dmolinagarcia/nova64/docs/tracks/hid.md

---
layout: track
track: hid
title: "Track · HID"
permalink: /tracks/hid/
redirect_from: /categories/hid
---
