dmolinagarcia/nova64/docs/tracks/memory.md

---
layout: track
track: memory
title: "Track · Memory"
permalink: /tracks/memory/
redirect_from: /categories/memory
---
