dmolinagarcia/nova64/docs/tracks/power.md

---
layout: track
track: power
title: "Track · Power"
permalink: /tracks/power/
redirect_from: /categories/power
---
