dmolinagarcia/nova64/docs/tracks/storage.md

---
layout: track
track: storage
title: "Track · Storage"
permalink: /tracks/storage/
redirect_from: /categories/storage
---
