dmolinagarcia/nova64/docs/tracks/system.md

---
layout: track
track: system
title: "Track · System"
permalink: /tracks/system/
redirect_from: /categories/system
---
