dmolinagarcia/nova64/docs/tracks/video.md

---
layout: track
track: video
title: "Track · Video"
permalink: /tracks/video/
redirect_from: /categories/video
---
