dmolinagarcia/nova64/docs/_drafts/0001-xx-xx-power-button.md

---
categories: power
---

## Power Button

Cmo encendemos apagamos? ATX?

Can I use the soft button from the IP????

It seems I can

>>> Pero.... quiero un boton que no dependa de ningun MCU

Circuito puramente analogico. Un boton enciende (activa el enable de los reguladores)
                              Boton largo apaga (desactiva el enable)

Ademas, el pulsado del botón, se envia como señal al nova, para que invoque un apagado
Y ademas, el nova tiene que tener un power off!

Metemos aqui todo el diseño del boton
