dmolinagarcia/nova64/docs/_drafts/0004-xx-xx-prototype_board.md

---
categories: cpu
---

que necesito para una prototipe?

2 fpga
cpu
2x2 qram
1 sram
all pins exposed

power?
