dmolinagarcia/nova64/docs/docsV3/content/sec_ai_q.md

# Decision log · open questions
> what was decided, why · what's left to close

The decisions shaping the current design, with their reasoning in one line — and the honest list of what's still open.

- D01 — ECP5 → **3× iCE40 TQ144** — BGA isn't hand-solderable; 0.5mm TQFP is. Accepted consequence: 128 Kbit EBR → HW walker + small TLB instead of on-chip tables.
- D02 — [[!superseded by D13/D15]] Main PSRAM **removed**; the 32 MB SDRAM is *the* memory — the QSPI gateware (the trickiest part) disappears, and a cache miss drops from ~µs to ~200–300 ns.
  NOTE: The removal stands and now covers the whole board, but its headline no longer holds: with the SRAM narrowed to 8 bits a fill is back in the µs range (D15). The decision survives on the gateware simplification alone.
- D03 — [[!superseded by D15]] External table SRAM **removed**; a single 2 MB SRAM (cache + tables + pinned) — ~35 pins that didn't fit in the TQ144.
- D04 — Amiga-style shared bus; out goes the dedicated FPGA-to-FPGA link and the eDP bridge — Neon taps the bus with the `$FE` window.
- D05 — Direct RGB-TTL 10.1” panel (ER-TFT101-1) — no bridge chip, no NDA (RTD2556 ruled out due to Realtek firmware). eDP/ANX6345 remains a future variant.
  NOTE: **This choice is size-bound, and that is the thing to know about it.** Parallel RGB-TTL exists only up to roughly 10 inches; from 14 inches upward every panel is a laptop panel speaking LVDS or eDP, and the direct path is simply gone (→ [Q23](sec_ai_q#q23)).
  NOTE: **Half of this decision is now withdrawn and the other half is in dispute.** [D70](sec_ai_q#d70) closes the eDP/ANX6345 variant outright — the bridge has no franchised distribution and no hand-solderable member exists — and replaces it with **LVDS**, which the note above did not consider because it assumed a bridge was the only way off parallel RGB. **What is left open is whether the 10.1-inch module survives as the prototype panel** while [sheet U1](sec_ai_u1) describes the production one, or whether it is superseded outright (→ [Q145](sec_ai_q#q145)).
- D06 — [[!superseded by D13/D35]] 512×300 → 1024×600 px-doubling — the framebuffer fits within the video PSRAM's budget and its QSPI bandwidth.
  NOTE: **Closed by [D35](sec_ai_q#d35).** Px-doubling is no longer a property of the machine: it is **Mode 2b**, one of three video modes, with 2×2 replication filling the panel exactly. The GUI gets native 1024×600 in Mode 1 and games get replication in Mode 2, instead of every subsystem paying for one compromise (→ [T1.33](sec_ai_t1#t133)).
- D07 — USB-only HID — out go PS/2 and keyboard matrix. Capacitive GT911 touch: the resistive option needed 4 ADCs the EC doesn't have free.
  NOTE: **The mechanism underneath it changed and the decision did not.** REV A put the host on the EC's PIO blocks because the RP2040 had no hardware host controller; the RP2354B has one, and the bit-banged stack leaves the critical path along with the pin-placement rule it imposed ([D1.8](sec_ai_d1#d18), [D1.9](sec_ai_d1#d19)).
- D08 — SD as the only boot path; dedicated BIOS flash **removed** — incompatible with the pin budget after adding the SDRAM. **Superseded by [D60](sec_ai_q#d60)**: the conclusion that no *dedicated* flash is affordable still holds, but the EC's in-package flash turned out to have room for the BIOS and all three bitstreams at zero BOM cost, so the SD is no longer any part of the boot path.
- D09 — Boosts (backlight, host VBUS) hanging off SYS, not VBAT — the machine runs on USB with the battery depleted. VPP 2.5V via BAT54: out goes the dedicated rail.
  NOTE: Both halves survive REV C, the second with its footing changed: the BAT54 now hangs off **3V3_MAIN**, which rises after the cores, so the iCE40's `VPP_2V5` ordering is satisfied by construction instead of being violated by it (→ [D20](sec_ai_q#d20)).
- D10 — Full 2 KB paging per process (out goes the "one bank per process" model) — a tractable 32 KB flat table, decoupled from the cache's 256 B fill granularity.
- D11 — Hardware walker instead of a software trap on TLB miss — with 10 ns SRAM it costs ≈100 ns and simplifies the kernel.
- D12 — 32-bit PTE with a 16-bit frame from day one — 128 MB ceiling with no format migrations. 16 rather than the 15 bits the pool needs is free: the flags occupy exactly 16 bits, so the other half-word was going unused, and the clean split lets the walker read 32 bits and take the low half as address and the high half as permissions with no shifting or masking (→ [sheet K](sec_ai_k)).
- D13 — PSRAM eliminated from the **entire board**, Neon's framebuffer included — every QSPI interface disappears with it. Neon gets its own 64 MB SDRAM instead: same part, same footprint, same controller as Helium's.
  NOTE: Streaming pixels across a link would need ~26 MB/s sustained with hard deadlines and would make Helium the bottleneck for the whole machine. A second SDRAM device costs the same pins as any smaller memory and buys double buffering at 16 bpp.
- D14 — SDRAM sized at **64 MB per device** (AS4C32M16SB-7TIN, 512 Mbit) — the ceiling of SDR silicon in volume; no 1 Gbit part exists. The 256 Mbit W9825G6KH stays as a drop-in fallback on the same footprint. **The second device is deliberately not populated**: at 8 MHz the 65816 sustains ~4 MB/s, so merely zeroing 64 MB takes ~16 s. A second /CS is routed to an empty footprint.
- D15 — SRAM narrowed to **1 MB ×8** with D0–D7 *and* A0–A10 shared with the CPU nets — 13 pins instead of 41, which is what makes the budget close at 90/107. Possible only because A0–A10 are the untranslated page offset (→ [F.2](sec_ai_f#f2)). Accepted costs: Helium can no longer reach the SRAM alone, walks cost four accesses instead of two, and the shared nets carry three loads.
- D16 — Cache misses handled by **stalling PHI2 low**, not by ABORT — the W65C816S core is fully static and the WDC datasheet sanctions holding the clock indefinitely. ABORTB is retained for genuine protection faults only, which removes the frequent case from the most delicate path on the chip.
  NOTE: Clock gating was also preferred over the RDY pin for a specific reason: RDY is reported to be ignored during write cycles on some revisions, a 6502 NMOS inheritance. Gating the clock sidesteps the question — with PHI2 stopped the CPU is not in any state at all, rather than in one whose rules depend on the cycle type.
- D17 — The SRAM is a **hardware cache with tags**, never a tier of allocatable frames — migrating a page would force hardware to rewrite PTEs, which `mshare` and TLB coherence make impossible (→ [L.3](sec_ai_l#l3)). 768 KB of 4-way cache in 2 KB lines with 256 B sub-blocks, plus 256 KB fixed and uncached.
- D18 — Debug access goes through a **debug agent inside Helium**, commanded by the RP2354B over a dedicated SPI chip select — the EC never masters the system bus. Pins (mastering needs ~32 lines the EC does not have), reuse (Helium already owns every memory controller) and coherence (an external master reads stale data past a dirty sub-block) all point the same way, and the agent's own registers stay **out of bank `$FF`** so the privileged path cannot be reached by the software it can bypass (→ [sheet R](sec_ai_r)).
  NOTE: Helium also drives `BE` as part of this: the bus handoff has to be a synchronous transition inside one clock domain, not a race across the SPI link. Closes [Q25](sec_ai_q#q25).
- D19 — **3V3 split into an always-on rail and a switched one** — the decision the rest of the power revision hangs from. A controller cannot switch the rail that powers it, so REV B's single 3V3 made EC power management impossible in principle rather than merely unimplemented. Accepted costs: one extra converter, and a domain boundary that has to be honoured net by net (→ [C.2](sec_ai_c#c2), [C.13](sec_ai_c#c13)).
- D20 — **1.2 V becomes a buck sourced from SYS**, not an LDO off 3V3. Two problems fall out together: the iCE40 wants VCC before VCCIO and an LDO off 3V3 guarantees the opposite, and dropping 3.3 → 1.2 V linearly at 250 mA burned ~0.5 W as heat in a SOT-23-5 on a battery machine. ~0.6 W recovered, and the ordering becomes structural rather than a firmware promise (→ [C.8](sec_ai_c#c8)).
  NOTE: The rejected mitigation is worth recording so it is not proposed again: **holding `CRESET_B` low does not make a rail-order violation safe.** It prevents configuration, not conduction through the I/O clamps into an unpowered core rail.
- D21 — **MCP73871 → BQ25896 + CH224K**, and the pack to 2× 5000 mAh in parallel. The pack grew to ~10 Ah and linear charging at that current is not viable; a switching charger at 90–92 % with a programmable SYS floor and an integrated ADC also hands the EC rail telemetry for free. The CH224K negotiates **9 V** — not 12 V, which leaves no headroom under the charger's 14 V input OVP.
  NOTE: The charger's **OTG boost cannot replace the TPS61023** for the host port, and an earlier proposal that it could was wrong twice over: the boost drives VBUS, the same physical node as the USB-C input, and it only enables while unplugged (→ [C.5](sec_ai_c#c5)).
- D22 — **Two level-held pins plus the existing SPI link** for the CPU↔EC power handshake: the pins carry attention, SPI carries the reason. A single wire encoding poweroff, reboot, ack and refusal by pulse width would be a bug source on a board where both endpoints are also under test. Costs 2 of Helium's spare I/O, onto a budget that does not close (→ [Q8](sec_ai_q#q8), [S.2](sec_ai_s#s2)).
  NOTE: `POWER_CTRL` is also the one register that departs from the "address as opcode" model of [M.2](sec_ai_m#m2) — a small closed enumeration with no arguments is cheaper to decode by value than to spread over eight addresses. The departure is deliberate and confined to this block.
- D23 — **No `sys_poweroff()`.** Power management adds nothing to the syscall table; it is `/dev/power` and an `ioctl`, and the privilege check comes free from the device node's permissions rather than from a bespoke gate. A single-purpose syscall in a table otherwise built from general primitives would have been the first crack in the rule (→ [S.11](sec_ai_s#s11), [J.4](sec_ai_j#j4)).
- D24 — **Battery telemetry as double-buffered registers inside Helium**, staging → live → shadow, each copy a single cycle. Two cheaper designs were rejected: a **seqlock**, which moves retry logic onto the constrained CPU with no hard bound; and letting the EC **write telemetry into SRAM** over the debug agent's bus path, which would make battery reporting depend on the cache controller and the arbiter — the one thing the power subsystem is specified not to do (→ [S.16](sec_ai_s#s16)).
- D25 — [[open]] **The power registers sit outside the `DEBUG_ENABLE` gate** — for as long as there is a gate ([Q125](sec_ai_q#q125)).  Shutdown and battery reporting are production functions; gating them behind the debug strap would break them on every board built with debug disabled. They are read-only from SPI and cannot initiate a bus cycle, so the exception grants nothing the strap exists to withhold (→ [R.18](sec_ai_r#r18)). **If [Q125](sec_ai_q#q125) removes the strap this entry has nothing left to except them from**, and the always-accessible region of [Q38](sec_ai_q#q38) becomes simply the register map.
- D26 — **Neon is specified in full** — three video modes, a blitter, a command processor executing display lists out of its own SDRAM, and a resource budget that closes at 77 % of the device ([sheet T1](sec_ai_t1)). It reconciles REV A against this board, which differs from what REV A assumed in four places: the reference clock, the SDRAM size, the existence of `NEON_BUS_BSY`, and where the interrupt goes.
- D27 — **Mode 0's text buffer and font live in Neon's block RAM, initialised from the bitstream** — not in video memory, and not loaded by anything. 8 KB plus 4 KB of the 16 KB available, which is expensive; it buys a machine that displays a correct screen the moment `CDONE` rises, with no SDRAM controller, no arbiter, no FIFO and no CPU in existence. **The console is therefore available as the debugging instrument for every subsystem built after it**, which is the whole argument (→ [T1.1](sec_ai_t1#t11), [T1.29](sec_ai_t1#t129)).
- D28 — **One clock domain inside Neon, at 103.125 MHz**, with the pixel stage on a clock enable every second cycle and `PCLK` out through a DDR register. No clock-domain crossing anywhere, so no synchroniser FIFO between scanout and memory and an entire class of intermittent failure removed. **The second PLL is freed** and has two claimants, audio and the VGA bring-up clock (→ [T1.8](sec_ai_t1#t18), [Q54](sec_ai_q#q54)).
  NOTE: REV A's 102.000 MHz is unreachable from this board's 25 MHz oscillator; 103.125 is the nearest legal PLL setting and the vertical total moves 635 → 640 to land back at ~60 Hz (→ [Q43](sec_ai_q#q43)).
- D29 — **No hardware tile engine and no sprite engine.** The blitter redraws a full 320×200 tilemap in ~1.3 ms, under 8 % of a frame, and blits 32 masked 16×16 sprites in ~0.12 ms; hardware sprites exist to avoid save/restore of background on machines that cannot afford to redraw, and with double buffering and 64 MB that problem does not arise. **Saving ~1,650 LUT, about 21 % of the device** — which is what takes Neon from 95 % occupancy, not routable once audio grows, to 77 %. **The hardware cursor is retained**, because a GUI pointer must track the mouse independently of the rendering loop (→ [T1.44](sec_ai_t1#t144)).
  NOTE: The trade is real and is recorded so it is not re-litigated. What is given up: sprites composited at scanout cost no framebuffer bandwidth and cannot be erased by drawing. What is gained: one rendering model instead of two incompatible paths, and the logic budget to fit the blitter, the command processor and audio on one device.
- D30 — **Blitter commands carry `(x, y)` coordinates, not 24-bit addresses.** Computing `base + y × stride + x` on the 65816 is a shift-and-add per object per frame on a CPU with no multiplier — precisely the work this architecture exists to remove. Neon does it instead, at one sequential multiply per command, ~16 clocks and ~80 LUT. The consequence is larger than the cause: **a destination becomes one 32-bit word, so moving an object is a single patch to an existing display list**, which is what makes per-frame CPU cost ~180 bytes instead of several milliseconds (→ [T1.42](sec_ai_t1#t142)).
- D31 — [[!superseded by D36]] **Neon's registers live at `$FE:FF00`, inside the aperture, not in bank `$FF`.** Neon already decodes bank `$FE`; giving it a second window in the privileged bank would cost a decode in Helium and a wall on [Q22](sec_ai_q#q22) for nothing.
  NOTE: The half of this that survives is the **palette**, which stays in the aperture at `$FE:8000` with 256 entries — it is bulk data, written a kilobyte at a time, and nothing about it is privileged (→ [T1.49](sec_ai_t1#t149)). The half that was wrong is "for nothing": a second window buys the protection property of [D36](sec_ai_q#d36), which is not nothing.
- D32 — **`PEEK` is deleted; the graphics aperture is readable.** REV A made it write-only, with a slow address/data register pair for diagnostic reads, on the premise that Neon could not stall the CPU. **`NEON_BUS_BSY` already exists** ([B.6](sec_ai_b#b6)) and stalls PHI2 across the row activation, so a read simply works at a few hundred nanoseconds — about six times faster than the mechanism it replaces, and with no register file to build. Its protocol is [D37](sec_ai_q#d37). **The software model is still written as though the aperture were write-only**, because nothing in the design needs to read pixels and anything that does will run at aperture speed (→ [T1.15](sec_ai_t1#t115), [T1.16](sec_ai_t1#t116)).
- D33 — **Backlight `EN` and PWM belong to the EC, not to Neon.** The EC is awake before Neon is configured and while the switched domain comes down, and it already owns every rail enable. Closes [Q6](sec_ai_q#q6) and returns two pins to a budget that needs them (→ [T1.52](sec_ai_t1#t152)).
- D34 — **Neon's interrupt goes to Helium's PIC, not to the CPU's `IRQB`.** Masking and priority come free from a controller that already exists, the CPU keeps one interrupt entry path, and it is one pin on each FPGA rather than a wire into the socket. Vblank, raster compare and the display list's `SIGNAL` are aggregated inside Neon and demultiplexed by the kernel reading `IRQ_STATUS` (→ [T1.47](sec_ai_t1#t147)).
- D35 — **Px-doubling becomes Mode 2b.** What [D06](sec_ai_q#d06) proposed as a global policy — draw at 512×300, emit every pixel twice — returns as one mode among three, with 2×2 replication filling the panel exactly. Mode 1 gives the GUI native 1024×600 at 1 bpp and Mode 2 gives games replication at 8 bpp, so no subsystem pays for another's compromise. Supporting 2b alongside 2a costs approximately nothing in logic: it is a register field driving the replication counters and the line stride (→ [T1.33](sec_ai_t1#t133)).
- D36 — **Neon's registers live in bank `$FF`, at `$FF:8000`–`$FF:80FF`**, and bank `$FF` gains its first off-chip tenant. It reverses [D31](sec_ai_q#d31), which had put them inside the `$FE` aperture, and it does so for a reason that outranks the tidiness argument on both sides: **`$FE` is user-mappable and `$FF` is not.** A process granted a framebuffer mapping could otherwise reach `LIST_BASE` and `CMD_CTRL.LIST_RUN` and aim the command processor — which reads and writes the whole 64 MB with no MMU in front of it — anywhere it liked. D31 could only answer that with a rule the mapping ioctl had to remember; **this makes it a property of the architecture**, putting Neon's control surface behind the same wall as the MMU's (→ [T1.21](sec_ai_t1#t121), [J.5](sec_ai_j#j5)).
  NOTE: **It costs no pins and no new mechanism.** Neon already taps A0–A15 and already captures the bank byte off D0–D7 during PHI2 low, so recognising a second bank is the same comparator with a different constant, and `NEON_BUS_SEL` simply broadens to mean "Helium has validated this cycle for Neon" across both windows (→ [B.6](sec_ai_b#b6)).
  NOTE: **The base is `$FF:8000` so Helium's decode is one address bit** — "A15 set in bank `$FF` ⇒ not mine" — rather than a range comparison. Helium keeps `$FF:0000`–`$FF:7FFF` whole, so the block allocation [Q22](sec_ai_q#q22) still owes can proceed with no risk of colliding with Neon later. The genuinely new gateware is small and specific: **Helium must release D0–D7 on a read in that window**, which is the same turnaround an `$FE` read already performs, and **Neon must gate on the strobe rather than on the address alone** — ABORTB cancels an instruction on the CPU, it cannot un-write a register on the far side of the bus. No stall is needed: the file is fabric registers and answers inside the PHI2 high phase (→ [T1.23](sec_ai_t1#t123)).
- D37 — **The CPU can read VRAM, through a bus-busy stall — and the protocol is "stall first, ask afterwards".** `NEON_BUS_SEL` selects Neon's bus; while `NEON_BUS_BSY` is asserted Helium holds PHI2 **low**; when Neon deasserts it the data is in Neon's output register and Helium raises the clock. The alternative — Neon asserting a wait line fast enough to hold off the rising edge — is a race inside a ~62 ns low phase across an asynchronous inter-FPGA crossing, and it is unnecessary: **Helium decodes the bank itself, so it knows a read of `$FE` is in progress without being told.** It stalls unconditionally and the race disappears (→ [T1.18](sec_ai_t1#t118), [B.6](sec_ai_b#b6)).
  NOTE: **Stalling low rather than stretching the high phase is what keeps it cheap.** Extending the high phase would need a fresh datasheet reading on holding a static W65C816S with the clock high, which nobody has done; stalling low reuses the exact clock gate Helium owns for cache fills and the permission [D16](sec_ai_q#d16) already established. It also falls out right on the bus, since D0–D7 carries the bank byte while PHI2 is low and Neon therefore must not drive then.
  NOTE: **Four requirements travel with the decision**, and the first would otherwise ship as an intermittent bug. **A read drains the write FIFO before it is issued** — writes are posted, so a read that overtakes a pending write returns the previous contents, failing according to arbiter load, which means "read back what was written" would pass almost every time. **The arbiter bounds the wait** — a row activation is ~60 ns and irrelevant, a read queued behind a whole blitter operation is up to 1.5 ms with the CPU clock stopped (→ [Q29](sec_ai_q#q29)). **Helium's fill watchdog covers the path** (→ [F.11](sec_ai_f#f11), [Q57](sec_ai_q#q57)). And **the software model stays write-only**, because the restriction was doing real work: it is why save-under is a blitter copy and why assets flow one way (→ [T1.19](sec_ai_t1#t119)).
  NOTE: **The same wire serves Helium with no clock involved.** When the debug agent reads VRAM through an external cycle, `BE` is low and there is no PHI2 to stall — Helium just waits for busy to clear before sampling D0–D7. `NEON_BUS_BSY` is a ready line that Helium *happens* to use to gate PHI2 when the requester is the CPU. And it is less slow than it sounds: a read loop runs at ~70 % of the speed of the same loop against SRAM, because the bottleneck is the 65816, not the SDRAM (→ [T1.19](sec_ai_t1#t119)).
- D38 — **Neon's SDRAM is partitioned by function across its four banks**, and this is a first-order decision rather than an allocator preference. Banks 0 and 1 hold the front and back framebuffers, bank 2 the even-numbered window backing stores, bank 3 the odd ones plus the font atlas, icon sheets and audio buffers. **The invariant is that during composition the blitter's reads, its writes and scanout are always in three different banks**, so every ACTIVATE is issued inside another bank's data phase. Collapse it and delivered bandwidth halves, from ~160 to ~80 MB/s — a 2D blit crosses a stride at every line boundary, and a shared bank turns each crossing into a PRECHARGE plus ACTIVATE that overlaps with nothing (→ [T3.16](sec_ai_t3#t316)). **Closes [Q50](sec_ai_q#q50).**
  NOTE: Two obligations come with it. The **controller must map the bank bits to the high address bits**, or the partition cannot be expressed as an address range at all — the obvious alternative of interleaving banks on low bits to spread sequential traffic would destroy the whole policy. And **the kernel's VRAM allocator is no longer free to place a surface wherever it likes**; the partition is part of the interface, not an optimisation it may ignore.
- D39 — **Neon's arbiter is fixed-priority — refresh, scanout, audio, CPU, blitter — with preemption only at burst boundaries and a minimum burst of 8 words.** Scanout is not merely favoured but *shown* to be safe: worst case 23 clocks, **223 ns**, against a 512-word FIFO that a stall of that length drains by 5.8 words. This is the inverse of the Amiga's `BLTPRI`, which let the blitter starve the CPU; here the blitter can starve nothing. **Placing the CPU above the blitter is also what bounds [D37](sec_ai_q#d37)'s read stall** — a read waits for one burst, never for a whole blit (→ [T3.25](sec_ai_t3#t325), [T3.27](sec_ai_t3#t327)). **Closes [Q57](sec_ai_q#q57) and the Neon half of [Q29](sec_ai_q#q29).**
  NOTE: The margin is the point rather than the number. If the clock falls to 51.5625 MHz under [Q44](sec_ai_q#q44)'s fallback, if the burst grows, if audio's demand doubles, the stall stays two orders of magnitude inside the FIFO. **A real-time guarantee resting on an unverified estimate is not a guarantee**, and a scanout underrun has no degradation mode — the line is simply corrupt.
- D40 — **A prototype board is inserted before the target board**, and it is the first schedule decision this log has had to record. Helium and Neon are merged into one ECP5 on a commercial Colorlight i9 module with the CPU, SRAM, EC, VGA and audio on a carrier of our own, so the whole software roadmap runs on real gateware while the KiCad capture proceeds in parallel. **The blocked dependency was serial and is now two tracks**: [Q1](sec_ai_q#q1)'s missing panel datasheet stops the schematic and stopped everything behind it, and it stops nothing on the carrier. Accepted cost: one board that is thrown away, and a discipline section — [P2.12](sec_ai_p2#p212)–[P2.18](sec_ai_p2#p218) — that has to be enforced at every merge or the prototype becomes a rewrite (→ [sheet P2](sec_ai_p2)).
  NOTE: **[D73](sec_ai_q#d73) puts a third phase in front of this one.** A Spartan-6 training rig now precedes the carrier, so what this decision describes is Phase 1 of three rather than the first hardware the project touches. The reasoning is unchanged and the rig gates nothing ([sheet P1](sec_ai_p1)).
  NOTE: The reason the trade is worth taking is asymmetric, not marginal. A gateware defect found on the carrier costs a bitstream rebuild; the same defect found after E1.3 costs a board spin, and the parts of the design most likely to carry defects — MMU, cache, arbiter, blitter, compositor — are precisely the parts that need no board-specific silicon to exercise.
- D41 — **One i9 module, not two.** Two modules would give Helium and Neon separate SDRAM, which is the target topology, but each is locked at 8 MB with no expansion path and the pair doubles cost, carrier complexity and the inter-module wiring. One module reaches the same software milestones, and the topology difference is handled where it belongs — as a leak-table row and [P2.15](sec_ai_p2#p215)'s memory-port abstraction, which is a discipline problem rather than a hardware one.
- D42 — **VGA through an R-2R ladder, not HDMI.** An earlier costing attributed an HDMI connector to the i9 extension board; it belongs to a Muse Lab board for the i5, a different product. The correction is an improvement rather than a loss: a TMDS encoder is 400–600 LUT of gateware that the target board deletes, whereas 6-bit-per-channel VGA is 20 pins from a budget with 24 spare and lands on **exactly the 18-bit palette entry the target panel takes** ([D05](sec_ai_q#d05), [P2.16](sec_ai_p2#p216)). One less thing built here that has to be unbuilt there.
- D43 — **The prototype carries the target's 1 MB ×8 SRAM, not a ×16 part.** An earlier costing for the carrier specified an IS61WV102416 with UB/LB. That re-widens what [D15](sec_ai_q#d15) deliberately narrowed and would have the carrier rehearse a byte-lane topology the target does not have — while claiming, in the same paragraph, to be rehearsing the shared-net trick of [F.2](sec_ai_f#f2) that only exists because the part is ×8. The AS7C38096A-10TIN of [F.5](sec_ai_f#f5) goes on both boards.
- D44 — **Mode 0 geometry stays 128 × 32 on both boards; the prototype letterboxes instead of reflowing.** At 640 × 480 the console shows an 80 × 30 window into the same buffer, with [T1.25](sec_ai_t1#t125)'s `TEXT_START + text_row*128 + column` unchanged; at 1024 × 600 all 128 columns fit exactly and the 32 rows sit inside a vertical border. **Making the geometry a synthesis parameter was the alternative and was rejected**: it adds a configuration axis the target never uses, and it forces the console driver and every scrollback consumer to ask the hardware how wide the screen is (→ [P1](sec_ai_p2#p1)).
- D45 — **The SPI-SD controller gets a register block of its own, with two data paths and a plain register file rather than address-as-opcode.** The card is unreachable from software until it has one, and the shape of it follows from what it has to carry: LBA, a physical destination and status are **state that persists between commands**, which is exactly the case [M.2](sec_ai_m#m2)'s address-as-opcode convention does not cover — that convention applies to the four triggers, whose argument is a block count, and to nothing else. Both a **FIFO path** and a **DMA path** are specified, because the FIFO reaches [E6](sec_ai_p3#e6) without touching the arbiter or the cache and demand paging cannot use it: 512 bytes through the accumulator is ~440 µs of CPU at 8 MHz against 164 µs of SPI, and a FIFO-only design retracts [G.1](sec_ai_g#g1)'s reason for putting the card behind Helium in the first place. Card initialisation stays in software behind a raw-command register, per [B.2](sec_ai_b#b2) (→ [sheet G](sec_ai_g)).
  NOTE: **The DMA path is what forces `CACHE_INVAL_FRAME` into [sheet M](sec_ai_m)**, and that command is the part of this decision most likely to be skipped by whoever writes the gateware first. Helium acquires a second bus master writing SDRAM behind a write-back cache, and the dirty line left over the destination frame is not a staleness bug but a delayed overwrite of correct data (→ [M.12](sec_ai_m#m12), [G.9](sec_ai_g#g9)).
- D46 — **The expansion slot is a second instance of the inter-device contract, not a second bus.** A card gets `/EXP_SEL_n`, `/EXP_BSY` and `/EXP_IRQ`, [T1.18](sec_ai_t1#t118)'s stall-first read protocol and [F.11](sec_ai_f#f11)'s watchdog — the same shape Neon has, which is what [Q56](sec_ai_q#q56) chose the names for. **One polarity is deliberately reversed**: `/EXP_BSY` idles *not busy*, because busy-by-default in a slot means a machine with nothing plugged in does not boot, and the race that polarity was defending against is killed instead by a mandatory stall window before Helium starts sampling. Cost: **three pins for the first slot, one for each after it**, with the bank byte demultiplexed by a '573 on the board and the slot buffered off the CPU nets by a '245 — both of which cost packages rather than FPGA pins (→ [sheet X](sec_ai_x), [X.11](sec_ai_x#x11)).
- D47 — **A card is reachable in two spaces and neither costs a pin.** Control is a 256-byte window in bank `$FF`, which inherits [L.10](sec_ai_l#l10)'s keystone — no card in any slot is reachable from user code by construction — with Helium decoding the window and the card decoding inside it, exactly as [T1.21](sec_ai_t1#t121) splits Neon's. Bulk is a **1 MB aperture per slot carved out of the frame numbers [F.10](sec_ai_f#f10) deliberately leaves unpopulated**, so a PTE can name a card with the TLB and the permission bits still in front of it; the address reaches the connector on A11–A19, which Helium already drives and which are idle while the SRAM's `/CE` is ([F.2](sec_ai_f#f2)). Aperture frames are non-cacheable and the gateware enforces it rather than trusting the PTE flag (→ [X.8](sec_ai_x#x8), [X.9](sec_ai_x#x9)).
- D48 — **No third-party bus mastering, and the reason is coherence rather than arbitration.** [M.12](sec_ai_m#m12)'s rule — invalidate before a read into memory, flush before a write out of it — is honourable by Helium's own SD engine because Helium owns the cache, and is not honourable by a card somebody else designed. DMA stays a privilege of the northbridge; `/EXP_BR` and `/EXP_BG` are routed to the connector and left unconnected at the FPGA, in the same spirit as [F.10](sec_ai_f#f10)'s unpopulated second `/CS` (→ [X.16](sec_ai_x#x16)).
- D49 — **The slow tier is a third I2C bus with Helium as its only master, and its windows are mirrors rather than proxies.** `I2C-EXP` avoids multi-master arbitration on either existing bus — [C.13](sec_ai_c#c13)'s R3 forbids a bus with two masters, not a third bus — and its two pins have been in [Q8](sec_ai_q#q8)'s allocation since before the split left them without a device. A window cannot perform the transaction on demand: a byte over I2C is ~90 µs at 100 kHz against a 125 ns bus cycle, three orders of magnitude past what [M.6](sec_ai_m#m6) permits to stall PHI2. So each window is a copy in block RAM refreshed by a sequencer, using **[S.16](sec_ai_s#s16)'s staging → live → shadow mechanism with a device table in front of it** — the atomicity and staleness properties come along unchanged (→ [X.23](sec_ai_x#x23), [X.24](sec_ai_x#x24)).
- D50 — **The embedded controller becomes a single RP2354B, and what makes it the right part is what it deletes rather than what it adds.** **48 GPIO** retires the MCP23017 that [D1.6](sec_ai_d1#d16) needed and with it the awkward question of which power domain an expander driving always-on enables belongs to ([Q41](sec_ai_q#q41)). **2 MB of flash inside the package** removes a component from the always-on rail and a net from the board. **A hardware USB host controller** removes the bit-banged PIO stack from the critical path, along with its rule that `D+` and `D−` sit on consecutive GPIOs. The cost is paid in one place and paid fully: **committing the native controller to host mode makes `BOOTSEL` over USB structurally unavailable**, because a USB-A receptacle sources VBUS and reaching it from a PC would need two supplies opposing each other — so the one recovery path that needed no header is replaced by three that need no USB (→ [sheet D1](sec_ai_d1), [D1.9](sec_ai_d1#d19), [D1.13](sec_ai_d1#d113)).
  NOTE: The console follows the port. There is no device-mode USB, so the USB-CDC half of [R.19](sec_ai_r#r19)'s mirrored console is gone and the console is the UART on `J-DBG` — the same 5-pin header that carries SWD, serviced by one probe over one cable.
- D51 — **NVFS breaks its own format rather than keeping ordering discipline, and the break is accepted on the strength of five changes.** A **journal** replaces write ordering, because ordering is a correctness argument spread across every mutating operation — which is where draft 2's crash harness found its bugs — and a journal is one argument in one place, with idempotent single-pass recovery on a machine that has no on-target `fsck`. A **2048-byte block equal to the MMU page** makes demand-paging an executable exactly one block read and every index a shift. **Extents** remove the indirect-block read at ~2.5 ms each. **Fixed 64-byte directory slots** remove the in-band length field that is the largest single source of directory corruption in this class of filesystem — a cost [Y3.10](sec_ai_y3#y310) still pays. And **POSIX-identical mode and type encodings** remove every translation table from both drivers and from the layer above. The price is `mkfs`, `nvfsck` and the read-path driver rewritten, and every existing volume evacuated by copy (→ [sheet Y2](sec_ai_y2), [Y2.1](sec_ai_y2#y21)).
  NOTE: **One action has to happen before any draft 3 code is written**: tag and archive the draft 2 tooling, because evacuating a draft 2 volume depends on it and there will be no way to reconstruct it afterwards.
- D52 — **The media contract: one MBR primary partition of type `0x7F`, starting at an LBA that is a multiple of four, and no wear levelling of our own.** `0x7F` is the byte reserved for local and experimental use; **`0x7A` and `0x7B`, which an earlier draft proposed, are unsafe** — they are the hidden-variant aliases of two FAT16 types under the +`0x10` convention, so some host tools would silently treat an NVFS partition as a hidden FAT. The alignment makes one NVFS block exactly four sectors, and `mkfs` **refuses** an unaligned partition rather than working around it, because working around it turns every transfer into two. Erase-block management and wear levelling belong to the card's own translation layer, and NVFS issues no discard (→ [Y2.25](sec_ai_y2#y225)).
- D53 — **A VFS layer exists, and it is specified before the second filesystem is implemented rather than after.** Introducing it now costs one module and a mechanical rework of NVFS's call surface; introducing it after ext2 costs the same rework twice plus a syscall layer that has already grown branches. Its shape is decided by what neither driver can do: **`lookup` returns an identifier and never a vnode**, because a driver cannot know what is cached or what mount is grafted onto the result; **path resolution, symlink following and mount crossing are VFS-owned**, because neither driver can see across a mount boundary; and **the vnode cache is VFS-owned**, because two copies of one inode diverge silently on append and the logic is identical in both drivers. **The locking discipline is written now and compiles to nothing until the Amiga milestone** — retrofitting locking into a vnode cache fails intermittently rather than cleanly (→ [sheet Y1](sec_ai_y1)).
- D54 — **ext2 is the interoperability format and is a transfer medium, not the system volume.** Chosen over FAT32 for reasons that are all about this CPU: **little-endian on disk**, so every field is a direct load with no byte-swap path; a small documented structure set with no chain to walk; a real directory tree with permissions, links and symlinks; and no long-filename encoding layer. **The recommendation is read-only** — gates [E2.0](sec_ai_y3#e20) and [E2.1](sec_ai_y3#e21) — because that covers the actual use case at roughly a quarter of the cost and with none of the corruption risk, while the write path adds the allocators, truncation, the counter invariants and the whole ordering discipline ext2 has no journal to replace (→ [sheet Y3](sec_ai_y3), [Q101](sec_ai_q#q101)).
- D55 — **One block cache below the VFS, not one per driver, with a sequence-number hook for the journal.** Two caches means two pools sized by guesswork, no global LRU, and one mount's buffers idle while the other thrashes. Uniform 2048-byte buffers, of which an ext2 mount uses half — 50 % waste while an ext2 mount is active, accepted because ext2 is a transfer medium and a two-size allocator costs more code than the memory it saves. **A `commit_seq` per buffer and a `flushed_seq` per mount** stop a global LRU from writing a metadata block back before its journal record has committed, which a naive shared cache would do at an arbitrary moment and break silently. Four bytes per buffer and one comparison in the eviction path (→ [Y1.14](sec_ai_y1#y114), [Q91](sec_ai_q#q91)).
- D56 — **The filesystem stack is prototyped on a host PC before it is written for this machine, as a third series that blocks nothing.** Three filesystems behind one internal table is the cheapest way to discover what [D53](sec_ai_q#d53)'s interface actually has to be, and a bug found under a debugger and a sanitizer is a bug not found on a 65816 with a serial console. **FAT32 first, then ext2, then NVFS; every read path before any write path** — so that a bad decision in the shared layers is caught before it has been baked into three write paths (→ [Y4.2](sec_ai_y4#y42), [sheet Y4](sec_ai_y4)).
- D57 — **The debug and programming port is an on-board RP2040 CMSIS-DAP probe on a chassis USB-C receptacle, not a header and not an FTDI bridge.** The EC's only USB controller is host ([D1.9](sec_ai_d1#d19)), so there was no path from a development PC to the EC at all; an internal header keeps the machine open on the bench, and **the FT2232H was rejected on evidence** — SWD is not native to MPSSE, RP2350 needs SWD *multidrop*, and OpenOCD lists multidrop support for CMSIS-DAP specifically. The failure mode of being wrong is a fabricated board with a dead debug port and no other way in ([D2.2](sec_ai_d2#d22)).
  NOTE: The recursion objection — the probe's own firmware could be corrupted — was overstated: **the RP2040 bootrom is mask ROM**, so `BOOTSEL` and USB enumeration always work whatever the probe's flash holds. The recursion has a hard floor and it is a better one than an FTDI part that may not enumerate a DAP ([D2.3](sec_ai_d2#d23)).
- D58 — **The probe is powered from the debug port's VBUS and the two supply domains never touch.** A probe that depends on a rail of the machine under repair cannot serve the case that justifies it. `3V3_PROBE` and `3V3_AON` are never tied, diode-OR-ed or bridged; **exactly six nets cross, over a common unsplit ground**, and the EC's UART TX — the only line pointing from the machine into the probe — is **held Hi-Z until `DBG_VBUS_SENSE` says a probe is powered**, because probe-absent is the machine's normal state and 16 mA of continuous backfeed is not ([D2.13](sec_ai_d2#d213), [D2.14](sec_ai_d2#d214)).
- D59 — **Tier 3 is demoted from recovery path to bring-up diagnostic, tier 2 is deprioritised, and the `J-QSPI` header becomes test pads.** Tier 1 recovers a blank flash, a corrupt flash, an unpowered machine and a self-resetting one, which leaves tier 3 almost no recovery territory — what it keeps is the E0 assembly check that no other tier can make: **JEDEC ID read with `RUN` low proves rails, QFN-80 joints and QSPI continuity without probe firmware or OpenOCD**. The six pads therefore sit beside the package with **no connector and no probe connection**, and if layout cannot keep the stubs to a few millimetres **tier 3 is dropped outright rather than reopened** ([D2.22](sec_ai_d2#d222), [D2.23](sec_ai_d2#d223)).
- D60 — **The bitstreams and `bios.bin` live in the EC's in-package flash, and the microSD is Helium's permanently.** Three HX8K bitstreams are ~135 KB each against 2 MB in the package, so the whole configuration store fits twice over with room for EC firmware ([D1.21](sec_ai_d1#d121)). **This reverses [Q26](sec_ai_q#q26) and supersedes [D08](sec_ai_q#d08)** — not because the earlier reasoning was wrong but because it never did the arithmetic; Q26 asked whether the flash should *grow* to hold these things and answered no, without noticing they already fit. What it deletes: **the '3257 mux and its six EC pins, the SD ownership handoff with its atomicity requirement and its state machine, the SD driver and filesystem in EC firmware, and the card from the critical boot path** ([G.1](sec_ai_g#g1)). What it buys: **a machine that boots with the slot empty and says so on its own screen** ([D1.23](sec_ai_d1#d123)).
- D61 — **FPGA configuration is SPI slave with the EC as sole master, and JTAG was never available to choose against.** The iCE40 LP/HX family has **no JTAG interface at all** — no TAP, no boundary scan, no IDCODE — and the headers labelled "JTAG" on some evaluation boards are documentation residue. **The consequences are accepted because there is no alternative**: no electrical verification of device presence or identity, no boundary scan of solder joints before working gateware exists, and `CDONE` as the only status indication there is ([D3.6](sec_ai_d3#d36)).
- D62 — **NVCM and dedicated per-FPGA flash both rejected.** NVCM is one-time-programmable — closer to fuses than flash — so it is unusable for a design that will iterate, and open-toolchain support for it is uncertain besides. **Dedicated SPI flash per FPGA** adds three parts and their routing to solve a problem the EC's flash already solves at zero BOM cost; **one shared flash in master mode** additionally depends on the `CBSEL` cold-boot multi-image feature and still needs the same staggered `CRESET_B` release, so it removes no complexity in exchange ([D1.21](sec_ai_d1#d121)).
- D63 — **Configuration and the runtime link share one physical SPI bus, distinguished by chip select**, which iCE40 makes possible by reverting configuration pins to user I/O after `CDONE`. It costs two disciplines that must be designed in rather than discovered: **Helium tri-states its SPI pins whenever the runtime select is inactive**, and **the EC honours the 49-cycle post-`CDONE` window before configuring the next device** ([D3.4](sec_ai_d3#d34), [D3.5](sec_ai_d3#d35)). **Both disciplines survive REV C with one select instead of two**, and the merge this decision declined is now settled in both directions: `DBG_CSN` is withdrawn and the pin taken that way ([D80](sec_ai_q#d80)), while reuse of `CFG_SS_A` as the runtime select is rejected outright on the `SPI_SS_B` master-mode hazard rather than on diagnosis ([D86](sec_ai_q#d86), [D3.8](sec_ai_d3#d38)).
- D64 — **The EC is not a bus master, and "the SPI link is the only connection" is true in the data plane only.** It never drives the 65816's address, data or control lines; everything it originates reaches memory through Helium as a peer of the CPU port. **In the control and power planes the claim is false and this document stops repeating it** — chip selects, `CRESET_B`, `CDONE` and `RESB` cross, and the EC owns rail sequencing outright ([D3.1](sec_ai_d3#d31)).
- D65 — **Field update is optional, uses A/B slots, and EC firmware is inside the scheme.** The primary programming path throughout development stays USB → probe → SWD ([D59](sec_ai_q#d59)); self-update is an exercise in making the machine self-sustaining rather than a requirement. **An earlier revision excluded the EC's own firmware because a failed update meant opening the chassis, and the integrated probe removed that objection** ([D1.24](sec_ai_d1#d124), [D57](sec_ai_q#d57)).
- D66 — **The human debug entry point is the UART into the EC, and the EC interprets rather than bridges.** It parses text commands, issues Debug Agent transactions and formats results as text; **nobody speaks to Helium directly.** That buys no framing protocol on the UART, a SPI-side protocol free to be as terse as it likes, and a bring-up that needs only a serial terminal — at the cost of several KB of parser in EC firmware ([D3.14](sec_ai_d3#d314)).
- D67 — **The prototype is out of the EC's configuration path entirely.** The Colorlight i9 is programmed from a PC by whatever route is most practical, and **if an EC is present on the carrier at all, FPGA configuration does not depend on it.** The prototype is ECP5 and the target is iCE40; their configuration mechanisms differ irreducibly, and sharing a path between them would import prototype constraints into production firmware for no benefit ([P2.10](sec_ai_p2#p210)).
- D68 — **The palette becomes a dual-bank table written through a register port, and the mapped palette of [T1.49](sec_ai_t1#t149) is withdrawn.** Two complete banks switch atomically at vertical blanking, so a full reload has no intermediate state and needs no copy; an auto-incrementing index port with two 16-bit data writes per entry loads the table in 513 accesses against the VGA-style protocol's 769, on the resource that is actually scarce. **The cost is a third block RAM against a budget already at 32 of 32**, and that is left open rather than assumed away ([T2.2](sec_ai_t2#t22), [T2.6](sec_ai_t2#t26), [Q133](sec_ai_q#q133)).
- D69 — **Entries are stored as 24-bit RGB888 regardless of the routed output depth, and truncation to 8, 6 or 4 bits per channel is a runtime register field.** A 256 × 24 table costs the same two blocks as a 256 × 18 one, so the wider entry is free — and an 18-bit table would bind the software ABI to the physical routing, so a later board with spare pins would break every binary already written. **RGB444 therefore becomes a software mode rather than a board decision** ([T2.3](sec_ai_t2#t23), [T2.10](sec_ai_t2#t210), [U1.23](sec_ai_u1#u123)).
- D70 — **The panel interface is LVDS, and the eDP bridge variant [D05](sec_ai_q#d05) kept in reserve is closed.** The ANX6345 has no franchised distribution and the whole RGB-to-eDP bridge category is BGA-only, which collides with the project's single declared package restriction ([D01](sec_ai_q#d01)). LVDS inverts all of it: a frozen interface with no link training, a deep multi-sourced panel supply, a hand-solderable TSSOP serializer with a second source, and no EDID to discover ([U1.1](sec_ai_u1#u11), [U1.3](sec_ai_u1#u13), [Q23](sec_ai_q#q23)).
- D71 — **The framebuffer is rendered at half the panel's native resolution in both axes, with a stride fixed at 1024 bytes per line and every panel timing an RTL generic.** Vertical duplication means the DMA fetches each line once and displays it twice, so the saving is fourfold rather than twofold — and at full resolution a Full HD panel would commit 80 % of Neon's SDRAM bandwidth permanently to refreshing the screen. **This is a viability condition, not an optimisation** ([U1.6](sec_ai_u1#u16), [U1.7](sec_ai_u1#u17), [U1.12](sec_ai_u1#u112), [U1.14](sec_ai_u1#u114)).
- D72 — **Where a panel needs dual-channel LVDS, both channels are driven from one shared RGB bus, and the pin boundary carries RGB666.** Horizontal duplication makes the even and odd pixel of each pair identical, and dual-channel LVDS splits by even and odd pixel, so the two serializers can receive the same data, clock and syncs. That holds video to **22 pins** and Neon's pixel clock to 74.25 MHz rather than 148.5. **It depends entirely on the panel splitting by pixel interleave rather than by half-screen** ([U1.16](sec_ai_u1#u116), [U1.17](sec_ai_u1#u117), [U1.20](sec_ai_u1#u120)).
- D73 — **A training rig is inserted before the prototype carrier, and it is not part of noVa64.** A Spartan-6 XC6SLX16 board already on the desk, plus a HAT carrying a CPU socket, a Pico socket, an SD socket and VGA, exercises the SDRAM controller, the 65816 bus interface, PHI2 stalling, the link, the debug agent, Mode 0 text and the SD path before the carrier of [D40](sec_ai_q#d40) exists as a board. **It gates nothing and it is abandoned in place if the carrier arrives first** ([sheet P1](sec_ai_p1), [P1.17](sec_ai_p1#p117)). Accepted cost: a proprietary toolchain on one disposable rig, against [A2.6](sc_a2#a26) — admissible only because no line of its RTL ships ([P1.1](sec_ai_p1#p11), [P1.14](sec_ai_p1#p114)).
- D74 — **The rig's EC is a Raspberry Pi Pico 2, not a bare RP2354B.** The production part is QFN-80 with in-package flash and would need a breakout designed and fabricated, and nothing in the Phase 0 scope depends on the package: the link and the debug agent are protocol and firmware, and pico-sdk is identical across the family. The 2354B-specific properties — 48 GPIO, in-package flash, the A4 stepping — are integration questions no rig can answer. Consequence: the HAT carries a standard Pico 2 footprint ([P1.4](sec_ai_p1#p14)).
- D75 — **On the rig, debug runs over UART and not USB CDC.** A USB HID keyboard makes the Pico a USB *host*, and it has one port: it cannot host the keyboard and present a CDC device to the PC at once. The port serves the keyboard, the console goes to a USB-serial adapter, and Pico-PIO-USB is rejected as a dependency bought for no Phase 0 benefit. The path becomes PC → USB-serial → UART → Pico → SPI → the debug agent, which differs from the target's embedded probe ([sheet D2](sec_ai_d2)) but **preserves the EC-as-interpreter role, which is the part being exercised** ([P1.5](sec_ai_p1#p15)).
- D76 — **The rig's system RAM is served from SDRAM, not from the 72 KB of BRAM that would hold it.** Serving 65816 reads and writes from SDRAM exercises PHI2 stalling under real row activation, precharge and refresh — **the mechanism from which it follows that cycle counting no longer measures time**, and therefore that software needs a frequency reference not derived from PHI2. A BRAM-backed rig would never surface it. Consequence: BRAM is limited to the text framebuffer, the font ROM, the boot ROM and controller FIFOs ([P1.6](sec_ai_p1#p16), [P1.13](sec_ai_p1#p113)).
- D77 — **The SD register block is the transferable artefact and the SPI master RTL is not.** The master is trivial and gets rewritten for iCE40. **The map is [sheet G](sec_ai_g)'s, block-level**: the CPU issues commands against the card and reads whole blocks, and it never drives the SPI byte by byte — byte-level access survives only as an internal test of the master. The rig implements G's PIO subset without the DMA registers, the offsets and the `BUSY` semantics transfer verbatim into Helium, and the 65816 block driver written against them transfers without recompilation. [[!blocking]] **G's register map is reviewed and frozen before the rig's SD RTL is written** ([P1.7](sec_ai_p1#p17)).
- D78 — **Helium has two distinct SPI roles and neither is ever called "Helium's SPI" unqualified.** It is an SPI *slave* to the EC — configuration and the runtime link, discriminated by chip-select — and an SPI *master* to the SD card. Phase 0 exercises the master plus the runtime slave, and never exercises the configuration slave, which is iCE40-specific anyway ([D61](sec_ai_q#d61), [P1.8](sec_ai_p1#p18)).
- D79 — **The rig's text mode is 80 × 30 at 640 × 480, and it is the one geometry decision that does not transfer.** An 8 × 16 font over 640 × 480 fills the active area exactly, and the 25.000 MHz pixel clock is a divide-by-two of a 50 MHz oscillator needing no DCM and no fractional synthesis — monitors tolerate it in place of 25.175 MHz. Framebuffer 4800 bytes. **[D44](sec_ai_q#d44)'s 128 × 32 buffer starts at Phase 1**, where the same 80 × 30 becomes a window into it rather than the screen ([P1.9](sec_ai_p1#p19)).
- D80 — **One runtime chip select, not two: `DBG_CSN` is withdrawn, `MBX_CSN` becomes `LINK_CSN`, and the endpoint is named in a header byte.** `SCK`, `MOSI` and `MISO` were always shared, so the two selects could never be asserted at once — **the second bought addressing rather than concurrency, and a header byte buys addressing more cheaply** ([D3.9](sec_ai_d3#d39), [D3.9a](sec_ai_d3#d39a)). One pin per side, and it is the merge [D63](sec_ai_q#d63) and [Q126](sec_ai_q#q126) held in reserve, taken by design rather than under pin pressure. Area is roughly neutral: one SPI front end, one clock-domain crossing and the `MISO` mux out, the header FSM and two CRC-8 generators in ([R.6](sec_ai_r#r6)).
- D81 — **REV B's security rationale for `DBG_CSN` was overstated, and the correction is recorded as a decision rather than buried in a rename.** The claim was that a second select made *SPI-only, not CPU-visible* a structural guarantee instead of a dispatch convention. **It is a connectivity property, not a decode property**: it holds if and only if the Debug Agent's request port has one source and no CPU-writable register can reach it, which is unaffected by how many chip selects exist. It is restated as **INV-1** and is to be verified structurally ([R.26](sec_ai_r#r26), [D3.2](sec_ai_d3#d32)).
- D82 — **The boot memory load is the Debug Agent, and the `MEM_WRITE` mailbox command class is withdrawn.** Loading `bios.bin` and writing memory from the console are the same operation — a requester in Helium's arbiter writing physical memory through the cache controller — and REV B expressed it twice. **Consequences accepted deliberately**: one fewer requester in the arbiter, every boot exercises the debug write path so it cannot rot unnoticed, a failed load reports a code rather than booting badly — and **the boot path now depends on the Debug Agent state machine** ([R.25](sec_ai_r#r25), [D1.22](sec_ai_d1#d122)). The fallback if that dependency proves too heavy is a write-only sink endpoint at `0x05` using the same payload format (→ [Q154](sec_ai_q#q154)).
- D83 — **Dispatch happens at header completion into a per-endpoint sink, and there is no shared payload buffer.** A shared inbound FIFO with a dispatcher behind it head-of-line blocks in the worst case available: the CPU hangs, the HID queue stops draining, and debug frames queue behind a keystroke exactly when they are needed. **A full endpoint rejects its own frames and affects no other.** The pre-emptive free-space byte in the `MISO` header is what makes the rejection cost three bytes rather than a frame ([D3.12a](sec_ai_d3#d312a)).
- D84 — **`FCRC` on every frame and every endpoint, `HCRC` on every header, and the maximum frame is 259 bytes because `LEN` is one byte.** The header CRC protects the routing decision, which is the catastrophic failure — *a corrupted endpoint byte turns a keystroke into a halt or a memory write*. The frame CRC decides whether anything is committed. **The one-byte length is a latency decision**: 259 bytes bounds the delay one endpoint can impose on another at about 207 µs, where a 16-bit length would let a bulk transfer lock HID out for tens of milliseconds ([D3.11b](sec_ai_d3#d311b), [D3.12a](sec_ai_d3#d312a)). If integrity is ever judged too costly the answer is to raise `SCK`, not to weaken it on a link that carries memory writes.
- D85 — **The router outlives its endpoints: it shares the Debug Agent front end's reset domain and sits in no domain an endpoint can assert.** Otherwise a debug command that resets Helium's system side destroys the transport carrying it. The router survives and answers `NACK_EP_RESET` for whatever is down; its own state clears only on FPGA reconfiguration ([D3.12c](sec_ai_d3#d312c)).
- D86 — **`CFG_SS` lines are parked low after `CDONE` and reuse of `CFG_SS_A` as the runtime select is rejected.** The iCE40 samples `SPI_SS_B` on exit from configuration reset to pick slave or master configuration mode, so a line idling high brings the part up in **master** mode after any unintended reset, driving `SCK` against the EC. Parked low, any accidental reset of any of the three FPGAs falls into slave mode, which is passive — and **Helium's gateware must not drive `CFG_SS_A` after configuration** ([D3.8](sec_ai_d3#d38)). To be confirmed against the vendor configuration guide (→ [Q151](sec_ai_q#q151)).
- D87 — **The NVM32 virtual machine programme is deferred, and the reopening condition is written down rather than left to mood: the kernel executes its first user process, with page faults and syscalls working.** The dependency runs one way — the VM needs a process model, page tables, a loader, a scheduler and a service table from the kernel, and the kernel needs nothing from the VM — so building it first means guessing interfaces that do not exist yet ([VM1.2](sec_ai_vm1#vm12)). The notes are written now so that reopening is implementation rather than redesign.
- D88 — **Argon's role changes from "softcore 65816" to bytecode-native, and the consequence is recorded rather than absorbed: the native 65816 kernel can never run on Argon unless it is also compiled to NVM32.** [E.10](sec_ai_e#e10) already concluded that a 65816 softcore wins little because the ceiling is memory; a bytecode core escapes that ceiling by doing four to six times the work per instruction instead of the same work faster ([VM3.2](sec_ai_vm3#vm32)). Acceptable under the coprocessor model, where the physical CPU stays and keeps the kernel — and it supersedes the P65816 premise of [B.4](sec_ai_b#b4) (→ [Q13](sec_ai_q#q13), [Q14](sec_ai_q#q14)).
- D89 — **`WDM` becomes the CPU-side mode gate and CPU probe, and [M.3](sec_ai_m#m3) is bounded rather than reversed.** [M.3](sec_ai_m#m3) rejected having **Helium snoop `WDM` on the bus** to carry kernel commands, on four counts: a snooper needs a new state machine tracking `VPA`/`VDA` where memory mapping widens a comparator that already exists; it would need its own privilege gate where `$FF` is already unmappable; it is not testable before a kernel exists; and it would oblige a softcore to replicate a private decode table. **None of the four applies to this use, because nothing on the bus decodes anything** — the CPU itself implements the opcode, and on a physical W65C816S `WDM` stays exactly what WDC reserved it to be, a two-byte no-op ([VM2.21](sec_ai_vm2#vm221), [NV1.12](sec_ai_nv1#nv112)). The memory-mapped command block of [M.4](sec_ai_m#m4) is unaffected and remains the kernel–hardware interface.
  NOTE: **Two consequences follow immediately.** The emulator must model `WDM` as a two-byte no-op in noVa64 mode or the CPU probe reports an Argon 2 that does not exist ([VM2.24](sec_ai_vm2#vm224)), which also settles the conflict [EM7.26](sec_ai_em7#em726) has been carrying. And [M.3](sec_ai_m#m3)'s closing sentence — that a softcore must implement `WDM` as a no-op decoding nothing — **holds for a 65816-compatible core and is precisely what Argon 2 overrides by not being one in that mode**.
- D90 — **Kernel services are reached through a numbered service table, not through `COP` signatures scattered across the code.** The VM must never call native code directly, because a callable address is fatal on an executor with no 65816 in it; native extension is therefore offered as **data** — small integers resolved by the host — and never as code ([VM1.40](sec_ai_vm1#vm140)). **The table is better hygiene for the kernel regardless of whether the VM is ever built**, which is why it is settled now and not with the VM ([M.1](sec_ai_m#m1), [J.3](sec_ai_j#j3)).
- D91 — **Banks `$00`–`$01` are reserved in the process memory map from the first loader, plus one shared read-only page for the system information block. This closes [Q5](sec_ai_q#q5).** The reserved region holds the 65816 direct pages and stack, the interpreter, its dispatch table and the VM state window; the shared page is the last 2 KB of bank `$00`, written by the BIOS before paging is enabled and mapped identically into every process ([VM1.17](sec_ai_vm1#vm117), [VM2.29](sec_ai_vm2#vm229)). **Reclaiming that region later is a migration, not an edit**, which is the whole reason it is decided before the loader is written ([N.6](sec_ai_n#n6), [L.11](sec_ai_l#l11)).
- D92 — **Four requirements bind noVa64 software from now, so that the kernel stays binary-compatible with noVa128.** No cycle counting to measure time, the fixed frequency reference being the only clock · no self-modifying code in project code · memory-mapped registers idempotent on read · and a software-visible register map that does not change, versioned through the system information block if it ever must ([NV1.10](sec_ai_nv1#nv110)). **Each is cheap today and silently breaks compatibility if violated** — the worst shape a requirement can have, because it fails on a machine that does not exist yet. The first is already implied by the PHI2 stall ([L.15](sec_ai_l#l15)); stating it makes it binding.
- D93 — **NVM32 division follows the RISC-V conventions and diverges from eBPF deliberately**: divide by zero yields `$FFFFFFFF` and leaves the remainder as the dividend, and `INT_MIN / −1` yields `INT_MIN` with a zero remainder, with no trap in either case ([VM1.32](sec_ai_vm1#vm132)). Chosen because it is what an iterative divider FSM and a C reference implement most naturally — the same reason twice. **It is recorded as a decision rather than as a detail so that nobody "fixes" it later** against the eBPF convention of zeroing the destination.
- D94 — **The NVM32 ISA freezes at toolchain gate T4, on measured evidence, and not before a backend exists.** An earlier draft said "ratify the ISA now"; writing even a skeleton vbcc backend then exposed six decisions that cost instructions in ordinary C, and **freezing first is exactly how those six would have become permanent** ([VM4.25](sec_ai_vm4#vm425)). The four encoding candidates are decided by the T3 opcode histogram against thresholds written in advance ([VM4.45](sec_ai_vm4#vm445)).
- D95 — **noVa128 retracts the iCE40 as the final target for the CPU FPGA.** Three modes means two CPUs on one die — a hardware 65816 with decimal mode, every addressing mode and `ABORTB`, plus the NVM32 FSM — at an estimated 6,000–8,000 LUT4 against HX8K's 7,680 logic cells, **leaving nothing for the cache that decides the performance** ([NV1.22](sec_ai_nv1#nv122)). [D01](sec_ai_q#d01)'s hand-solderability argument still holds for **Helium 2 and Neon 2, which may stay on iCE40; Argon 2 cannot.** This is the decision that sheet asks to approve, rather than the clock speed (→ [Q171](sec_ai_q#q171)).
- D96 — **vbcc is selected as the NVM32 cross compiler, which does not contradict [O.2](sec_ai_o#o2) ruling it out for the 65816.** There it was ruled out for having no 16-bit code generation at all; here it is retargeted to a machine designed after it, and its cross-module inlining, global common-subexpression elimination and inter-procedural register allocation each remove VM instructions worth 60–120 cycles apiece ([VM4.33](sec_ai_vm4#vm433)). **Calypsi remains the kernel compiler and the two toolchains never share objects** ([VM1.6](sec_ai_vm1#vm16)). Fallback ranking if vbcc fails: LLVM if redistribution matters, lcc if it does not (→ [Q165](sec_ai_q#q165)).

- D97 — **The host filesystem track becomes a filesystem sheet, and its gates are the first series named under [A3.11](sc_a3#a311).** It was written up beside the laptop stages because it needs no hardware, which is a scheduling property rather than a subject: roughly half of its source note is on-disk specification, a layer split and a vtable, and none of that belongs next to a keyboard matrix. **`F0–F9` becomes `FUS-00–FUS-09`** — three letters exist precisely so that a step is never read as an item, and `F5` against [F.5](sec_ai_f#f5) is the collision the scheme was written to prevent ([sheet Y4](sec_ai_y4)).
- D98 — **FAT32 is implemented on the host and never on the machine, and the cost of that is stated rather than absorbed.** Twenty-eight of the track's steps produce no code that lands on the target, because [D54](sec_ai_q#d54) chose ext2 as the transfer medium and nothing since revisits it. **What they buy is the synthesis problem**: a format with no inodes, no ownership and no mode bits forces an explicit account of what an attribute structure means to a caller, before ext2 hands one over for free ([Y4.15](sec_ai_y4#y415), [Y4.16](sec_ai_y4#y416)).
- D99 — **The host track is evidence and [sheet Y1](sec_ai_y1) is authority: where the two tables disagree, the machine's wins.** The track exists to discover the interface's real shape, which is not the same as owning it — a slot that is free on a PC with a heap may be unpayable against [Y1.12](sec_ai_y1#y112)'s 512-byte kernel stack. **Every divergence is carried as a question against [Y1](sec_ai_y1) rather than settled quietly on either sheet** ([Y4.5](sec_ai_y4#y45)).
- D100 — **The NVFS gates are written against draft 3, and the corpora are regenerated before [FUS-05](sec_ai_y4#fus-05) starts.** The source note pins its binding to the previous draft, its library and its generated corpora; [Y2.1](sec_ai_y2#y21) broke the format in both directions and says plainly that the harnesses survive and their corpora do not. **A binding to a format the machine will never mount buys nothing**, and writing it twice costs more than waiting ([Y4.19](sec_ai_y4#y419), → [Q175](sec_ai_q#q175)).
- D101 — **Gateware is written in Verilog-2005, and the toolchain decides it rather than the softcore.** Yosys and nextpnr read Verilog natively where VHDL needs GHDL and its Yosys plugin, and Verilator — the fast simulator and the linter — takes nothing else ([EM1.11](sec_ai_em1#em111)). The argument that kept [Q2](sec_ai_q#q2) open has lost its weight: since [D88](sec_ai_q#d88) Argon is not a 65816 softcore, and should a VHDL core such as P65816 ever be wanted ([Q16](sec_ai_q#q16)), it enters as one black box through GHDL rather than setting the language of the whole project. **Verilog-2005 and not SystemVerilog, because the Phase 0 rig synthesises under XST, which does not accept it** ([P1.1](sec_ai_p1#p11)); one dialect then serves ISE, Yosys and Verilator alike. Accepted cost: weak typing lets through what VHDL rejects at compile time — width mismatches, and nets declared implicitly by a typo. The compensation is discipline rather than language: the `default_nettype none` directive in every file, and `verilator --lint-only` with warnings as errors in CI ([E0.10](sec_ai_p3#e010)).

- D102 — **The kernel moves from bank `$01` to the top of the map: its fixed base is `$FD`, directly under Neon's `$FE` window and Helium's `$FF`, and it grows downward to a floor at `$F0`.** Three things recommend it. **Bank `$01` had two tenants and now has one**: [J.1](sec_ai_j#j1) put the kernel there, while [D91](sec_ai_q#d91), [VM1.17](sec_ai_vm1#vm117) and [VM2.7](sec_ai_vm2#vm27) put the VM interpreter there. **A kernel held to one 64 KB bank was the limit [Q99](sec_ai_q#q99) kept running into**, and at the top it grows without moving anything a process links against — user code still starts at `$02:0000`. And every privileged bank but `$00` now sits in one run at the top of the map. **What has a fixed address stays in `$FD`** — the numbered service table of [D90](sec_ai_q#d90) and the entry points the bank `$00` trampolines `JSL` to — so growth takes `$FC`, `$FB` and downward without moving any of it. **The floor is reserved now and left unmapped until used**: the user ceiling is `$EF:FFFF` whatever the kernel's actual size, which is the boundary [VM1.17](sec_ai_vm1#vm117) already had for guest data; its guest stack, which sat on `$F0`–`$FF`, comes down below it. Nothing in the hardware changes — the vectors, trampolines and kernel stack stay in `$00` because the CPU forces PBR=0 on entry, privilege stays per page, and a `JSL` costs the same to either bank. **Where the kernel sits in the virtual map says nothing about where its frames are**: only the entry, fault and MMU paths need the pinned SRAM region, and a kernel grown past 64 KB can keep the rest in SDRAM behind the cache rather than take room from the page tables ([Q9](sec_ai_q#q9)) (→ [L.10](sec_ai_l#l10), [J.1](sec_ai_j#j1)).
- D103 — **The shell calls only the libc surface, so the console is one source built twice.** The monolithic build links that surface to the kernel's `sys_*` functions and the user-mode build to the `COP` stubs of [O.7](sec_ai_o#o7), so the two differ in one library, one entry point and one source file, `sh_exec.c`. **Abandoned if keeping it needs `#ifdef` in the shared files beyond those three**; the shell then forks at [CON-04](sec_ai_cn1#con-04) and the monolithic copy is frozen (→ [CN1.1](sec_ai_cn1#cn11), [CN1.18](sec_ai_cn1#cn118)).
- D104 — **Line editing — echo, erase, kill line, Enter — lives in the kernel's tty, not in the shell.** Every program then receives complete lines for nothing, and the shell stays a parser (→ [CN1.12](sec_ai_cn1#cn112)).
- D105 — **The tty driver interprets control characters, and Neon stays a cell engine with a cursor and a scroll.** Tab stops, erase behaviour and a future ANSI subset are software policy, and in gateware every change to them would cost a bitstream. Revisited only if a measurement shows the driver's per-character cost dominating the console, and even then only the `\n` fast path moves into Neon (→ [CN1.10](sec_ai_cn1#cn110), [CN1.27](sec_ai_cn1#cn127)).
- D106 — **The EC sends raw key events and generates typematic repeat, and the keymap is the kernel's.** The GUI will need raw events on the same endpoint, USB HID keyboards do not repeat on their own, and the EC already owns the HID stack and a timer (→ [CN1.11](sec_ai_cn1#cn111), [V.30](sec_ai_v#v30)).
- D107 — **The kernel image lives in a boot partition of its own, in the executable format user programs use, and the BIOS reads no filesystem.** The BIOS needs a block read, an MBR parse and the kernel's own loader compiled a second time. **This supersedes the BIOS mounting NVFS to load `KERNEL.BIN`** ([I.4](sec_ai_i#i4), [G.3](sec_ai_g#g3)): an NVFS reader in the BIOS would have to follow every format change of [sheet Y2](sec_ai_y2), and a kernel kept in EC flash would tie kernel iteration to the EC update path. Moves to an NVFS file if NVFS gains a boot area of its own, or if a separate partition proves awkward to update from a host (→ [CN1.5](sec_ai_cn1#cn15), [Q177](sec_ai_q#q177)).
- D108 — **`open` resolves `/dev/<name>` against the device table before the VFS, and `/dev/tty` is the console.** It is the smallest mechanism that serves the console; a devfs mount replaces it when something needs to list devices. The serial line becomes `/dev/ttyS0`. **This closes [Q47](sec_ai_q#q47) the other way round** from the names [sheet H](sec_ai_h) had taken, and agrees with [P5.i](sec_ai_p2#p5i) (→ [CN1.15](sec_ai_cn1#cn115), [Q95](sec_ai_q#q95)).
- D109 — **The console runs in a degraded mode when there is no root filesystem**, which separates "the console works" from "the card and NVFS work" during bring-up (→ [CN1.7](sec_ai_cn1#cn17)).
- D110 — **Read-only before read-write: the root is mounted read-only up to [CON-02](sec_ai_cn1#con-02).** The first writes to the card come only after the reads are proven, as ext2's gates order it ([E2.0](sec_ai_y3#e20), [E2.1](sec_ai_y3#e21)) (→ [CN1.16](sec_ai_cn1#cn116)).
- D111 — **Drivers implement [J.4](sec_ai_j#j4)'s five functions from the monolithic build onward, even where `irq` is unused**, so that [P5.i](sec_ai_p2#p5i)'s driver framework becomes integration rather than a rewrite (→ [CN1.26](sec_ai_cn1#cn126)).
- D127 — **The source-level debugger is a host-side Debug Adapter Protocol server that reaches the machine only through the Debug Agent's command set, plus host-only extensions marked as such.** Written once, it serves the emulator now and the board later; the extensions — exact registers, any number of breakpoints, the shadow stack — are refused by the hardware backend rather than imitated. The prior art wrapped its adapter around its emulator and so could never reach its own board (→ [EM8.3](sec_ai_em8#em83), [EM3.3](sec_ai_em3#em33)).
- D128 — **Every ca65 image is built once, with debug information — `ca65 -g`, `ld65 --dbgfile` — and there is no separate debug target.** Neither flag changes a byte of the image, so a second target buys only a binary able to drift from the first; the adapter checks the `.dbg` against the image and the sources instead ([EM8.7](sec_ai_em8#em87)) (→ [EM8.8](sec_ai_em8#em88), [O.10](sec_ai_o#o10)).
- D129 — **Register width in ca65 sources is stated three ways: smart mode on, width macros that emit `REP` or `SEP` together with the matching directive, and an entry-width directive on every routine.** Smart mode follows straight-line code and not a branch or a call, which is why each routine writes down the width it expects as its contract (→ [O.10](sec_ai_o#o10), [EM4.16](sec_ai_em4#em416)).
- D130 — **No vector is ever zero.** Every native and emulation vector points at a handler, and one with nothing to do halts with its own name on the screen, as an unimplemented opcode does in the emulator ([EM4.4](sec_ai_em4#em44)). A zero vector sends a stray `COP`, `BRK`, `ABORT` or `NMI` to `$00:0000` to execute whatever is there, which is what the prior art's vector table did (→ [O.10](sec_ai_o#o10)).

## Open questions

- Q1 — [[!blocking]] ER-TFT101-1 module datasheet: backlight current/voltage, strap exposure on the FPC, GT911 connector, whether a panel reset or standby line is brought out to the FPC at all — **and whether the module needs any supply beyond 3V3 and the backlight string**. Most HX8282 designs generate AVDD, VGH and VGL on the module itself, and [sheet C](sec_ai_c) assumes this one does: the panel appears in its tree as a single 200 mA tenant of 3V3_MAIN. If it does not, the power tree gains rails and that row is wrong ([C.17](sec_ai_c#c17)). Order the panel in the **capacitive variant**. Blocks the KiCad schematic for sheets 1.5/1.6.
- Q2 — HDL choice (Verilog vs VHDL) — constrains the reference softcore (P65816 is VHDL).
  NOTE: **Closed by [D101](sec_ai_q#d101): Verilog-2005.** The softcore no longer decides it — [D88](sec_ai_q#d88) took the 65816 softcore off Argon, and a VHDL core can still enter through GHDL.
  NOTE: **[D88](sec_ai_q#d88) removes the constraint rather than answering the question.** The core Argon is now specified to carry is bytecode-native and written for this project ([sheet VM3](sec_ai_vm3)), so P65816's VHDL no longer decides anything. The choice reverts to Helium and Neon's own gateware, where it always mattered more.
- Q3 — Specific SDRAM controller among the three open-source candidates (adaptation and verification in E3).
- Q4 — EC↔kernel protocol — **closed for power**: shutdown, reboot and battery now have a specified transport, register set and failure behaviour ([sheet S](sec_ai_s)). What remains under this heading is the **HID event path** and the RTC, neither of which travels the power path. Two things are owed, not one: the event *format* ([V.30](sec_ai_v#v30) requires it fit 32 bytes and coalesce), and the *transport*, which [sheet H](sec_ai_h) still records only as "the EC channel". The proposal on record is the EC as I2C master with Helium as a slave plus a dedicated `IRQ_HID` line — three pins already carried in Helium's budget — but it predates the REV C bus split, and Helium sits in the switched domain while [C.8](sec_ai_c#c8) reserves the always-on bus to the charger, the gauge and the button. So it survives on **I2C-SW** or not at all, and that is a decision rather than an inheritance (→ [Q35](sec_ai_q#q35), [Q41](sec_ai_q#q41)).
  NOTE: **[D49](sec_ai_q#d49) constrains this proposal without settling it.** Helium becoming a master on a bus of its own is precisely so that it never has to become a master on I2C-SW — which leaves the HID proposal's *EC master, Helium slave* arrangement intact, on the bus it was written for. What must not happen is the two being conflated later: `I2C-EXP` is Helium-as-master and I2C-SW is Helium-as-slave, and a single I2C block inside Helium serving both roles on two buses is a gateware decision nobody has taken (→ [X.22](sec_ai_x#x22)).
  NOTE: **The console states the CPU-side half of the HID path** ([CN1.28](sec_ai_cn1#cn128)): raw events, one per key, carrying device, usage, modifiers, press or release and a repeat flag, with typematic repeat generated by the EC ([D106](sec_ai_q#d106)). The entry format and the interrupt line are [Q180](sec_ai_q#q180).
- Q5 — Exact format of the BIOS → kernel info block.
  NOTE: **Closed by [D91](sec_ai_q#d91) and [VM2.28](sec_ai_vm2#vm228).** The block is the last 2 KB page of bank `$00`, shared read-only and mapped identically into every process, written by the BIOS before paging is enabled, carrying a format version, the CPU identity, Helium's capabilities, coprocessor presence and the resolved VM gate. **BIOS implementations may differ between machines; the block's format may not** ([NV1.11](sec_ai_nv1#nv111)). What remains is the field-level encoding, which is [Q168](sec_ai_q#q168).
- Q6 — **Closed — the RP2354B.** Backlight `EN` and PWM stay with the EC, which is the only party awake both before Neon is configured and while the switched domain is coming down, and which already holds every rail enable through its expander. Neon recovers two pins its own budget needs and `BACKLIGHT_EN` leaves the register map (→ [D33](sec_ai_q#d33), [T1.52](sec_ai_t1#t152)).
- Q7 — **Closed, and in D04's favour.** There is no data link. Three *control* lines survive between the FPGAs and no more — `NEON_BUS_SEL` inbound, `NEON_BUS_BSY` outbound, and Neon's aggregated interrupt into Helium's PIC — and the 8 or 16 pins the old budget reserved for a link were reserved for something that does not exist. **They belong to the CPU bus tap Neon needs in order to see the `$FE` aperture at all**, which the same budget never counted; the substitution is recounted in [Q12](sec_ai_q#q12) and it costs 10 pins net (→ [B.6](sec_ai_b#b6), [T1.51](sec_ai_t1#t151)).
- Q8 — [[!blocking]] The 17 free pins on Helium do not cover SPI-SD, the UART console and the debug port. Allocated today: inter-FPGA link 8, I2C 2, RP2354B handshake 3, spare 4. Sheets D and F both depend on interfaces that have no pins — the budget does not close as written.
  NOTE: **[Sheet X](sec_ai_x) is the first thing to arrive at this question with an answer rather than a demand.** The expansion slot is priced at three pins and the slow bus at zero — its two are the "I2C 2" already in the allocation above, which the [C.13](sec_ai_c#c13) bus split left without a device — and both are deliberately sized to be refusable: dropping the second slot is one pin, dropping the slot entirely is three, and neither costs a milestone (→ [Q81](sec_ai_q#q81), [X.3](sec_ai_x#x3)).
  NOTE: [Sheet R](sec_ai_r) sharpens the deficit rather than easing it, **though by one pin less than it used to**: the debug agent needs `DEBUG_ENABLE`, `BE` out of Helium and optionally `DBG_IRQN`, and it turns the CPU-side address and data pins bidirectional (→ [Q27](sec_ai_q#q27)). **`DBG_CSN` is withdrawn** — the agent shares `LINK_CSN` as well as `SCK`/`MOSI`/`MISO`, and that is now the whole of the economy available on this boundary ([D80](sec_ai_q#d80), [R.23](sec_ai_r#r23)).
- Q9 — How many page tables actually stay resident? The 256 KB fixed region must hold the kernel (64 KB — or, once it outgrows that, only its entry, fault and MMU paths, [D102](sec_ai_q#d102)), the vectors, bank `$00` and the active tables at 32 KB each. K.2 used to promise 16 residents out of 512 KB; the honest figure now looks closer to four.
- Q10 — SRAM footprint compatibility: confirm in the datasheets that A20 on the 2 MB `AS7C316096` lands on an NC pin of the 1 MB `AS7C38096A` in TSOP-II 44. Usual for Alliance, unverified.
- Q11 — SDRAM column count: confirm the 512 Mbit part uses 10 column bits against the 256 Mbit part's 9, with the pinout otherwise identical — the premise the fallback footprint rests on.
- Q12 — **Recounted, and it closes at 100 of ~107** — but only after two errors in the old estimate cancelled each other, which is the part worth knowing. The old figure reserved **16 pins for an inter-FPGA link [D04](sec_ai_q#d04) had already deleted**, and never counted the **26-pin CPU bus tap** that replaced it; the substitution costs 10 and the budget was wrong in the dangerous direction. Against that, VGA costs 2 dedicated pins rather than 14 (the R-2R ladders hang off the panel's own RGB bus), the backlight's 2 went to the EC ([Q6](sec_ai_q#q6)), and the bank byte is captured off D0–D7 during PHI2 low instead of eight dedicated lines. Full table in [T1.51](sec_ai_t1#t151). **18 bpp remains the recommendation and 24 bpp still does not fit.** What is left under this heading is narrower and is what still blocks sheet 1.5: sign-off against the real TQ144 pinout, I/O bank by I/O bank, with the SDRAM's 39 pins kept in banks that can meet 103 MHz and the panel's 22 kept together — and with the GBIN-capable pins read off Lattice's own TQ144 pinout rather than assumed, since the oscillator has to land on one in all three devices ([B.7](sec_ai_b#b7)).
- Q13 — **Is the softcore even the right lever?** Given that memory and not the core is what caps this machine (→ [E.10](sec_ai_e#e10)), effort may be better spent on the cache and memory subsystem than on Argon. Worth deciding explicitly before anything is invested in FPGA-C.
  NOTE: **[D88](sec_ai_q#d88) sharpens this question rather than answering it, and gives it a number.** A bytecode-native core escapes [E.10](sec_ai_e#e10)'s ceiling by doing four to six times the work per instruction instead of the same work faster, which a 65816 softcore cannot. **The threshold that decides it is now written down: a measured ≥20× speedup over the interpreter on graphics-mode workloads, below which the core does not earn its FPGA** ([VM3.25](sec_ai_vm3#vm325)).
- Q14 — Argon's role and memory path — two halves of one question. Does the softcore *replace* the physical W65C816S on the shared bus or *coexist* with it? And if populated, does it use the standard bus into Helium, with the same PHI2 and cache constraints as the physical chip, or a dedicated wider link into Helium's cache? Without the latter its advantage is marginal.
  NOTE: Related to [Q7](sec_ai_q#q7): both ask what private FPGA-to-FPGA paths this board actually has.
  NOTE: **The first half is answered and the second is not.** Under [D88](sec_ai_q#d88) the core *coexists* with the physical W65C816S rather than replacing it — it is a bus-mastering coprocessor and the 65816 keeps the kernel ([VM3.10](sec_ai_vm3#vm310)). **The memory path is still open and is still the half that decides whether it is worth building**: the core rides Helium's arbitration and shares the MMU, TLB and page tables, so bandwidth rather than Fmax binds it ([VM3.12](sec_ai_vm3#vm312)), and the arbitration policy between the two masters is unspecified ([VM3.28](sec_ai_vm3#vm328)).
- Q15 — The real iCE40 Fmax of a candidate core: synthesize P65816 stripped of its SNES bus-timing fidelity on the target part and read the placed-and-routed figure. Every speed estimate in [sheet E](sec_ai_e) is guesswork until this number exists.
- Q16 — Base core: P65816 cleaned up and given a flat memory interface, for maximum compatibility, versus FT816 for speed first — pending an instruction-coverage audit of FT816. Tied to [Q2](sec_ai_q#q2), since P65816 is VHDL.
  NOTE: **Overtaken on both branches.** For noVa64, [D88](sec_ai_q#d88) makes Argon bytecode-native, so neither candidate is the core it would carry. For noVa128, Argon 2 is a tri-mode core written for the project against an instruction-compatible — **not cycle-compatible** — contract ([NV1.5](sec_ai_nv1#nv15)), which is a weaker requirement than either candidate was built to meet and is the reason it can be written at all. **The question survives only if a faithful 65816 softcore is wanted for its own sake**, which [E.10](sec_ai_e#e10) already doubts.
- Q17 — Freeze the canonical user virtual map *within* `$02–$EF`: where `.text` ends and `.data` begins, stack size, heap start.
  NOTE: **[VM1.17](sec_ai_vm1#vm117) is a concrete proposal for the same map and should be read alongside this**: `.text` at `$02_0000`, data and heap from `$10_0000`, a 1 MB stack growing down from `$FF_FFFF` with a guard page, and banks `$00`–`$01` reserved ([D91](sec_ai_q#d91)). It was derived for the VM's guest space, but **the VM's guest space is the process virtual space** ([VM1.21](sec_ai_vm1#vm121)) — so freezing the two independently would produce two layouts where the design needs one.
  NOTE: The bank boundaries themselves are settled and not part of this question — an early draft placing user `.text` at `$01:0000` was rejected against [L.10](sec_ai_l#l10).
  NOTE: **[D102](sec_ai_q#d102) lowers the ceiling to `$EF:FFFF`**, since `$F0`–`$FD` is now the kernel's reserve. In [VM1.17](sec_ai_vm1#vm117) it moved the stack from `$F0`–`$FF` to `$E0`–`$EF`, so guest data now ends at `$DF:FFFF`; `.text` and the start of `.data` are where they were.
- Q18 — Bank `$00` — **settled in principle**: each process's stack pages are pinned for its whole lifetime, and the vectors, trampolines and kernel stack occupy one or two privileged pages mapped identically in every process (→ [L.11](sec_ai_l#l11)). What is left is sizing: the exact split of those one or two pages between the three tenants, how large the kernel stack should be, and whether there is one shared kernel stack or one per process.
- Q19 — Audit Calypsi's calling convention and its direct-page pseudo-register usage. Two things fall out of it: the exact context-switch save set, and how syscall arguments are passed.
- Q20 — Specify the binary format header — field layout, magic value, versioning.
- Q21 — Shared read-only text: is libc's `.text` duplicated in every process, or mapped shared read-only across page tables? The PTE R/X bits already allow it and the memory win is free, but it puts page reference counting into the loader.
- Q22 — Bank `$FF` register map — **Helium's MMU block is specified** (→ [sheet M](sec_ai_m)), the **power block now exists too** (→ [sheet S](sec_ai_s)), and the **peripheral block has acquired its first tenant and its register set** — the storage block of [G.6](sec_ai_g#g6), specified as offsets precisely because this question is open. All three want a 256-byte wall of their own. Still unassigned: three base addresses, and the timer and interrupt controller entirely. Keep the walls between blocks so the decode and the privilege check stay trivial.
  NOTE: **And the count has grown again, in a direction that argues for settling the map rather than extending it piecemeal.** [Sheet X](sec_ai_x) asks for one wall per expansion slot — proposed at `$FF:7E00` and `$FF:7F00`, the top of Helium's half against Neon at the bottom of the other one — plus one for the slow bus's block. That is now **six blocks and a timer** in a bank whose allocation is a five-minute decision nobody has taken, and the two [sheet X](sec_ai_x) adds are the only ones that can be moved for free, since no gateware and no header depends on them yet (→ [Q82](sec_ai_q#q82)).
  NOTE: The debug agent claims no space here and must not be given any — its register file is SPI-only by decision [D18](sec_ai_q#d18) (→ [R.4](sec_ai_r#r4)).
  NOTE: **Neon is back on this list, and it is the reason to settle the rest of the map now.** Its registers occupy `$FF:8000`–`$FF:80FF` — the bank's first off-chip tenant, and **the one block Helium does not answer** ([D36](sec_ai_q#d36)). The base was chosen so that Helium's test is a single address bit rather than a range comparison: everything at or above `$FF:8000` belongs to Neon, everything below is Helium's to allocate as it likes. So the walls this question asks for now have a natural outer boundary, and the timer, the interrupt controller, the peripheral block and the power block ([Q40](sec_ai_q#q40)) can be placed in `$FF:0000`–`$FF:7FFF` in any order without ever colliding with Neon (→ [T1.22](sec_ai_t1#t122)).
- Q23 — What a panel larger than 10.1” would cost. RGB-TTL dies above ~10”, so a 14” class panel means a **transmitter bridge** — an ANX6345, taking the parallel RGB Neon already produces and running eDP link training itself in hardware, configured over I2C by the RP2354B before the CPU leaves reset.
  NOTE: On iCE40 that is effectively the only route: driving LVDS needs a 7:1 output serializer and native eDP needs hard SerDes, and neither exists on this family — so the two alternatives an ECP5 would have had are both closed here. Knock-on costs: ~22 pins on Neon at 18 bpp against a budget already near its limit (→ [Q12](sec_ai_q#q12)), a framebuffer and bandwidth budget to re-derive at the new resolution, a larger backlight boost than the PT4110 sizing in [C.6](sec_ai_c#c6), and touch to re-specify — laptop panels are usually non-touch, which puts the GT911 of [D07](sec_ai_q#d07) in question.
  NOTE: **Closed by [D70](sec_ai_q#d70), and closed by taking the route this entry ruled out.** A 14-inch class panel needs no bridge and no hard SerDes: it needs **an external LVDS serializer**, a mature TSSOP part with a second source, and [sheet U1](sec_ai_u1) is the answer to the question this entry asks. What it cost instead is a different set of constraints — an even/odd channel split, half-resolution rendering, and a pixel clock this document does not yet have ([Q137](sec_ai_q#q137), [Q141](sec_ai_q#q141)).
- Q24 — ASID width, still unfixed. It drives both EBR consumption per TLB entry and how often an ASID must be recycled — and every recycle carries a mandatory flush (→ [M.8](sec_ai_m#m8)). Four bits (16 contexts) and six (64) have both been floated; validate against the EBR budget alongside the 32–64 TLB entries already planned.
- Q25 — **Settled** — how the RP2354B reaches Helium's control registers with the 65816 held in reset. Neither option as posed: not bus mastering, and not the configuration path either, but a **dedicated chip select onto the shared configuration SPI data lines**, driving a debug agent that performs the access from inside Helium. An internal write to `$FF:00xx` meets the same comparator a CPU store would, so [sheet M](sec_ai_m)'s whole command model is exercisable with no CPU (→ [D18](sec_ai_q#d18), [R.21](sec_ai_r#r21)).
- Q26 — **Closed by the part, and not in the direction the question expected.** It asked whether the EC's flash should grow to 16 MB so that backup bitstreams and the BIOS could live in it and the machine could cold-boot with no card. The RP2354B's flash is **in the package at 2 MB and cannot grow**: an external part could be added beside it, but it would reintroduce the always-on component and the net that [D1.8](sec_ai_d1#d18) deleted, and it would need its own recovery story. **Reopened and answered the other way by [D60](sec_ai_q#d60), and the correction is arithmetic rather than judgement**: this entry declined the capability without ever checking whether it needed the extra flash to have it. Three HX8K bitstreams are ~135 KB each and `bios.bin` is small; **the whole configuration store fits in the 2 MB already in the package, twice over.** No external part, no always-on component, no new recovery story — the thing this entry was protecting against was never required. **A machine that boots with an empty slot is now a capability the design has** ([D1.21](sec_ai_d1#d121), [G.2](sec_ai_g#g2)).
- Q27 — [[!blocking]] Debug agent pins and the `BE` handoff, all of it ahead of schematic capture: route `BE` from Helium to the CPU socket; make Helium's CPU-side address and data pins `inout` and check the I/O bank and pin-count impact on the TQ144 sheet; place the `DEBUG_ENABLE` strap with its pull and jumper footprint; place the 3-pin UART header; and decide whether `DBG_IRQN` is worth a pin or the console polls, which the pending bitmap of [D3.11a](sec_ai_d3#d311a) makes cheaper to answer than it was (→ [R.23](sec_ai_r#r23), [Q8](sec_ai_q#q8)). **`DBG_CSN` has left this list** ([D80](sec_ai_q#d80)). The turnaround count between `BE` and Helium driving must be derived from the W65C816S datasheet at 3.3 V, not guessed.
- Q28 — The debug agent's **SPI-to-core clock domain crossing**: synchroniser depth and the command handshake, specified formally rather than left to whoever writes the module. It also sets the real ceiling on the 16 MHz link. This is where subtle intermittent failures live, and they would be attributed to the memory system rather than to the tool observing it.
- Q29 — **Arbiter priority order** now that the debug agent is a client: where it sits against the CPU port, the fill engine and the walker. SDRAM refresh stays highest; the rest is a decision, and `ERR_ARB` exists because the agent has to give up rather than wait forever (→ [R.17](sec_ai_r#r17)).
  NOTE: **[D45](sec_ai_q#d45) adds a fourth client and it is the easiest of them to place.** The SPI-SD DMA engine moves 512 bytes at a time and is fed by a link three orders of magnitude slower than the SDRAM, so it can sit at the bottom of the order and lose every contest without ever becoming the bottleneck — but it needs a bounded give-up like the debug agent's, and `SD_STATUS.ERR_ARB` exists for the same reason `ERR_ARB` does (→ [G.10](sec_ai_g#g10)).
  NOTE: **Neon's arbiter is now a second instance of this question, and there the answer is a hard bound rather than a preference.** A CPU read of the `$FE` aperture stops PHI2 until Neon answers ([D37](sec_ai_q#d37)), so whatever the blitter is doing when the read arrives is added directly to interrupt latency — up to 1.5 ms if a full-screen keyed copy has to finish first. **The CPU read port needs high priority and the blitter must be preemptible at a bounded burst boundary**, and the resulting worst case has to be stated in microseconds, not left implicit (→ [Q57](sec_ai_q#q57)).
- Q30 — **Trace buffer depth** against the EBR left after the TLB and the cache tags. 1024 records at ~48 bits is the proposal, roughly six blocks on the HX8K; it competes directly with the 32–64 TLB entries of [L.7](sec_ai_l#l7) and with whatever [Q24](sec_ai_q#q24) settles for the ASID width.
- Q31 — [[!blocking]] **The AON↔switched crossings audit**: a net-by-net list of every connection over the domain boundary, each checked against R1–R3 ([C.13](sec_ai_c#c13)). It deserves a review pass of its own rather than being folded into general ERC, because it is the item on the power sheet most likely to produce a board-level bug that is hard to diagnose — an AON pull-up back-feeding a dead rail has no symptom on a meter and a very confusing one on a scope. Blocks schematic sign-off.
- Q32 — **BQ25896 behaviour when the input steps 5 V → 9 V mid-operation.** The cold-start path depends on it: the EC boots on the default 5 V contract and the CH224K then renegotiates underneath a running system. The part is designed for this; the datasheet confirmation has not been done.
- Q33 — **Measure 3V3_MAIN and 1V2 at E1 and revise the budget** ([C.17](sec_ai_c#c17)). The SDRAM and VCCIO rows dominate the total and both scale with bus activity, so the TPS63020's ~45 % margin is only as good as two estimates. A measurement above the assumption forces a higher-current part, which is a BOM change, not a firmware one.
- Q34 — **TPS63900 availability and its actual Iq.** The AON rail is chosen on quiescent current alone, and the ~17 mW standby figure and the "the pack self-discharges before it flattens" claim both rest on it. The TPS63001 is the fallback, at a cost in standby drain that would have to be re-derived. Tied to the same BOM pass as CH224K versus its successor CH224A, the K being phased out.
- Q35 — **Where the PCF8563 RTC lives now that the I2C bus has split in two.** It wants to keep time while the machine is off, which argues the always-on bus; but that bus is otherwise reserved to the charger and gauge, and every device added to it costs standby current permanently. The alternative — RTC on the switched bus with its own backup cell — moves the cost to a battery and a footprint (→ [H](sec_ai_h)).
  NOTE: **[X.22](sec_ai_x#x22) adds a third option that did not exist when this was written, and it is the better version of the second one.** On `I2C-EXP` — Helium's own bus, switched domain, no EC in the middle — the PCF8563 keeps time from its backup cell whether or not anything is powered, because a crystal does not care who owns the bus; and the kernel reads the clock as a mirrored window instead of asking the EC for it. It costs the same cell and footprint as the switched-bus option and deletes a transport. It becomes window 0 of a tier that exists for exactly this kind of device.
- Q36 — **The three press durations against the BQ25896's own `QON` thresholds.** Short (< 1 s), long (~4 s) and the charger's hardware reset have to be separable by a user with one button. If the EC's 4 s collides with the charger's window, the EC's number moves — the charger's is fixed in silicon (→ [S.6](sec_ai_s#s6)).
- Q37 — **EC policy on a repeated `NAK`**, and the related question of whether a battery-critical request may be declined at all. A kernel that refuses twice is either busy or broken and the EC cannot tell which; escalating too eagerly loses data, escalating too late loses the machine. The battery case has a short argument on one side: the battery does not negotiate. Kernel and EC firmware must agree, and today neither is written (→ [S.15](sec_ai_s#s15)).
- Q38 — **Carving the always-accessible SPI region** — `EC_PWR_STATE`, `TELEM_CTRL` and the staging bank outside the `DEBUG_ENABLE` gate — without disturbing the debug agent's existing map ([R.18](sec_ai_r#r18)). Gateware work, and the addresses proposed in [sheet R](sec_ai_r) are proposals.
- Q39 — **The grace period and the EC watchdog are a matched pair and have no canonical home.** 3 s inside 10 s today, with ~4.4 s of margin. A grace period longer than the watchdog turns every shutdown into a forced one *silently*, since the two are indistinguishable from outside until someone loses data. Both numbers must live in one place, in a form both the kernel and the EC firmware build from (→ [S.15](sec_ai_s#s15)).
- Q40 — **Base address of the power and telemetry block within bank `$FF`** — the 16-byte telemetry window plus `POWER_CTRL` and `POWER_STATUS`, behind their own 256-byte wall (→ [Q22](sec_ai_q#q22)). Blocks the gateware decode and the kernel headers equally, and it is a five-minute decision that two independent pieces of work are waiting on.
- Q41 — **Closed — there is no expander.** The question was which domain the MCP23017 lives in, given that it must sit on the always-on side to drive an enable at all, which put it on a bus the power sheet reserves for the charger and gauge and put its outputs across the domain boundary under R1 and R2. **The RP2354B's 48 GPIO absorb everything the expander was carrying**, so the part, the bus contention and the crossing all disappear together ([D1.6](sec_ai_d1#d16), [D1.8](sec_ai_d1#d18)). The recount that replaces it is a different exercise: every GPIO assignment validated against the function-mux table (→ [Q105](sec_ai_q#q105)).
- Q42 — **Reboot: warm or cold?** The EC re-runs the power-up sequence after the rails drop, which is a cold restart by construction. Whether the kernel needs to distinguish the two — and whether anything should survive a reboot that does not survive a poweroff — is unanswered, and the answer decides whether `REQ_REBOOT` is one bit or the start of a state machine.
- Q43 — [[!blocking]] **Neon's PLL constants and the final modeline.** `DIVR=0 DIVF=32 DIVQ=3` gives 103.125 MHz core and 51.5625 MHz pixel from the 25 MHz oscillator, and 1344 × 640 puts the refresh at 59.95 Hz — but **those blanking values are a self-consistent set, not figures from a datasheet**, and the module datasheet is the same one [Q1](sec_ai_q#q1) is still waiting for. The pixel clock and the active geometry will not change; only the porches will, and with them the exact refresh. Blocks schematic sheet 1.5 and the timing generator equally (→ [T1.4](sec_ai_t1#t14), [E0.4](sec_ai_p3#e04)).
- Q44 — [[!blocking]] **Timing closure at 103.125 MHz on the HX8K**, with the SDRAM controller and the blitter placed together. Controllers in this range are documented on the family; that is not the same as a placed-and-routed design with everything else beside it. The fallback is single-rate at 51.5625 MHz, halving peak bandwidth to ~103 MB/s — every figure in [sheet T1](sec_ai_t1) halves and the architecture survives, but the margins do not. Synthesise a stripped controller early rather than discovering this at E5 (→ [T1.10](sec_ai_t1#t110)).
- Q45 — **Neon's EBR relief, and it must not be chosen before synthesis.** The 32 blocks are fully allocated with zero margin. Two reliefs exist: **reduce the font to 128 glyphs** — full ASCII plus box-drawing, freeing 4 blocks, and it should be a synthesis parameter from the first day — or **multiplex the 16 text-buffer blocks into graphics use**, freeing 8 KB at the cost of address muxes and of destroying screen contents across a mode switch. **The font blocks must not be reclaimed under any scheme**: their bitstream initialisation is the entire mechanism behind [D27](sec_ai_q#d27). Decide once the blitter's real EBR demand is known (→ [T1.12](sec_ai_t1#t112)).
  NOTE: **[Q182](sec_ai_q#q182) depends on this**: an ISO-8859-15 console needs all 256 glyphs, which the 128-glyph relief would remove.
- Q46 — **Closed by [D36](sec_ai_q#d36), and structurally rather than by a rule.** The question was how to keep Neon's register file out of a user framebuffer mapping, since a process reaching `LIST_BASE` and `CMD_CTRL.LIST_RUN` commands an engine that reads and writes all 64 MB with no MMU in front of it. The answer is that **the register file is no longer in the aperture**: it moved to `$FF:8000`, and bank `$FF` is unmappable to user space by construction ([L.10](sec_ai_l#l10)). The aperture is now data all the way through and the mapping ioctl has nothing left to remember. What survives is one negative test at E8 — a process that asks for a mapping of every page it can name must still not reach a Neon register — kept because an architectural guarantee deserves a test precisely when nobody expects it to fail (→ [T1.21](sec_ai_t1#t121), [J.5](sec_ai_j#j5)).
- Q47 — **The console's device name, and the one requirement that comes with it.** The Neon text console and the serial line cannot both be `/dev/tty`; this document now calls the screen `/dev/con` and leaves the UART as `/dev/tty`, which is a naming decision, not an architectural one, and it should be ratified before the driver table is numbered. The requirement is not cosmetic: **the console driver must hold its own scrollback in system memory and repaint from it**, because a graphics mode may reclaim the text buffer's block RAM ([Q45](sec_ai_q#q45)) and a mode switch and back can destroy the screen. Normal for a virtual console, expensive only if discovered late (→ [T1.55](sec_ai_t1#t155)).
  NOTE: **Closed by [D108](sec_ai_q#d108), in the other direction**: `/dev/tty` is the screen console, as [P5.i](sec_ai_p2#p5i) already had it, and the UART is `/dev/ttyS0`. **The scrollback requirement is untouched** and lives in the console's output backend ([CN1.9](sec_ai_cn1#cn19)).
- Q48 — **Ratify the coordinate-based command format and budget what it costs.** Three items travel together: the sequential multiplier in the command processor (~16 clocks, ~80 LUT); the clip unit **rejecting a fully off-screen rectangle before issuing any memory traffic**, on which the off-screen parking idiom for unused list entries entirely depends; and the processor **sign-extending coordinates and clipping negatives**, so an object can hang off the left or top edge. None is optional and all three are cheap; they are open only because nobody has written them down as requirements on the gateware (→ [T1.42](sec_ai_t1#t142), [T1.43](sec_ai_t1#t143)).
- Q49 — **Does `COPY_EXPAND` read its 1-bpp source at a bit-granular x offset, or must glyph atlas entries be byte-aligned?** The answer decides whether a proportional UI font can be packed tightly in the atlas or must be padded to 8-pixel boundaries, which costs VRAM and, more importantly, decides the width-table format the GUI is written against. Cheap to answer now, disruptive to change once fonts exist.
- Q50 — **Who owns Neon's 64 MB.** Framebuffers, glyph and icon atlases, pre-rendered level buffers, save-under pools and command lists all live there and nothing partitions them today; the addresses in the worked examples are placeholders. Two constraints belong to whatever allocator emerges: source and destination of a copy should sit in **different SDRAM banks** so the controller interleaves them instead of paying a row activation per alternation, and command lists must not be moved while `LIST_RUN` is set (→ [T1.14](sec_ai_t1#t114)).
- Q51 — **Command-list versioning between gateware and kernel.** The explicit word count in every command exists so an unknown opcode can be skipped rather than desynchronising the stream — a decision made precisely because the two will drift during development. What is missing is the other half: how a kernel discovers which opcodes the gateware it is talking to actually implements. `NEON_VER` is one byte and a table has to hang off it somewhere (→ [T1.43](sec_ai_t1#t143)).
- Q52 — **How far the service port reaches: SDRAM, or block RAM only.** Full reach costs an arbiter port shared with the CPU write FIFO and perhaps 100 LUT, and buys bulk asset loading straight from the card at ~2.5 MB/s against the CPU's ~1.3, at no cost to the 65816. Block RAM only is simpler and still gives the boot display and the debug channel, which are the two things no milestone can do without. The bulk-load benefit is real but nothing depends on it (→ [T1.46](sec_ai_t1#t146)).
- Q53 — **Verify Calypsi generates absolute-long addressing for `(volatile uint8_t *)0xFE0000`** without reloading a bank register on every access. Every line of C that touches Neon depends on it, and so does the honesty of the ~140 µs per-frame figure. It belongs with the calling-convention and direct-page audit already outstanding (→ [Q19](sec_ai_q#q19), [T1.62](sec_ai_t1#t162)).
- Q54 — **The VGA bring-up clock, and whether VGA survives at all.** 640×480 wants 25.175 MHz and the video domain gives 25.78 — 2.4 % fast, which most monitors tolerate and none is specified to. Neon's second PLL is free and could synthesise it exactly, but audio wants that PLL too — less badly than it looks, since grounding the DAC's `SCK` puts the master clock inside the PCM5102A (→ [T1.9](sec_ai_t1#t19)). The prior question is whether VGA is still worth its 2 pins and its gateware **now that Mode 0 puts a working console on the panel itself at [E1.7](sec_ai_p3#e17)**, three stages before VGA was ever going to be useful (→ [T1.9](sec_ai_t1#t19)).
  NOTE: **Audio's half of this question is now closed, and it closed harder than [T1.9](sec_ai_t1#t19) expected.** The iCE40 PLL is integer-only, and neither 44.1 nor 48 kHz is reachable from 25 MHz at any setting — 441 and 3,125 do not factor into `(DIVR+1) ≤ 16` times a power of two. **The second PLL cannot produce an exact audio clock**, so audio has no claim on it at all rather than a softer one, and this question reduces to whether VGA is worth two pins and its gateware ([W.11](sec_ai_w#w11), [Q77](sec_ai_q#q77)).
- Q55 — **Per-window VRAM buffers with compositing — deferred, not rejected.** Each window owning a buffer and the framebuffer being produced by compositing in z-order removes the damage problem entirely: occluded content still exists, so moving a window is a recomposite rather than a repaint from application state. With 64 MB and ~143 MB/s it is affordable — ~15 KB per window on top of the 75 KB framebuffer — which is not true of most machines this size. It is materially more gateware and more software, and **it must not be attempted before the flat framebuffer and its damage model are working** (→ [T1.57](sec_ai_t1#t157), [T1.58](sec_ai_t1#t158)).
- Q56 — **Closed. The three inter-FPGA nets are named, and the naming carries the philosophy**: `NEON_BUS_SEL` (Helium → Neon) selects Neon's bus, `NEON_BUS_BSY` (Neon → Helium) holds the CPU while that bus is busy, and `NEON_IRQ` aggregates Neon's three interrupt sources into Helium's PIC. `VRAM_SEL` and `BWAIT` are retired — the first described less than half of what it does now that Neon has two windows, the second described a mechanism that was going to stretch the wrong signal. Polarities and pulled states are settled with them, including the one deliberate departure from [B.8](sec_ai_b#b8): **`NEON_BUS_BSY` is busy by default**, because for that net the pulled state must be the safe one (→ [B.6](sec_ai_b#b6), [D37](sec_ai_q#d37)).
- Q57 — **The read-stall timeout, and the bound the arbiter has to guarantee** — one number and one policy, and neither has an owner. The watchdog window for a VRAM read must be long enough to survive a refresh plus a legitimate arbiter queue and short enough that a missing Neon is reported rather than merely felt; it now serves three clients rather than two — a fill, a Neon that never answers, and a card that asserts `/EXP_BSY` and dies ([X.12](sec_ai_x#x12)) — which is an argument for settling one number rather than three. It belongs in the same place as the fill watchdog's, not beside it ([F.11](sec_ai_f#f11)). The policy is [Q29](sec_ai_q#q29)'s: the CPU read port needs priority high enough, and the blitter preemption granularity fine enough, that the worst case is microseconds and not the 1.5 ms of a full-screen keyed copy. **Both are cheap to decide and expensive to discover** — the failure mode is scheduler jitter that appears only under drawing load (→ [D37](sec_ai_q#d37), [T1.19](sec_ai_t1#t119)).

- Q58 — [[!blocking]] **Which blitter: operations or channels?** [Sheet T1](sec_ai_t1) specifies an operation-based engine taking `(x, y)` commands from a FIFO or a display list; [sheet T3](sec_ai_t3) specifies the Amiga four-channel engine with 256 bitwise logic functions and raw pointer-plus-modulo addressing. They are different machines, not different register maps: the minterm LUT cannot express a colour-key compare and the operation set cannot express XOR. **The decisive figure is setup cost** — ~30 stores, ~19 µs of CPU per blit, which is nothing for a compositor doing a few large blits and fatal for the 24-sprite frame of [T1.59](sec_ai_t1#t159), where it is ~450 µs against the 140 µs budgeted for the whole frame. **The recommendation is [T3.4](sec_ai_t3#t34)'s third option**: this datapath with sheet T1's command layer generating the pointers, which is roughly LUT-neutral and keeps both. Decide before RTL; it reaches the kernel, the toolchain and both milestones (→ [T3.1](sec_ai_t3#t31)).
  NOTE: **A third argument arrives from software and it is about capability, not cost.** The toolkit needs **XOR** — selection highlight, pressed states, the text caret, the focus rectangle, any rubber-band outline — and sheet T1's operation set has no raster op at all. Without one, every one of those becomes a fill plus a keyed copy from an inverted duplicate: twice the traffic, twice the commands, and a visual language rewritten around it ([V.14](sec_ai_v#v14)).
- Q59 — **Does the GUI run at 1 bpp or 8 bpp, and does Mode 1 survive?** [T1.30](sec_ai_t1#t130) calls the 1-bpp barrel shifter "not optional" for a GUI; [T3.10](sec_ai_t3#t310) observes that at 8 bpp on a 16-bit bus the shifter degenerates to a byte swap, **deleting ~400 LUT and buying 256 colours instead of two**. The costs are a 614,400 B framebuffer against 76,800 and 36.8 MB/s of scanout against 4.6 — both comfortable against 64 MB and ~150 MB/s. A **1024 × 600 × 8 bpp mode does not exist in sheet T1** and every figure in sheet T3 assumes it. Whether it replaces Mode 1 or joins it decides what the window server is written against (→ [T3.12](sec_ai_t3#t312)).
  NOTE: **A third sheet has since joined the 8-bpp side, and it does more than assume.** [Sheet U1](sec_ai_u1) computes its geometry, its 1024-byte stride and its entire bandwidth argument at 8 bpp indexed, and the panels it is written against have no 1024 × 600 in them at all ([U1.29](sec_ai_u1#u129)). **That does not close this question, it sharpens it**: the depth is now assumed by three sheets and specified by one, and the resolution under it has become a second open item (→ [Q145](sec_ai_q#q145)).
  NOTE: **It also decides every icon, and that is the expensive half.** [Sheet V](sec_ai_v) is written for 1 bpp throughout — gray as dither, selection as invert, depth as a 1px frame and a shadow line — and redrawing that visual language for 256 colours is weeks of art rather than an afternoon of code. **Answer this before drawing a single icon**, which is the toolkit's own open item folded in here rather than asked twice ([V.13](sec_ai_v#v13)). And 2 bpp, floated as a middle path, is the worst of the three on this device: the shifter argument is not linear, so 2 bpp pays most of 1 bpp's ~400 LUT and buys four colours instead of 256.
- Q60 — **Flat framebuffer with repaint, or backing stores with recomposition?** [T1.55](sec_ai_t1#t155) recommends the flat model and defers backing stores ([Q55](sec_ai_q#q55)); [T3.31](sec_ai_t3#t331) recommends backing stores with damage-limited recomposition and shows the budget carries ~90 full-screen composites a second, so full recomposition is always available as a correct fallback. **The disagreement is downstream of [Q59](sec_ai_q#q59)** — T argued against a 1-bpp screen where repaint is cheap, U against 8-bpp stores with 64 MB behind them. The consequences are opposite and neither is retrofittable: under one, occluded pixels are gone and the window manager repaints from application state; under the other they are preserved and a move is a recomposite. **Answer Q59 first.**
  NOTE: **[Sheet V](sec_ai_v) is the software half of this question and it argues the same way U did**, from a different direction: with backing stores the OS gets *smaller* — `layers.library` and its cliprect arithmetic disappear, clients never receive refresh events, a hung client still displays, and the event set drops to ten. It also sharpens the cost. At 1 bpp a full recomposite is ~1.0 ms and the screen can be rebuilt fifteen times a frame; **at 8 bpp it is ~8 ms and a typical desktop at 1.8× overdraw consumes essentially the whole frame**, so damage-limited recomposition stops being an optimisation held in reserve and becomes the routine path from the first day (→ [V.11](sec_ai_v#v11)).
- Q61 — [[!blocking]] **Block RAM no longer closes.** Sheet T1 is at 32 of 32 with zero margin ([T1.12](sec_ai_t1#t112)); sheet T3's tally adds **2 blocks for audio that T never counted** and **2 for the 8-deep snapshot queue against T's 1** for the command FIFO, so the combined design wants 34–35 before the blitter's burst buffers. The reliefs are known — a 128-glyph font frees 4 ([Q45](sec_ai_q#q45)), and a 2-bpp cursor rather than 4-bpp gives back half a block ([T3.29](sec_ai_t3#t329)) — but **what was insurance is now spent**, and it has to be decided before RTL rather than after synthesis (→ [T3.38](sec_ai_t3#t338)).
  NOTE: **Two more claimants have arrived on the same relief and it no longer stretches.** [T2.6](sec_ai_t2#t26) needs a third block for the second palette bank, and [U1.13](sec_ai_u1#u113)'s full double line buffer at Full HD is larger than the 1 KB [T1.11](sec_ai_t1#t111) budgeted. **The font and the cursor between them free four and a half blocks against a shortfall that is now larger than that** ([Q133](sec_ai_q#q133)).
  NOTE: A third claimant now exists and it is not vapour: `DRAW_GLYPHS` ([Q64](sec_ai_q#q64)) wants a source buffer and is the single largest CPU saving available to the GUI. **It is blocked on this question, not on its own merit.**

- Q62 — [[!blocking]] **Where the window server lives, and it is decided by [D36](sec_ai_q#d36) rather than by preference.** The first pass at [sheet V](sec_ai_v) made `wserver` a user task owning the `$FE` aperture and called that the protection model. Half of it works — [J.5](sec_ai_j#j5)'s ioctl maps the aperture, and pixels, atlases, palette and command lists are all reachable that way. The other half does not: `CMD_PORT`, `LIST_BASE`, `CMD_CTRL.LIST_RUN`, `DISPLAY_BASE`, `VRAM_PAGE` and the cursor position are in bank `$FF`, **which is unmappable to user space by construction**, so **command emission is a privileged act on this machine**. The recommendation is the split the glossary already draws: **the compositor is kernel code** — vblank handler, z-ordered surface list, top-level command list, swap — **and the window server is a user task** doing hit-testing, focus, drag, menus, decoration and client validation, reaching the hardware through a `/dev/neon` node and an `ioctl`, which adds no syscalls and keeps [D23](sec_ai_q#d23) intact. **The prize for getting it this way round is real**: a compromised window server can corrupt what is on screen and nothing else, because it cannot aim a command processor that reads and writes all of VRAM with no MMU in front of it (→ [V.4](sec_ai_v#v4), [V.16](sec_ai_v#v16)).
  NOTE: One wrinkle travels with it, and it answers the aperture-addressing question from an angle that first pass did not expect. The aperture shows 32 KB at a time and `VRAM_PAGE` is privileged, so **a user-space server pays a syscall every time its writes cross a 32 KB boundary**. Reprogramming costs one byte store and no stall — the cost is the call, not the hardware — so the mitigations are to keep the list arena, string cache and decoration assets within few pages, and to let the ioctl take page *and* offset. If crossings dominate in measurement, list building moves into the kernel with the compositor: one module, not a redesign (→ [V.18](sec_ai_v#v18)).
- Q63 — **Ports, signals and messages in the syscall table** — the first addition to [J.3](sec_ai_j#j3)'s dispatch table since it was written, and it deserves the scrutiny [D23](sec_ai_q#d23) applied to power. Five calls: `port_create`, `port_send`, `port_recv`, `task_wait`, `task_signal`, with **fixed 32-byte messages copied by the kernel** and bulk payloads through the `mshare` that already exists. They pass the test `sys_poweroff()` failed — general primitives, not one subsystem's verb in a syscall's clothes. **What must not happen is two blocking mechanisms**: [N.3](sec_ai_n#n3) already has per-device blocked queues, and a process waiting on a device *and* a message would have no single place to wait. Fold the device queues onto signal bits so `task_wait` is the only blocking primitive, or do not add it (→ [V.28](sec_ai_v#v28), [V.29](sec_ai_v#v29)).
  NOTE: The cost to design against is **~12 µs per message** — ~100 cycles of kernel copy at 8 MHz. Fine for window notifications and input events, and the reason **motion coalescing is not optional**: never more than one `EV_MOUSEMOVE` per frame per client. It also puts a requirement on [Q4](sec_ai_q#q4)'s outstanding HID event format — an event must fit 32 bytes and must carry **absolute position and a button bitmap**, because a format expressed as deltas and edges cannot be coalesced at all.
- Q64 — **`DRAW_GLYPHS`, and it is complementary to the string cache rather than a replacement for it.** One command taking `(font_base, glyph_w, glyph_h, string_ptr_in_sdram, count, dx, dy)`. Costed against an 80-character line: per glyph is ~1.5 ms of CPU emission, a cached composed string is ~18 µs but ~1.5 ms the first time, and `DRAW_GLYPHS` is ~80 µs **with no first time**. So **the cache wins for stable labels and `DRAW_GLYPHS` wins for text that changes** — the editor, the terminal, the file listing, which is what a desktop is for. A 128 × 32 console repaint is ~3.2 ms against ~76 ms per glyph. It also deletes 256 KB of strip and all the LRU machinery. Cost it in LUT and EBR against the 128-glyph font relief before committing to either (→ [Q61](sec_ai_q#q61), [V.26](sec_ai_v#v26)).
- Q65 — **Command-list fetch is a fifth arbiter stream and [D38](sec_ai_q#d38) never counted it.** During a composite pass the command processor fetches from SDRAM while the blitter reads a backing store and writes the back buffer. For an even-numbered window those are three different banks and the invariant holds; **for an odd-numbered window the fetch and the pixel read are both in bank 3** and every alternation costs a PRECHARGE and ACTIVATE. The traffic is small — a 20-window composite list is a few hundred bytes — but the stall is per crossing, not per byte. Three answers are available: give the lists a bank, interleave window parity so a backing store and the list describing it are never in the same bank, or measure and conclude it is noise. **Cheap now, awkward at G2** (→ [V.32](sec_ai_v#v32)).
- Q66 — **The blitter reaches 16 MB, not 64, and it should be said in sheet T1 rather than inferred.** `DISPLAY_BASE`, `DRAW_BASE`, `LIST_BASE` and sheet T3's four channel pointers are all **24-bit** ([T1.48](sec_ai_t1#t148), [T3.19](sec_ai_t3#t319)), and [T3.16](sec_ai_t3#t316)'s partition is written as four 4 MB ranges spanning `$000000`–`$FFFFFF`. Nothing in the GUI needs more — at 8 bpp a hundred backing stores is 12 MB and the framebuffers 1.2 — but it means **the partition is a 16 MB window into the device, not a division of it**. Decide whether the address registers widen to 26 bits or the upper 48 MB is simply unaddressable by the drawing engine, and write it down either way (→ [V.33](sec_ai_v#v33)).
- Q67 — [[!blocking]] **Are the i9 extension board's PMOD headers direct, unbuffered, bidirectional FPGA I/O?** Several Colorlight products route GPIO through unidirectional 74HC245 buffers; the module itself carries raw balls to the SODIMM, so this concerns the extension board alone. If they are buffered the 65816 data bus cannot be wired to them and [P2.19](sec_ai_p2#p219)'s Stage A is dead as written. **Moot if Stage A is skipped** in favour of going straight to the carrier PCB, which is the cheaper way to close this question — continuity meter on arrival, or do not buy the extension board at all.
- Q68 — [[!blocking]] **Ball assignment for the prototype**: map [P2.05](sec_ai_p2#p205)'s 82 signals onto specific i9 balls, respecting ECP5 bank grouping and keeping the CPU bus inside as few banks as practical. It is [E0.5](sec_ai_p3#e05) again on different silicon, with one extra constraint the target board does not have — the SODIMM's own zoning, which decides which signals may share a block at all.
- Q69 — **Clock plan for the merged die**: PLL outputs for the Helium domain, the Neon domain and the pixel clock, from the module's 25 MHz on P3, with [P2.14](sec_ai_p2#p214) requiring the two core domains to be genuinely separate. Confirm the ECP5's PLL count covers it before the first module is written. The target board answers the same question with three devices and one oscillator ([B.7](sec_ai_b#b7)); here it is one device and one oscillator, which is harder rather than easier.
- Q70 — **Measured current draw of the i9 module**, PHYs running and held in reset. [P2.20](sec_ai_p2#p220) budgets ~500–700 mA held down and ~700 mA–1.1 A running, and both are unmeasured estimates. It decides whether USB-C at 3 A is comfortable or merely adequate, and it is measured at [P0](sec_ai_p2#p0) with a bench supply before the carrier schematic is finalised.
- Q71 — **R-2R ladder values and termination**, verified against a 75 Ω monitor input. 6-bit ladders need 1 % resistors and the loaded output has to be checked rather than assumed; a ladder that is right in theory and 20 % low into 75 Ω produces a picture that looks fine until someone compares two monitors.
- Q72 — **The prototype's target PHI2 on the carrier.** Stage A is fixed at 1–2 MHz by the wire-wrap ([P2.19](sec_ai_p2#p219)); Stage B should run the target's 8 MHz ([B.1](sec_ai_b#b1)), but that is an intention rather than a measurement — the shared nets have three loads on a carrier with a SODIMM connector in the path, which the target board does not have. **Every stall and fill number taken below 8 MHz is an existence proof and nothing more**, and the sheet should say which clock each measurement was taken at.
- Q73 — **Which parts of G0–G8 are unreachable without a power path.** [P2.02](sec_ai_p2#p202) drops battery, charger, gauge and sequencing, so [sheet S](sec_ai_s)'s `$FF` power block has no hardware on the carrier and everything resting on it — the battery indicator, the shutdown dialogue, the stale-telemetry behaviour of [E8](sec_ai_p3#e8)'s test list — cannot be exercised. Decide whether those are stubbed against a simulated power block on the prototype or simply deferred, and write the answer into [sheet V](sec_ai_v)'s staging rather than discovering it at G6.
- Q74 — **A cache flush that never completes has no recovery path, and no existing watchdog covers it.** [F.11](sec_ai_f#f11)'s watchdog bounds a cache fill and [R.17](sec_ai_r#r17)'s bounds a debug transaction, but both work by resuming a stalled PHI2 — and the asynchronous flushes of [M.6](sec_ai_m#m6) deliberately never stall it, so neither applies. A hung SDRAM controller leaves the kernel spinning on `BUSY` indefinitely, with no clock stopped and no fault raised. Wanted: a counter in Helium bounding `CACHE_FLUSH_FRAME` and `CACHE_FLUSH_ALL`, escalating to NMI or `ABORTB` — which also means spending one of the bits `FAULT_CAUSE` currently reserves at 15:6.
- Q75 — **Where the `COP` signature byte lands on the stack** — `PC−1` or `PC−2`, verified against the WDC manual rather than inferred. [J.3](sec_ai_j#j3) takes the service number from the accumulator and no longer reads the byte, so nothing on the syscall path depends on the answer; a tracer, a disassembler or a static binary verifier does, and a wrong constant there produces a silent misdispatch rather than a visible failure.
- Q76 — **Shutdown has no mute step, and the power-down click was never considered.** The RC on the DAC's `XSMT` exists because a rail edge through an un-muted PCM5102A is a click in the headphones ([sheet H](sec_ai_h)); it protects power-**up** only. [S.13](sec_ai_s#s13) sequences an orderly shutdown all the way to `POWER_CTRL` with nothing muting the output, and the power-down click is the more audible of the two because the listener still has the headphones on. Two parts, both cheap and both needing to be decided together: **`XSMT` driven from `AUD_CTRL.MUTE`** rather than strapped, costing one Neon pin against the 99 of [W.38](sec_ai_w#w38), and **a mute step inserted between stopping the window server and flushing the filesystem** — after the session's last sound, before the switched domain moves (→ [W.40](sec_ai_w#w40)).
- Q77 — **The sample rate is 44,146 Hz and the question is whether to write that down or spend a part on 44,100.** No PLL setting reaches either standard rate from the board's 25 MHz oscillator: the iCE40 PLL is integer-only and **44.1 kHz needs a denominator factor of 441 = 3² × 7², 48 kHz one of 3,125 = 5⁵**, neither expressible as `(DIVR+1) ≤ 16` times a power of two ([W.11](sec_ai_w#w11)). So the second PLL cannot help audio at all, and **audio's half of [Q54](sec_ai_q#q54) is closed** — not weakened, as [T1.9](sec_ai_t1#t19) has it. The integer divisor 73 at 32fs gives +0.104 %, **1.8 cents of pitch and 3.75 s/hour of drift**, against two exact alternatives that are both refused here: a second oscillator breaks [B.7](sec_ai_b#b7)'s one-oscillator star, and a fractional NCO hands the DAC's internal PLL a `BCK` jittered by a full 9.7 ns clock period. **The recommendation is to accept it and publish it in `AUD_RATE`**, so no piece of software ever assumes a rate the hardware is not producing (→ [W.9](sec_ai_w#w9), [W.12](sec_ai_w#w12)).
- Q78 — **What happens when a fifth process wants sound.** Four hardware channels are a finite resource and there is no software mixer available to virtualise them — [W.1](sec_ai_w#w1) is arithmetic, not preference: the 65816 has 181 cycles per stereo frame at 8 MHz and mixing four streams does not fit in them. The recommendation is the interface that admits it: **channel 3 reserved for the session's system sounds, channels 0–2 allocated to `open` in order, `ENODEV` to the fourth caller** — rather than silently folding a late arrival into somebody else's channel. What is still open is whether the window server may **preempt** an application's channel for an alert, which is a session-policy question of the same shape as [S.14](sec_ai_s#s14)'s cancellation dialogue and belongs with [sheet V](sec_ai_v) rather than with the driver (→ [W.44](sec_ai_w#w44)).
- Q79 — **When the SD DMA engine is actually built, and what stands in for it until then.** [D45](sec_ai_q#d45) specifies both paths but they are not the same size of job: the FIFO is a page of gateware, the DMA engine is an arbiter client with a coherence rule and a `CACHE_INVAL_FRAME` beside it. The staging that falls out of this is that [E6](sec_ai_p3#e6) and [P5.j](sec_ai_p2#p5j) can be reached on the FIFO alone, with the block driver already written against the DMA register names so nothing above it changes when the engine lands. What has to be decided is whether that is deliberate staging or an accident waiting to become permanent — **a FIFO-only machine cannot page**, and the swap reserve of [G.4](sec_ai_g#g4) is the feature the whole card topology was chosen for.
- Q80 — **The SPI-SD clock, and whether the card can be driven fast enough to matter.** Every throughput figure in [sheet G](sec_ai_g) assumes 25 MHz — the ceiling for SPI mode on a modern card, and one this board has no reason to miss — but the number is inherited rather than measured, and it is derived from Helium's core clock by an integer divisor that also has to produce ≤ 400 kHz for initialisation ([G.11](sec_ai_g#g11)). Both divisors, the achievable rate on real cards — now over a direct connection rather than through the '3257, which removes a stub and a switch resistance from the measurement ([G.1](sec_ai_g#g1)) — and the resulting per-block time belong in one place before the block driver's timeouts are written against a guess.
- Q81 — [[!blocking]] **How many expansion slots the board carries, and it is the only variable in [sheet X](sec_ai_x) that fights [Q8](sec_ai_q#q8).** One slot is three pins of Helium, two are four, and none is zero — every other cost in that sheet is a connector, a '573 and a '245, none of which touches the FPGA. The question is not really "how many": it is **whether a slot survives a pin budget that does not close for the interfaces the machine cannot boot without**, and the honest ordering is that SPI-SD, the UART and the debug port are all senior to it. What must not happen is the decision being taken by default at layout, because the connector and its buffers are cheap to route now and impossible to add later (→ [X.3](sec_ai_x#x3), [Q27](sec_ai_q#q27)).
- Q82 — **Base addresses for the slot windows and the slow-bus block within bank `$FF`** — `$FF:7E00` and `$FF:7F00` for the slots is a proposal chosen for being at the top of Helium's half, and the slow bus has no proposal at all. Both are part of [Q22](sec_ai_q#q22) rather than separate from it, and they are the two allocations in that bank that can still be moved for nothing (→ [X.7](sec_ai_x#x7)).
- Q83 — **The aperture's frame range and, more importantly, its size.** [X.8](sec_ai_x#x8) proposes frames `$F000`–`$F1FF` and `$F200`–`$F3FF` out of the half [F.10](sec_ai_f#f10) leaves unpopulated; the range is arbitrary and the **1 MB size is not** — it is exactly what A0–A19 reaches, and widening it means new pins on a budget that has none. Two things to settle with it: whether the range should sit at the very top of the frame space so that a future second SDRAM device could still grow contiguously beneath it, and whether the kernel's frame allocator needs to know the range exists at all or simply never receives those numbers (→ [Q81](sec_ai_q#q81)).
- Q84 — **Ratifying the card contract, which is the part of [sheet X](sec_ai_x) that outlives the project's own hardware.** `SLOT_ID`, `SLOT_CLASS` and `SLOT_STATUS` at fixed offsets are what make enumeration and interrupt demultiplexing cost nothing ([X.13](sec_ai_x#x13), [X.14](sec_ai_x#x14)) — but a class numbering that is invented one card at a time becomes unfixable, and the obligations of [X.20](sec_ai_x#x20) are a promise made to people who will never read this document. Wanted: the class list, and the contract restated on a single page that ships with the connector rather than inside a synthesis document.
- Q85 — **The slow bus is specified as a mechanism and not yet as a register file.** [D49](sec_ai_q#d49) settles the shape — mirrors refreshed by a sequencer, [S.16](sec_ai_s#s16)'s staging → live → shadow, a raw-transaction escape for initialisation — and leaves open how many windows there are, how large each may be, the descriptor encoding, what the sequencer does when several windows come due in the same pass, and whether the raw escape is enough to bring up every device this tier is likely to host. The map in [sheet X](sec_ai_x) is a proposal at that resolution and is marked as one. **Nothing depends on it yet**, which is the argument for writing it against a real second tenant rather than against an imagined one (→ [X.28](sec_ai_x#x28)).
- Q86 — **Where the expansion tiers land in the E-series, and the answer should be "late".** Neither is required by a milestone: [E6](sec_ai_p3#e6) boots without them and [E8](sec_ai_p3#e8) is a laptop without them. What is required *now* is schematic space and reserved pins before layout ([E1.3](sec_ai_p3#e13)), which is the classic shape of a decision that gets taken by omission. The staging that suggests itself is the slow bus first — it is a sequencer and a table, and the RTC is a real tenant — with the parallel slot's gateware after the machine has something to plug into it, and both entered on [sheet P3](sec_ai_p3) rather than left in this sheet (→ [X.30](sec_ai_x#x30)).
- Q87 — **Where the filesystem work goes in the sequential plan, and it is one question rather than three.** [Sheet Y1](sec_ai_y1)'s V0–V5, [sheet Y3](sec_ai_y3)'s E2.0–E2.7 and [sheet Y4](sec_ai_y4)'s [FUS-00–FUS-09](sec_ai_y4#fus-00) are three gate series that were each written without the others in view, and **[V2](sec_ai_y1#v2) gates [E2.1](sec_ai_y3#e21)** — the NVFS driver has to move behind the vnode table before a second driver is written against it — while [FUS-04](sec_ai_y4#fus-04) is the host-side rehearsal of both. None of them is currently slotted against [P5](sec_ai_p2#p5) or [E6](sec_ai_p3#e6), and the calendar cost of inserting them before the Apple II milestone needs an explicit decision rather than a default. **[Q175](sec_ai_q#q175) has changed the shape of this**: the host series is no longer free-standing at its last four gates.
- Q88 — [[!blocking]] **Nothing on this board holds a wall clock, and the filesystem needs one.** Timestamps are `u32` seconds since 1970; with no source, every file the machine writes carries zero — which the format defines as "unknown" and `nvfsck` must not report as an error ([Y2.4](sec_ai_y2#y24)), so nothing breaks, but nothing on the card can be dated either. The options are a real-time-clock part, which is a board change; the EC holding time across a battery-backed always-on domain, which is nearly free given [C.9](sec_ai_c#c9) already keeps that domain alive; or the user setting the clock at each boot, which is honest and irritating. **This is a hardware gap rather than a filesystem question and it should be settled before the board is frozen**, because the middle option costs nothing if it is designed in and a part if it is not ([I.4](sec_ai_i#i4), [Y1.17](sec_ai_y1#y117)).
- Q89 — **NVFS journal sizing gives 1.6 % of the volume to the journal at every size, and on a large card that is too much.** The default ring is `total/64` clamped to 256–8192 blocks, which is 1 MiB on a 64 MiB volume and 128 MiB on an 8 GiB one. A cap of about 4096 blocks is proposed. It affects `mkfs` only, and existing volumes are unaffected ([Y2.5](sec_ai_y2#y25)).
- Q90 — [[!blocking]] **Does NVFS expose a stable 32-bit file identifier that survives modification?** [Y1.7](sec_ai_y1#y17)'s vnode cache is keyed on it, and the inode number plus `i_generation` satisfies it — but this has to be confirmed against the implementation rather than the specification **before [V0](sec_ai_y1#v0)**, because if any identity in NVFS turns out to be derived from extent location or anything else that changes on write, either the cache key or the format has to move.
- Q91 — **The shared block cache carries a hook only one driver uses, and that is a smell worth stating.** [D55](sec_ai_q#d55) chose it because the alternative's cost — two caches, two pools, no global LRU — is permanent while this one's is a single field. The counter-argument is that a mechanism with one user is a mechanism nobody maintains. Revisit at [V5](sec_ai_y1#v5), which may trail [V4](sec_ai_y1#v4) with ext2 on a private cache in the meantime.
- Q92 — **Is the host track's internal table path-keyed or inode-keyed?** libfuse offers both shapes and **only the inode-keyed one transfers**, because path resolution, symlink following and mount crossing are all VFS responsibilities here and a driver never sees a path ([Y1.21](sec_ai_y1#y121), [Y4.6](sec_ai_y4#y46)). Cheap to fix at one implementation and expensive at three, so it is checked before the first filesystem gets far.
- Q93 — **NVFS does not store `..`, and a directory's link count is therefore always 2 rather than 2 + subdirectories.** That removes the link-count bookkeeping which is a persistent source of `fsck` errors, at the cost of a directory found by inode number having no path back to its parent, and of a host binding having to synthesise the POSIX count if any tool depends on it. **There are 8 reserved bytes in the inode** if a stored parent is ever wanted instead. Confirm the trade or spend them ([Y2.13](sec_ai_y2#y213)).
- Q94 — **The vnode cache size and the per-process descriptor table size are both guesses** — 24 and 16 — and should be revisited once the GUI's file access patterns are known rather than before. The cache must exceed the maximum number of simultaneously open files by a margin, since directory vnodes along active paths are held too ([Y1.15](sec_ai_y1#y115)'s budget table).
- Q95 — **Is there a `devfs`, or do character devices stay outside the filesystem namespace?** [J.4](sec_ai_j#j4) routes an `open` either to the filesystem or to the device table, which works and is not a namespace. Putting devices inside it is what would require `open` and `close` slots in the per-vnode table that [Y1.10](sec_ai_y1#y110) deliberately omits — two slots, added cheaply at that point, but only if the question is asked before [V3](sec_ai_y1#v3) rather than after.
  NOTE: **Answered for now by [D108](sec_ai_q#d108)**: `open` resolves `/dev/` by prefix against the device table, and a devfs mount — with the `open` and `close` slots — arrives when something needs to list devices ([CN1.15](sec_ai_cn1#cn115)).
- Q96 — [[!blocking]] **Can an SD card's write cache be reliably flushed, and if not, what do the durability guarantees actually mean?** [Y2.16](sec_ai_y2#y216)'s journal assumes a write is durable once the card leaves the busy state and `CMD13` confirms it; [Y3.9](sec_ai_y3#y39)'s ordering rules assume the same of every flush point. SD has no cache-flush command comparable to eMMC's. **If the assumption is wrong, both filesystems' crash-consistency arguments are weaker than they are written**, and the way to find out is a power-loss rig rather than a datasheet. Verify during SD bring-up and record the result ([G.11](sec_ai_g#g11)).
- Q97 — **`data=ordered` costs a barrier per transaction, and the cost has not been measured.** [Y2.18](sec_ai_y2#y218) forbids the faster alternative because letting data lag the commit exposes the previous occupant of a reallocated block through a newly written file, which on a single-user machine with no other protection is both a correctness and a privacy failure. **If the barrier proves intolerable the alternative is journaling small writes with the metadata, not relaxing the rule.** Measure before the format is frozen.
- Q98 — **Is the ext2 driver required to handle arbitrary host-created volumes, or only one documented `mke2fs` invocation?** The answer decides how much of [Y3.4](sec_ai_y3#y34)'s feature table has to be implemented rather than merely refused, and whether [Y3.6](sec_ai_y3#y36)'s htree handling is needed at all — formatting with the index off removes that problem at source.
- Q99 — **Resident or loadable: ~19 KB of ext2 driver competes with the kernel for a bank.** Read-only is ~9 KB, and the VFS is ~5.5 KB on top of whatever NVFS costs ([Y1.15](sec_ai_y1#y115), [Y3.13](sec_ai_y3#y313)). **Address space is the constraint rather than code size**, and there is no loadable-module story in this document. Check it against [J.1](sec_ai_j#j1)'s bank `$01` before [E2.1](sec_ai_y3#e21), not after.
  NOTE: **[D102](sec_ai_q#d102) takes away the single bank**: the kernel now grows down from `$FD` to a reserved floor at `$F0`, so a resident driver no longer has to fit beside the rest of the kernel in 64 KB. What stays open is the share of pinned SRAM ([Q9](sec_ai_q#q9)) and whether a loadable-module story is wanted for its own sake.
- Q100 — **ext2's pinned group descriptor table does not scale.** 8 KB for a 2 GiB volume, **128 KB for a 32 GiB card** ([Y3.14](sec_ai_y3#y314)), which is not payable. Either an LRU sub-cache over the descriptors or a stated maximum supported volume size, decided before the write path exists.
- Q101 — **Read-only ext2 or read-write, which is the largest single scope decision in the filesystem stack.** [D54](sec_ai_q#d54) recommends read-only: it covers the actual use case at roughly a quarter of the cost and carries none of the risk of destroying data rather than merely failing to read it. The write path should be revisited only when a concrete need to write ext2 on this machine appears ([Y3.16](sec_ai_y3#y316)).
- Q102 — [[!blocking]] **Verify a Low Speed device behind the hub, on real hardware, with a real keyboard.** The host must emit a `PRE` packet before each Low Speed transaction, and that is historically the most fragile path in this family's host stack. It is [U6](sec_ai_d1#u6), and it is the gate on which the machine either has a keyboard or does not ([D1.10](sec_ai_d1#d110)).
- Q103 — **What happens when a user plugs a hub into a downstream port.** The on-board hub consumes the single guaranteed level, and in a portable computer a second one will be attached. The tier limit has to be raised and multi-level handling verified rather than assumed; **the fallback is defined now — detect the downstream hub during enumeration and refuse it with a console message rather than failing silently** ([D1.10](sec_ai_d1#d110), [U7](sec_ai_d1#u7)).
- Q104 — **Confirm the EC's stepping from the package marking on the parts as received**, not from the distributor's part number. It is a two-minute check on delivery and an expensive discovery afterwards ([D1.8](sec_ai_d1#d18)).
- Q105 — **Validate every EC GPIO assignment against the part's function-mux table.** [D1.6](sec_ai_d1#d16) closes the pin *count* with room to spare; that is a different exercise from confirming each function can actually be reached on the pin it was assigned to, and it belongs before schematic capture ([Q41](sec_ai_q#q41) reduced to this).
- Q106 — **How `JP-BYPASS` is implemented, and whether it survives to production.** A 3-pin shunt or two 0 Ω pads with one populated; at 12 Mbps either is electrically free. It is worth keeping on the prototype for certain — it is the only thing that separates "the host stack does not work" from "the hub does not work" ([D1.11](sec_ai_d1#d111)).
- Q107 — **Write and archive the RAM flash-writer stub — worth doing, no longer blocking anything.** Tier 2 recovery writes only SRAM, so without the stub it cannot reach flash at all, and **a recovery tool that has to be rebuilt from source during an emergency is not a recovery tool**. About 200 lines, verified by CRC-32 readback, archived beside every EC firmware release ([D1.14](sec_ai_d1#d114)).
  NOTE: **Downgraded from blocking.** [D59](sec_ai_q#d59) left tier 2 with only the case where SWD is physically broken and the bootrom still answers, and [D65](sec_ai_q#d65)'s A/B slots give the EC a second complete image to fall back on besides. The stub is still the only thing that makes tier 2 reach flash at all, so it keeps its own justification — it stopped being the thing that has to exist first.
  NOTE: **Downgraded by [D59](sec_ai_q#d59): the stub comes off the critical path before E0.** Tier 2 only contributes where SWD is physically broken but the bootrom is still reachable, and the integrated probe of [D57](sec_ai_q#d57) covers a blank flash, a corrupt flash and a self-resetting device without it. The stub remains worth writing and archiving; it is no longer blocking ([D2.23](sec_ai_d2#d223)).
- Q108 — **How much of the QSPI bus is exposed on `J-QSPI`, and how it is guarded.** Those nets reach the in-package flash die, so the header trades recovery access against noise coupling into the running system: short stubs, routed away from the SDRAM and both switching nodes, ground-guarded if there is room, series damping on the header side ([D1.15](sec_ai_d1#d115)).
  NOTE: **Closed by [D59](sec_ai_q#d59), and closed by removing the header rather than by guarding it.** Six pads beside the package, pogo or clip access, no cable and no probe connection — the stubs are millimetres instead of tens of them, and if layout cannot even manage that, tier 3 goes ([D2.22](sec_ai_d2#d222)).
- Q109 — **Which hub IC.** The documented four-port part with per-port power control and overcurrent sense is recommended on no-black-boxes grounds; a cheaper SSOP part with gang-only control is defensible if hand-assembly ease dominates on the prototype. **Confirm the Hi-Speed-to-Full-Speed upstream fallback on the actual part** before committing ([D1.16](sec_ai_d1#d116)).
- Q110 — **Downstream power policy: an aggregate hardware limit, or `bMaxPower` accounting in EC firmware.** Worst case is 1.55 A and 7.75 W from a 1S battery, which is not deliverable. **The firmware policy is preferable** — it is the honest behaviour, it is visible to the user, and it is the kind of policy an EC should own — with the hardware limit as the fallback if the boost converter cannot carry the transients ([D1.17](sec_ai_d1#d117)).
- Q111 — **Verify the TPS61023's output capability at the chosen aggregate USB limit with the battery at 3.4 V**, before the schematic is frozen. It is the same converter [D1.5](sec_ai_d1#d15) already enables on demand, now asked for considerably more ([C.10](sec_ai_c#c10)).
- Q112 — [[!blocking]] **Confirm on the received module that `CKE`, `CS#` and the `DQM` lines of its SDRAM are tied off rather than driven.** The finding is community reverse-engineering rather than a vendor document, it is a continuity check that takes minutes, and it decides whether the carrier must carry its own SDRAM — which [P2.11a](sec_ai_p2#p211a) argues it must, and which invalidates most of [P2.11](sec_ai_p2#p211)'s allocation if it holds.
- Q113 — **`XSMT` should be driven rather than strapped, and the open half is which party drives it.** A Neon pin is natural while the machine runs and wrong at both edges that matter; the EC is awake before Neon is configured and while the rails come down, which is [T1.52](sec_ai_t1#t152)'s argument for the backlight applied unchanged. **No functional strap belongs on a passive-only net** ([W.7](sec_ai_w#w7), [W.40](sec_ai_w#w40), [Q76](sec_ai_q#q76)).
- Q114 — **Calypsi's default far pointer is 32 bits, not the 24 this document assumed**, and the correction reaches the ABI rather than the prose: struct layout, the calling convention and every kernel and driver bank-crossing convention depend on which qualifier each object takes. `__far24` should be preferred wherever a far pointer is unavoidable — the fourth byte is dead weight in a 24-bit address space. Settle it per object in [E0.8](sec_ai_p3#e08)'s audit, against compiled output rather than the manual ([O.2](sec_ai_o#o2)).
- Q115 — **`ABORTB` cannot trap `WAI` or `STP` executed by unprivileged code**, so a user process can halt the machine. A watchdog is the cheap answer and the EC already holds one ([D1.7](sec_ai_d1#d17)); opcode detection at fetch inside Helium is the complete one and is what another FPGA-based 65816 machine already does for a different purpose. Decide before untrusted code is run, which is later than it sounds ([E.22](sec_ai_e#e22)).
- Q116 — [[!blocking]] **The ABORT go/no-go bench test, and it comes before the OS design is committed rather than after.** Assert abort on a plain load and confirm the correct address is stacked, `RTI` re-executes it, and every register is intact; repeat on a store and confirm the write was gated. **If plain accesses are not reliably restartable on the actual silicon, the fallback is a stall-only design with statically mapped banks**, and that is a different operating system ([E.24](sec_ai_e#e24), [P3.k](sec_ai_p2#p3k)).
- Q117 — **What to do if the 103.125 MHz domain will not close on the prototype's speed grade.** Ranked: pipeline harder, drop the pixel clock, then — last — cross-check the timing in the vendor's proprietary tool. The third is worth naming precisely because [A2.6](sc_a2#a26) makes the open toolchain a principle: checking a design the open flow builds is a smaller concession than building with it, and it is still one ([P2.25](sec_ai_p2#p225)).
- Q118 — [[!blocking]] **Retrieve the official Raspberry Pi Debug Probe schematic and identify the input buffer on the `SWDIO` and UART RX read paths** — part number, supply, and above all **its behaviour when the target is unpowered**, since that is state S1 and S3 of [D2.16](sec_ai_d2#d216) and [D2.17](sec_ai_d2#d217). Zephyr's board documentation confirms the separate drive and sense GPIO but does not name the device. Nothing can be captured without it ([D2.9](sec_ai_d2#d29)).
- Q119 — [[!blocking]] **Check the RP2354B's absolute maximum clamp current against the calculated 16.5 mA per line through 200 Ω.** If the margin is inadequate the termination rises to 220 Ω or 330 Ω per side, and the slew-rate cost has to be re-evaluated against the maximum SWD clock rate — which is a schematic change, not a layout one ([D2.18](sec_ai_d2#d218)).
- Q120 — [[!blocking]] **Confirm that the RP2354B's `SWDIO` carries an internal pull-up.** [D2.16](sec_ai_d2#d216) assumes it, and on that assumption `SWDIO`'s idle backfeed in the machine's normal state is tens of microamperes and ignorable. **If the pin floats, or pulls down, `DBG_SWDIO` needs the same gating treatment as `DBG_UART_TX`** and the interface grows a second software-gated line.
- Q121 — **Does the RP2350 bootrom's UART boot path need an OTP enable bit, or is it live by default?** If it must be enabled, **tier 2 is not a rescue mechanism at all** but something provisioned during manufacture, and that belongs in the production flow rather than in a recovery procedure ([D2.23](sec_ai_d2#d223), [D1.14](sec_ai_d1#d114)).
- Q122 — **Define the relationship between `DBG_VBUS_SENSE` and the Debug Agent's `DEBUG_ENABLE` strap** — and note that **[Q125](sec_ai_q#q125) may close this outright** by removing the second of the two.  They overlap in purpose — one says a debugger is attached, the other gates the agent — and the questions are whether probe presence gates agent availability, whether either can disable the other, and what the production posture is. **What must not happen is `DBG_VBUS_SENSE` quietly becoming a second undocumented enable** ([D2.14](sec_ai_d2#d214), [R.18](sec_ai_r#r18)).
- Q123 — **Reconcile `DBG_UART_RX`, `DBG_UART_TX` and `DBG_VBUS_SENSE` against the full EC pin budget before capture.** The UART pair is *proposed* on GPIO0/GPIO1 and the sense pin is unallocated. The budget was rescued once by the part change ([D1.6](sec_ai_d1#d16)) and this is a third claim on it, alongside battery I2C, Helium SPI, the regulator enables and USB host — and it is the same exercise as [Q105](sec_ai_q#q105) rather than a separate one ([D2.12](sec_ai_d2#d212)).
  NOTE: **Two of the claimants this entry listed no longer exist.** The SD mux went with [D60](sec_ai_q#d60) — six EC pins returned — and **there is no keyboard matrix**, which [D1.5](sec_ai_d1#d15) removed in favour of USB HID and this entry was still carrying. The EC-side count that replaces it is [D3](sec_ai_d3)'s 27 pins of boundary signals against 48 ([Q126](sec_ai_q#q126)).
- Q124 — **Whether the probe MCU should be an RP2354A instead, removing its external flash from the BOM.** Deferred rather than open: `debugprobe` support for RP2350 as *host* is unverified, and [D57](sec_ai_q#d57) chose the proven path deliberately. **Revisit only if BOM pressure justifies the verification effort**, and never during the first spin ([D2.4](sec_ai_d2#d24)).
- Q125 — [[!blocking]] **Does `DEBUG_ENABLE` survive, now that the EC writes system memory on every boot?** **Still open, and REV C has removed the argument that kept half of it alive.** The two-slave framing this question was written on is gone: there was one strap in front of the Debug Agent and an ungated `MEM_WRITE` beside it in the mailbox, so it could be said that the strap withheld real capability and merely failed to withhold memory. **With one link, `MEM_WRITE` withdrawn and the boot load riding endpoint `0x02`, the strap is in front of the boot** ([D80](sec_ai_q#d80), [D82](sec_ai_q#d82), [D3.2](sec_ai_d3#d32)). **So if the strap is kept it can no longer be a gate at all** — it becomes a selective decode inside one endpoint, permitting `WRITE_BURST` while refusing halt, step, trace and register access, which is the dispatch convention [D81](sec_ai_q#d81) says a chip select never made structural anyway ([R.18](sec_ai_r#r18), [R.25](sec_ai_r#r25)). What is left standing is only [R.18](sec_ai_r#r18)'s own claim, that the privileged path should be *an explicit, visible, deliberate state of the board*, and **the question is whether that is worth a pin, a jumper, a footprint and a selective decode.** If it goes, six places go with it — [R.8a](sec_ai_r#r8a) and its NOTE, [R.18](sec_ai_r#r18), [R.23](sec_ai_r#r23)'s pin accounting, [D25](sec_ai_q#d25) and [Q38](sec_ai_q#q38) (both of which exist only to carve exceptions *out* of the gate), [Q27](sec_ai_q#q27)'s strap and jumper footprint, [Q122](sec_ai_q#q122) (which closes outright), and [P3.f](sec_ai_p2#p3f). **What does not turn on the answer is the isolation of the agent from software, which is [D81](sec_ai_q#d81)'s INV-1 and rests on connectivity** ([R.26](sec_ai_r#r26)). It is a schematic-capture item either way.
- Q126 — [[!blocking]] **The formal TQ144 pin count for Helium, and it is the gate on schematic capture.** [D3](sec_ai_d3) now charges it **11** — SPI, one chip select, `ATTN` and the six permanent microSD lines — **additive to** the CPU bus, SRAM, SDRAM and the 32-signal multiplexed Neon link. Nothing has ever added all of those up on one page. **The cheap relief this question used to name has been spent**: the chip-select merge is taken ([D80](sec_ai_q#d80)) and the `CFG_SS_A` variant of it is rejected on hardware grounds ([D86](sec_ai_q#d86)), so **if the count still comes out short what remains is HX8K in CT256**, which changes the footprint and the hand-solderability argument with it ([Q8](sec_ai_q#q8), [Q27](sec_ai_q#q27)).
- Q127 — **Measure a real bitstream and a real `bios.bin` before [D1.21](sec_ai_d1#d121)'s flash layout is frozen.** The ~135 KB figure is a device-class estimate, and the layout's 600 KB slots are sized against it with margin that has never been checked. **One `icepack` run on a representative HX8K design settles it** — and the number will not move with utilisation, since iCE40 bitstream size is fixed by the configuration SRAM rather than by the design in it.
- Q128 — **Verify the RP2350 bootrom's partition-table A/B support against Raspberry Pi's documentation.** If it behaves as [D1.24](sec_ai_d1#d124) expects — two images, version numbering, automatic selection — **the slot selector need not be written by hand at all**, which is the difference between a bootloader and a table. **It must not be relied on before it is confirmed**: an A/B scheme whose selector turns out to need writing after the flash layout is frozen is a layout change, not a firmware one.
- Q129 — **What the running system does about the 30–50 ms during which the EC is deaf.** [D1.25](sec_ai_d1#d125) makes a flash erase a state in which there is no HID service, no link polling and no response of any kind — **indistinguishable from a hung EC, which is the one thing the 10-second watchdog exists to detect** ([D1.7](sec_ai_d1#d17)). Wanted: whether the watchdog is suspended or fed across the window, what the user is told, and what happens to keystrokes arriving during it. **A stall that is designed is a progress bar; the same stall undesigned is a bug report.**
- Q130 — **What the NVFS partition's reserved head is for now.** [Y2.5](sec_ai_y2#y25) reserved its first eight blocks so a boot image could sit at the front of the partition where an EC with almost no filesystem code could find it; **[D60](sec_ai_q#d60) means no EC ever reads it.** Keep it for [D1.24](sec_ai_d1#d124)'s update images, repurpose it, or return it to the filesystem — decide before `mkfs` is written, since the answer is in the on-disk format ([G.2](sec_ai_g#g2)).
  NOTE: [D107](sec_ai_q#d107) keeps the kernel image out of the NVFS partition altogether, so whatever the reserved head becomes, it is not the boot path ([CN1.5](sec_ai_cn1#cn15)).
- Q131 — **The monitor command set beyond [D3.14](sec_ai_d3#d314)'s initial six.** `md`, `mw`, `halt`, `run`, `regs`, `stat` and `slot` are the wozmon-class floor that makes the machine debuggable. What comes after is a question of what bring-up actually turns out to need — and the one structural note is that **bulk transfer should arrive as a separate binary or XMODEM command rather than as a reworking of the text protocol**, which would cost the three things [D66](sec_ai_q#d66) bought to fix the one it did not.
- Q132 — [[!blocking]] **Where the colour lookup block sits in Neon's register map.** [T2.16](sec_ai_t2#t216) names every register and commits to none of their addresses, because [T1](sec_ai_t1) already occupies `$FF:8000` with 256 bytes ([T1.22](sec_ai_t1#t122)) and [T3](sec_ai_t3) proposes its own offsets inside the same page. **Every piece of software that touches colour depends on the answer**, and it cannot be settled block by block: the CLUT ports, the blitter's channel registers and T1's existing file have to be laid out as one map or they will collide.
- Q133 — [[!blocking]] **Which block RAM relief is taken, now that three sheets claim the same one.** [T1.12](sec_ai_t1#t112) declared 32 of 32 with zero margin and named two reliefs as insurance. [T3.38](sec_ai_t3#t338) spent that insurance getting to 34 or 35 blocks; [T2.6](sec_ai_t2#t26) adds a third block for the second CLUT bank; [U1.13](sec_ai_u1#u113)'s full double line buffer at Full HD is larger than the 1 KB T1 budgeted. **The reliefs are a 128-glyph font (four blocks) and a 2-bpp cursor (half a block), and they no longer cover it.** This is decided before RTL and informed by synthesis, not after ([Q45](sec_ai_q#q45), [Q61](sec_ai_q#q61)).
- Q134 — **Cursor bit depth and cursor palette entry count, which have carried two numbers across three sheets.** [T1.31](sec_ai_t1#t131) says 2 bpp, [T2.11](sec_ai_t2#t211)'s source note says 4, [T3.29](sec_ai_t3#t329) reconciles to 2 bpp at 32 × 32 — 256 bytes, three colours plus transparent, half a block spare. **Take T3.29 and say so**, because the entry count of the separate cursor palette port follows from it and nothing else.
- Q135 — **The palette manager, and it is an operating system component that no sheet owns.** [T2.4](sec_ai_t2#t24) anticipates roughly 16 system colours, 200 general-purpose entries and a reserved remainder, which is an allocation policy — who reserves, who arbitrates between applications, and what happens when two want incompatible ramps. Wanted alongside it: the syscall ABI for palette operations, meaning COP signature bytes and the Calypsi calling convention. **Both have to exist before an application-level colour API can be defined at all** ([sheet V](sec_ai_v), [Q114](sec_ai_q#q114)).
- Q136 — **Confirm iCE40 block RAM read timing in the CLUT lookup path at whatever the pixel clock turns out to be.** The lookup sits between the line buffer and the output pad register and has one clock to do it in. It is a timing closure item rather than an architectural one, but it is on the path that cannot fail ([Q117](sec_ai_q#q117), [Q137](sec_ai_q#q137)).
- Q137 — [[!blocking]] **The pixel clock, and the document currently carries two.** [T1.4](sec_ai_t1#t14) and [T1.5](sec_ai_t1#t15) derive 103.125 MHz core and 51.5625 MHz pixel from the 25 MHz star, and [T1.8](sec_ai_t1#t18) buys a single clock domain with no crossing anywhere inside Neon from the memory system being exactly twice the pixel rate. [U1.16](sec_ai_u1#u116) needs **74.25 MHz** for a dual-channel Full HD panel. **Whether that is reachable from the same oscillator has not been checked, and if it is, the single-domain property is what has to be re-argued** — every bandwidth figure in [T1.13](sec_ai_t1#t113), [T1.14](sec_ai_t1#t114) and [T3.13](sec_ai_t3#t313) and the arbiter bound of [T3.27](sec_ai_t3#t327) are computed against 103.125 ([Q44](sec_ai_q#q44), [Q117](sec_ai_q#q117)).
- Q138 — **Which line-compare and interrupt register set survives.** [T1](sec_ai_t1) defines a raster counter, a compare register and an enable and write-1-to-clear status pair, over three sources — vertical blank, raster compare and the command list's signal. [T2.16](sec_ai_t2#t216) defines a logical line counter, a line compare, and its own enable and status pair over two. **They are the same mechanism named twice**, and the merge also has to settle whether the counter is logical or physical, which [U1.6](sec_ai_u1#u16) makes a real distinction rather than a naming one. The interrupt topology itself is unaffected ([T1.47](sec_ai_t1#t147)).
- Q139 — **Whether the reserved display list processor is a second engine or opcodes in the one already budgeted.** [T1.39](sec_ai_t1#t139) commits to a command processor executing lists from SDRAM with `WAIT_LINE` and a mid-frame `SET_PALETTE`, at 800 LUT and stage N5. [T2.14](sec_ai_t2#t214) reserves sixteen register offsets and an arbiter client for a Copper-class state machine doing per-line register writes. **Most of the second is the first**, and what is genuinely new is only the per-line register-write form. Deciding it releases either the reservation or the duplication ([T2.15](sec_ai_t2#t215)).
- Q140 — **Panel diagonal, 14 inch against 15.6 inch, and it gates more than the video block.** Chassis, battery, keyboard and moulding all follow from it, and [U1.26](sec_ai_u1#u126)'s market note runs the other way from intuition: replacement stock is deeper at HD, industrial availability is strongest at Full HD dual-channel.
- Q141 — [[!blocking]] **The specific panel part number and its datasheet extract**, meaning timings, colour mapping, channel split and unused-bit behaviour. It settles criteria C2, C5, C6 and C7 of [U1.26](sec_ai_u1#u126)'s table at once, and **C2 is the one that can disqualify a panel outright**: a left/right split rather than even/odd interleave takes the pin count from 22 back to 52 and makes the panel unusable ([U1.17](sec_ai_u1#u117)).
- Q142 — **Serializer pin assignment against Neon's TQ144 pinout, pending the formal pin budget.** [T1](sec_ai_t1)'s recount closes at 100 of ~107 with 22 pins on video, which is the same 22 [U1.20](sec_ai_u1#u120) needs — so the count does not move, but the *placement* of the video block against the SDRAM and CPU bus blocks has never been done ([T1.51](sec_ai_t1#t151), [Q126](sec_ai_q#q126)).
- Q143 — **Whether two independently-clocked SN75LVDS83B devices driven from a common clock meet the panel's inter-channel skew specification.** [U1.19](sec_ai_u1#u119) prefers two identical discrete parts over a purpose-built dual-channel one precisely because identical devices on an identical bus are trivially in phase — **and that is an argument, not a measurement.** If it fails, the fallback is a dual-channel part subject to the BGA restriction, or single-channel HD.
- Q144 — **Backlight boost converter and panel connector, both waiting on the same datasheet.** The converter needs the LED string voltage and current, and it lands in the power tree of [sheet C](sec_ai_c) rather than in the video block ([T1.52](sec_ai_t1#t152)). The connector is 30-pin against 40-pin and FFC against board-to-board, and it is mechanical and FPC routing.
- Q145 — [[!blocking]] **Whether the 10.1-inch RGB-TTL module of [D05](sec_ai_q#d05) stays as the prototype panel alongside the LVDS direction.** [U1.5](sec_ai_u1#u15)'s own table still calls it "the current prototype", which reads as two panels in two roles — but [sheet H](sec_ai_h), [T1.4](sec_ai_t1#t14), [T1.5](sec_ai_t1#t15) and the whole of [T1](sec_ai_t1)'s mode set derive from it, and [U1.30](sec_ai_u1#u130) points out that even the text grid of [T1.24](sec_ai_t1#t124) is 1024 active pixels divided by 8. **The document must not carry two panel decisions and present them as one.** If both stand, say which sheets are written against which.
- Q146 — **Blitter maximum burst length, 16 words or 64.** [U1.8](sec_ai_u1#u18) reads half-resolution scanout's fourfold underrun margin as permission to lengthen bursts for page-hit efficiency. [T3.27](sec_ai_t3#t327)'s 23-clock worst case assumes an eight-word in-flight burst that cannot be preempted, and [T3.26](sec_ai_t3#t326) bounds the CPU's read stall by one burst. **A 64-word burst multiplies the non-preemptible term by eight.** The scanout FIFO absorbs it with room to spare; **the PHI2 stall of [D37](sec_ai_q#d37) is the one that has to be recomputed**, because it is CPU-visible latency rather than margin ([Q57](sec_ai_q#q57)).
- Q147 — **Does the target design use USB HID host for the mouse?** If it does, the Phase 0 keyboard-host work of [S11](sec_ai_p1#s11) transfers directly and should be scoped accordingly. If the pointing device is PS/2 or otherwise non-USB, the rig's keyboard stays rig utility and nothing in it survives ([P1.14](sec_ai_p1#p114), [L2](sec_ai_p4#l2)).
- Q148 — [[!blocking]] **How many I/O does the Spartan-6 board actually expose on headers?** [P1.10](sec_ai_p1#p110) counts 52 pins across the CPU bus, VGA, SD and the EC link — 53 before `DBG_CSN` was withdrawn ([D80](sec_ai_q#d80)), and the number the board offers has never been counted. **It blocks the HAT layout.** If it falls short, blocks B and D time-separate across two HAT revisions — which is a decision to take before layout, not during it.
- Q149 — **Target PHI2 for Phase 0.** Proposal: bring up at 1 MHz and raise toward 8 MHz once SDRAM stalling is stable ([S5](sec_ai_p1#s5)). The same caution as [P2.19](sec_ai_p2#p219) applies in reverse — a fault absent at 1 MHz says nothing about 8 ([Q72](sec_ai_q#q72)).
- Q150 — **Does Phase 0 exercise the boot memory load?** The question used to be whether the rig's mailbox command set included `MEM_WRITE`; **that class no longer exists** ([D82](sec_ai_q#d82)), so what is being asked is whether the rig drives `WRITE_BURST` into endpoint `0x02` at all. On the rig the boot ROM is in BRAM, so it is exercisable but not required — and since the target's boot now depends on that exact path, exercising it on a rig where a failure costs nothing is worth more than it was ([S7](sec_ai_p1#s7), [R.25](sec_ai_r#r25)).
- Q151 — [[!blocking]] **Confirm against the iCE40 programming and configuration guide that `SPI_SS_B` sampling at reset exit behaves as [D86](sec_ai_q#d86) assumes, and that parking low is safe on all three devices.** The parking rule is what makes an accidental reset of any FPGA fall into passive slave mode instead of a bus fight with the EC, and **the whole of it rests on one datasheet sentence that has not been read in the original** ([D3.8](sec_ai_d3#d38)). It is schematic capture, and it is minutes of reading against a failure that presents as a dead link with no cause.
- Q152 — **Whether endpoint `0x04` absorbs the CPU → EC direction or a dedicated source endpoint is warranted** — and, behind it, whether six endpoints is enough. The pending bitmap in the `STATUS` byte caps the practical count at six and **growth past it is a status-format revision rather than a transport revision**, which is the cheaper of the two to be wrong about ([D3.11a](sec_ai_d3#d311a), [D3.12](sec_ai_d3#d312)). Two slots are reserved; committing them is a decision, not a discovery.
- Q153 — [[!blocking]] **The achievable `SCK` ceiling for the iCE40 SPI slave with the router's header FSM and CRC generators in the path, and the one crossing of [D3.12b](sec_ai_d3#d312b).** Every frame, latency and boot-load figure in the document is computed at **10 MHz**, while [R.6](sec_ai_r#r6) has long carried **16 MHz initially** from the synchroniser depth alone. **The two cannot both stand and the conservative one is what the budgets use** until it is measured ([R.25](sec_ai_r#r25)'s 1.23 MB/s scales directly with it).
- Q154 — **Whether the Debug Agent is stable enough to be boot-critical by [E1.7](sec_ai_p3#e17), and the fallback if it is not.** [D82](sec_ai_q#d82) put `bios.bin` through the agent's state machine deliberately, so that the debug write path is exercised on every boot. **The abandonment condition is already specified — a write-only sink endpoint at `0x05` using [R.25](sec_ai_r#r25)'s payload format unchanged, one small gateware block and one table row** — and the point of writing it down now is that the decision can then be taken on evidence at E1 rather than negotiated under pressure.
- Q155 — [[!blocking]] **Re-derive the Debug Agent's per-transaction watchdog against worst-case SDRAM latency, now that it fires during boot.** [R.17](sec_ai_r#r17)'s 100 µs was chosen when a timeout was a diagnostic; under [D82](sec_ai_q#d82) a spurious expiry is **a failed boot**. The bound needed is a row activation coinciding with a refresh cycle under the boot load's own access pattern, and **the failure it prevents is an intermittent boot fault, which is the most expensive kind to find later**.
- Q156 — **The cache controller's state during the boot load: bypass, write through, or allocate.** The CPU is in reset so coherence is trivial — **which is exactly why this will be decided by whatever the gateware happens to do unless it is decided on purpose**. It must be defined before the first `WRITE_BURST` is written, and it interacts with [F.11](sec_ai_f#f11) and with [Q29](sec_ai_q#q29)'s arbiter priority question ([R.25](sec_ai_r#r25)).
- Q157 — **Whether to renumber one of the two opcode spaces that both use `0x10` and `0x11`.** In `DBG_CMD` they are cache flush and invalidate; in the endpoint `0x02` payload they are `WRITE_BURST` and `READ_BURST`. **Nothing decodes them together and nothing breaks** — and a reader, a firmware author or a testbench will conflate them at least once. Renumbering either space costs nothing before implementation and is awkward after ([R.25](sec_ai_r#r25)).
- Q158 — **Whether the Colorlight carrier's Block C 8 pins include `DBG_CSN`.** If they do, **Block C becomes 7 and its spare count rises by one** now that the pin is withdrawn ([D80](sec_ai_q#d80)). It is a count against a recorded allocation rather than a design question, and it belongs before the carrier's pin map is frozen ([P2.10](sec_ai_p2#p210)).
- Q159 — [[!blocking]] **Does a physical W65C816S still exist in noVa128?** If not, **PHI2 stretching disappears as the memory-wait mechanism and the whole wait semantics must be redefined** — which touches Helium 2's arbiter, the cache fill, the debug halt and every timing statement inherited from noVa64 ([E.4](sec_ai_e#e4), [F.7](sec_ai_f#f7)). It is the largest unresolved item in the noVa128 material and **nothing else in [sheet NV1](sec_ai_nv1) can be finalised around it**.
- Q160 — **Is `MEMCPY` bit-identical across executors, in write order and in restart behaviour?** The interpreter maps it onto `MVN`/`MVP`, which is bank-confined and segmented per 64 KB; the bytecode core has a flat 24-bit datapath ([VM3.22](sec_ai_vm3#vm322)). **This is the instruction whose implementation differs most between targets and therefore the likeliest place for a silent divergence**, so the conformance suite checks it explicitly rather than by sampling.
- Q161 — **Instruction-cache coherence, in two places and with two different answers.** On the bytecode core, a cache holding guest `.text` must be flushed on the relevant TLB and ASID events when the kernel remaps pages for copy-on-write or paging ([VM3.28](sec_ai_vm3#vm328)). On Argon 2, the same cache in 6502 and 65816 modes meets self-modifying retro code, where the options are snoop, disable, or software coherence and **the recommendation is line snooping** ([NV1.25](sec_ai_nv1#nv125)). Both need a decision before implementation.
- Q162 — **Does floating point get opcodes in NVM32's reserved space, or stay soft float?** Soft float interpreted at 8 MHz costs hundreds of VM instructions per operation, each 60–120 host cycles ([VM4.23](sec_ai_vm4#vm423)). **It blocks the T4 freeze**, because the reserved space cannot be spent afterwards ([D94](sec_ai_q#d94)).
- Q163 — **What is the project's benchmark set, and are [VM4.45](sec_ai_vm4#vm445)'s decision thresholds accepted as written?** The proposal is Dhrystone plus Coremark plus two real noVa64 programs. **Both must be ratified before any measurement is used to justify a change** — setting a threshold after seeing the counter is how a benchmark becomes an argument.
- Q164 — **Does the kernel stay 65816-native, move to NVM32, or split?** Argon 2 makes all three possible, which the coprocessor model did not ([NV1.35](sec_ai_nv1#nv135)). A bytecode kernel is also the precondition for NVM32 standalone mode ([VM3.24](sec_ai_vm3#vm324)), so the two questions are one.
- Q165 — **Licensing: a vbcc carrying an NVM32 backend is a modified version, redistributable only with the author's written consent**, and vasm and vlink carry equivalent terms ([VM4.6](sec_ai_vm4#vm46)). Fine privately, and it must be decided **before the backend is written**, because it can change the tool choice. Two conversations are owed if the target is ever upstreamed: the vbcc author asks to be contacted before a code generator is written, and the vasm manual asks contributors to declare code they did not write themselves, **explicitly naming generative AI**.
- Q166 — **Which of the four encoding candidates are adopted?** Fixed-form memory operands, two-address forms, `WITH`/RP and register windows, decided by the T3 histogram against the thresholds of [VM4.45](sec_ai_vm4#vm445) ([VM1.44](sec_ai_vm1#vm144)). **A candidate that adds architectural state clears a higher bar than one that does not**, because {R0–R15, PC} is what migration and cheap preemption rest on.
- Q167 — **Is a GP small-data register worth one of NVM32's sixteen?** Addressing a global costs 10 bytes today; vlink's base-relative small-data merging brings the common case down to a 4-byte `LDW rd,[gp+off16]` ([VM4.19](sec_ai_vm4#vm419)). **Decide at gate T5 on measurements, not before.**
- Q168 — **The encoding of Helium's capability register and of the system information block, including its version field.** The BIOS owns both, and the gate selection at boot depends on them ([VM2.25](sec_ai_vm2#vm225), [VM2.44](sec_ai_vm2#vm244)). It is the remaining half of what [Q5](sec_ai_q#q5) asked, now that [D91](sec_ai_q#d91) has settled where the block lives and who writes it.
  NOTE: The block gains the **text geometry**, columns and rows, which the console reads instead of assuming ([CN1.4](sec_ai_cn1#cn14)).
- Q169 — [[!blocking]] **`MEMCPY` on `MVN`/`MVP` versus [E.21](sec_ai_e#e21)'s categorical ban on block moves against pageable memory.** The interpreter wants the block move because it is the fastest copy the machine has and is natively restartable with progress in X, Y and C — exactly what [VM1.33](sec_ai_vm1#vm133) requires; **but guest memory is pageable by definition**, and [E.21](sec_ai_e#e21) bans it because a move straddles many pages and its per-byte state sits inside [E.18](sec_ai_e#e18)'s corruption windows. Three ways out, none chosen: a software loop of ordinary loads and stores, several times slower · pinning the pages for the duration, which turns a guest instruction into a kernel call · or **narrowing [E.21](sec_ai_e#e21) to exclude a move whose restart state the VM already guarantees** ([VM2.13](sec_ai_vm2#vm213)).
- Q170 — [[!blocking]] **Are all memory-mapped registers idempotent on read?** A real 65816 performs spurious reads and writes during `INC abs,X`, `ASL` and similar ([E.18](sec_ai_e#e18)); over RAM they are harmless, over a Neon or Helium register with a read side effect they are not ([NV1.26](sec_ai_nv1#nv126)). **It is cheap to guarantee now and expensive after the Neon command port is frozen** ([T1.21](sec_ai_t1#t121), [T1.38](sec_ai_t1#t138)) — the one item in the noVa128 material with a deadline against work already in progress.
- Q171 — **The package and pin budget for three FPGAs with 16-bit inter-FPGA paths.** The Helium↔Neon link already needed a multiplexed 32-signal encoding to fit TQ144 with byte-wide links ([Q12](sec_ai_q#q12)); three devices at 16 bits do not fit that budget, so noVa128 needs either larger packages throughout or serialised links — **and serialising reintroduces exactly the latency the design is most sensitive to** ([NV1.24](sec_ai_nv1#nv124)). Resolve before schematic capture, and note it travels with [D95](sec_ai_q#d95).

- Q172 — [[!blocking]] **`fsops` against `vnode_ops`, six divergences that are one decision.** The host track proposes an opaque directory cursor where [Y1.3](sec_ai_y1#y13) has a 32-bit cookie; `open` and `close` slots where [Y1.10](sec_ai_y1#y110) has none and argues that opening is a VFS act; a name buffer inline in the returned entry where [Y1.12](sec_ai_y1#y112) requires a caller-provided one against a 512-byte kernel stack; 64-bit offsets where the machine has 32; and **no link, symlink or per-file flush slots although its own write gates implement all three**. **They cannot be taken one at a time** — the cursor and the entry buffer are the same question about who owns decoding state — and [V0](sec_ai_y1#v0) freezes the header, so this closes before that gate rather than during it ([Y4.5](sec_ai_y4#y45), [D99](sec_ai_q#d99)).
- Q173 — [[!blocking]] **Explicit accessors or packed overlays, and the two sheets say opposite things.** The host track forbids casting a packed structure over a sector buffer anywhere, and its third reason is about this machine: Calypsi has a 16-bit `int` and accessors port where casts do not ([Y4.7](sec_ai_y4#y47)). [Sheet Y3](sec_ai_y3) specifies overlays with static assertions, and [Y2.23](sec_ai_y2#y223) requires an assertion on every structure size in both builds, which presumes structures. **The whole de-risking claim is that the decoding layer lifts to the target unchanged**, and it does not survive the two being written in different idioms. Free before [FUS-02](sec_ai_y4#fus-02), expensive once three drivers exist.
- Q174 — **htree, closed twice and in opposite directions.** The host track refuses to modify any directory carrying the index flag; [Y3.6](sec_ai_y3#y36) clears the flag on first modification and falls back to a linear scan. **Both are safe and only one can be the prototype**, which is what running [FUS-07](sec_ai_y4#fus-07) before the target write path exists is for. [Q98](sec_ai_q#q98) may dissolve it entirely, since formatting with the index off removes the problem at source ([Y4.21](sec_ai_y4#y421)).
- Q175 — **What [D100](sec_ai_q#d100) costs the track's claim to block nothing.** [FUS-05](sec_ai_y4#fus-05) and [FUS-08](sec_ai_y4#fus-08) now wait on draft 3 tooling and on regenerated conformance and agreement corpora, work [Y2.1](sec_ai_y2#y21) schedules and the source note assumed already done. **At its last four gates the track is no longer free of the machine's calendar**: either the NVFS gates move behind that tooling, or the ext2 write gate runs ahead of them and the strict linearity of [Y4.14](sec_ai_y4#y414) is spent. Travels with [Q87](sec_ai_q#q87).
- Q176 — **What the adapter does with ownership, permissions and the clock at the boundary.** The host attribute structure is POSIX-shaped and the host driver calls the host clock, while [Y1.16](sec_ai_y1#y116) enforces no permissions because there is no user model to enforce them against, and [Y1.17](sec_ai_y1#y117) forbids a driver the clock outright. **The fields are not the problem, the synthesis is**: a slot that invents a plausible value on the host is a slot that invents one on the machine unless somebody says it does not ([Y4.20](sec_ai_y4#y420)).
- Q177 — **The boot partition's MBR type byte.** [D107](sec_ai_q#d107) needs one the BIOS can find by type, and it cannot be `0x7F`, which is NVFS's, nor `0x7A` or `0x7B`, for the reason [D52](sec_ai_q#d52) gives. Pick it before the host tool that writes the card is written (→ [CN1.5](sec_ai_cn1#cn15)).
- Q178 — **`exec`'s signature: spawn semantics, an argument vector, and what a child inherits.** [Sheet J](sec_ai_j)'s table has `exec(path)` with no `argv`, and no `fork`; since `wait(pid)` exists and nothing else creates a process, the console assumes that `exec` creates a process and returns its PID. Open: the `argv` parameter, where it lands in the new address space — the recommendation is above the user stack in bank `$00`, where [N.6](sec_ai_n#n6) already places crt0's arguments — and whether descriptors 0–2 are inherited, which the console assumes. Needed by [CON-04](sec_ai_cn1#con-04).
- Q179 — **The text-mode note Neon's Mode 0 still owes.** [CN1.27](sec_ai_cn1#cn127) lists the seven primitives the console needs. [Sheet T1](sec_ai_t1) covers the display, but the register map for the cursor, the scroll and the clear is not written down, and neither is a **diagnostic read path for the text buffer**, which would let hardware runs compare golden screens instead of checking them by eye ([CN1.34](sec_ai_cn1#cn134)). The geometry is settled by [D44](sec_ai_q#d44) and the emulator's divergence is [EM4.9](sec_ai_em4#em49). Blocks [CON-00](sec_ai_cn1#con-00) on hardware, not in the emulator.
- Q180 — **Helium's CPU-side HID interface.** [CN1.28](sec_ai_cn1#cn128) asks for a queue fed by endpoint `0x03` with a fixed entry format, a pop by explicit write, a count, a sticky overflow flag and an interrupt line. **The interrupt is the part with a deadline**: without it `read()` cannot block, and polling must be gone by [CON-04](sec_ai_cn1#con-04). It belongs to Helium's interrupt controller, which [Q22](sec_ai_q#q22) still leaves unassigned, and the entry format is the half of [Q4](sec_ai_q#q4) that is still open.
- Q181 — [[!blocking]] **[G.7](sec_ai_g#g7)'s PIO FIFO pops on read, against [D92](sec_ai_q#d92) and [M.15](sec_ai_m#m15).** `SD_DATA` is a data port whose read consumes a word — exactly the side effect [D92](sec_ai_q#d92)'s third requirement forbids and [CN1.29](sec_ai_cn1#cn129) asks the SD block not to have. Either the PIO path pops by an explicit write, like the HID queue of [CN1.28](sec_ai_cn1#cn128), or bring-up goes straight to the DMA path and the FIFO is dropped. Decide before the register map is frozen ([Q22](sec_ai_q#q22)).
- Q182 — **The character encoding shared by the glyph store, the keymap and filenames.** The recommendation is ISO-8859-15: one byte per character, Spanish covered and `€` included, with UTF-8 names from ext2 hosts shown as raw bytes. **It needs all 256 glyphs, which rules out [Q45](sec_ai_q#q45)'s first relief**, a 128-glyph font, so the two close together. Needed by [CON-01](sec_ai_cn1#con-01).
- Q183 — **Reconcile [sheet J](sec_ai_j)'s v1 dispatch table with [Y1.20](sec_ai_y1#y120).** The table lacks `chdir`, `getcwd`, `rmdir`, `dup`, `dup2`, `sync`, `opendir` and `closedir`, all of which the VFS maps and the console needs between [CON-02](sec_ai_cn1#con-02) and [CON-04](sec_ai_cn1#con-04) ([CN1.26](sec_ai_cn1#cn126)). They are general primitives rather than one subsystem's verbs, so [D23](sec_ai_q#d23)'s test does not stand in their way; what is open is adding them and numbering them with the rest of the `SYS_*` constants. Travels with [Q178](sec_ai_q#q178).
- Q190 — **Where the emulator runs under the debugger.** [EM8.4](sec_ai_em8#em84) leaves two shapes: the wasm module of [sheet EM5](sec_ai_em5) loaded into VS Code's extension host, or the native build as a child process speaking the Debug Agent's command set over a pipe. The recommendation is the pipe, because it is the boundary the hardware backend will have; speed does not decide it, since the wasm build alone already runs at nearly three times real time ([EM5.13](sec_ai_em5#em513)). The wasm path stays for a machine with no native toolchain. Decide before [DBG-01](sec_ai_em8#dbg-01).
- Q191 — **The host transport of the Debug Agent's command set.** The console grammar of [sheet R](sec_ai_r) is written for a person at a terminal; a program driving the agent over the EC's console UART ([R.19](sec_ai_r#r19)) needs a framed, machine-read form of the same commands. This is the question [R.24](sec_ai_r#r24) defers for a GDB stub, arriving from another client, and its reason for deferring holds here too. **The emulator's pipe of [Q190](sec_ai_q#q190) should be that framing from the start**: it moves with the command set in the same revision, as [EM3.3](sec_ai_em3#em33) already requires, so choosing the hardware transport later adopts a format in use rather than inventing a second one. Blocks [DBG-05](sec_ai_em8#dbg-05) only.
- Q192 — **C source-level debugging from Calypsi's output.** Calypsi's objects are ELF with DWARF debug information ([EM8.9](sec_ai_em8#em89)). Open: whether the output the loader consumes keeps it, or an ELF has to be kept beside the image the way a `.dbg` sits beside a ca65 one; how 24-bit addresses and the far pointers of [O.2](sec_ai_o#o2) are encoded in it; and whether an off-the-shelf DWARF reader accepts the 65816 machine type. Needed before the kernel's C is debugged at source level, not before [DBG-00](sec_ai_em8#dbg-00).
