dmolinagarcia/nova64/docs/docsV3/content/sec_ai_z3.md

# Appendix — glossary
> every acronym and term · grouped by domain

The document's terminology in one place. Every acronym is also expanded on first use where it appears, so this sheet is deliberately redundant — it exists to be jumped into, not read through. It is grouped by domain, and within each group runs roughly in the order the concepts appear. The figures have a sheet of their own ([Z2](sec_ai_z2)).

## Virtual memory and the MMU
  NOTE: → [sheet K](sec_ai_k) · [sheet L](sec_ai_l)

| Term | Meaning |
|---|---|
| Virtual memory | A layer of indirection between the addresses the CPU generates and those that reach the RAM. Every process here sees a clean, contiguous 16 MB of it, and the indirection is Helium's: the 65816 has no MMU of its own. |
| Virtual address | The address the CPU emits — what the program "believes". 24 bits here. |
| Physical address | The address that reaches the SRAM/SDRAM chips. 27 bits here. 27 bits here — a 128 MB ceiling, with the SDRAM frames at the bottom of that space and the pinned SRAM frames at the top ([L.6](sec_ai_l#l6)). |
| Page | A fixed-size block of the virtual space. 2 KB. 8,192 of them per process, and the size is deliberately decoupled from the 256 B granularity a fill actually moves. |
| Frame | A block of the same size in physical memory. To translate is to pair a page with a frame. 32,768 of them across the SDRAM, tracked by a bitmap in the kernel. |
| VPN | Virtual Page Number — high bits of the virtual address; identifies the page. 13 bits. |
| Offset | Low bits; the byte within the page. Never translated. 11 bits. |
| MMU | Memory Management Unit — the hardware that translates. Not in the CPU here: Helium implements it. The TLB, the hardware walker, the permission checks and the `ABORTB` that reports a failure are all Helium's. |
| Page table | An array indexed by VPN holding the PTEs. One per process, 32 KB. Flat, not multi-level: 8,192 entries × 32 bits, held in the pinned SRAM region so the walker reads it directly. |
| PTE | Page Table Entry — one entry of that table. 32 bits: frame number plus flags. 16 bits of frame number plus the flags below — which is what puts the physical ceiling at 128 MB. |
| PTE flags | `P` present in RAM · `W` writable · `X` executable · `U` reachable from user mode · `D` dirty (modified since load) · `A` accessed recently · `NC` non-cacheable · `PIN` non-evictable · `SW` free for the kernel's own use. |
| TLB | Translation Lookaside Buffer — cache of VPN→frame translations inside the MMU. Avoids re-reading the table on every access. |
| TLB hit / miss | Success or failure in that cache. A miss costs one table walk; it is not an error. |
| TLB reach | Entries × page size — the working set the TLB can cover before it starts thrashing. 64 KB here with 32 entries; the main thing a larger page buys. |
| Page walk / walker | The traversal of the page table that resolves a miss. Hardware here (≈100 ns, four 8-bit SRAM accesses); a software exception in other architectures. |
| ASID | Address Space IDentifier — tag marking which process each TLB entry belongs to. Without it the whole TLB would be flushed on every context switch. |
| Page fault | Exception raised on access to a page with `P=0`. Recoverable. Delivered as an ABORT; the handler grows a heap or stack, resolves a copy-on-write, or kills the process ([L.14](sec_ai_l#l14)). |
| Demand paging | Loading pages only when touched rather than all up front. Deferred to post-v1. |
| Eager loading | Mapping and filling every segment at `exec` time. What v1 does, in place of demand paging. |
| Swapping | Evicting rarely used pages to storage in order to free frames. Order matters: flush the frame's dirty sub-blocks to SDRAM before writing it to the card ([L.16](sec_ai_l#l16)). |
| Pinning | Marking a page as non-evictable. Required for the kernel, the interrupt vectors and the bank `$00` stack. It is a physical address range rather than a cache attribute, so an access there skips tag lookup entirely and completes at fixed latency. |
| Memory protection | Preventing a process from reading or writing outside its own space. Achieved through the PTE flags, not through translation itself. |
| Cache line | The tagged unit of Helium's cache — 2 KB, one tag per line, but filled and written back in 256 B sub-blocks. |
| Sub-block | The 256 B unit a fill actually moves, with its own valid and dirty bits. Keeps a miss at ~6 µs instead of ~41 µs and bounds interrupt latency. |
| Set associative | Cache organization where a given address may sit in any of N positions ("ways") within one set. Four ways here; direct mapping would put 32,768 physical lines in competition for 384 slots. |
| Tag | The bits stored alongside a cache line saying which physical line it currently holds. Kept in EBR, ~1.5 KB, beside the TLB. |
| Dirty victim | The line a fill has to evict when it has been written to — it must go back to SDRAM first, which is why a miss can cost double. |
| Write-back | Cache policy where writes stay in the cache and reach memory only on eviction. Implied by the dirty bits. It is also why a frame is flushed before eviction and invalidated before a DMA engine fills it. |
| Backing store | The memory a cache is a cache *of*. Here the SDRAM, which the PTEs always name. |
| Flush vs invalidate | The two ways to empty a cache line, and they are not interchangeable. **Flush** writes dirty contents back and then marks the line clean — used before the CPU's data has to be visible to someone else. **Invalidate** drops the line without writing anything, dirty or not — used when the contents are about to be overwritten by someone else. Getting them backwards loses data in one direction and merely wastes a burst in the other ([M.12](sec_ai_m#m12), [G.9](sec_ai_g#g9)). |
| Copy-on-write | Sharing a page read-only between processes and duplicating it only when one writes. An ABORT case ([L.4](sec_ai_l#l4)). The downgrade to read-only is one `TLB_INVAL_PAGE`, not a full flush. |
| Static core | A CPU whose state survives an arbitrarily slow or stopped clock. The W65C816S is one, which is what makes the PHI2 stall legal. |
| Clock gating | Stopping and restarting PHI2 in gateware. Must be glitch-free, and the first pulse on resume must meet the minimum high width. The same gate serves the cache-miss stall, Neon's busy stall and the machine's low-power state. |
| Trampoline | The short privileged stubs in bank `$00` that receive every vector — the CPU forces PBR=0 on entry — and `JSL` straight into the real kernel in `$FD` (→ [L.11](sec_ai_l#l11)). |
| ASID recycling | Reassigning a used ASID to a new process. Legal only after flushing that ASID's TLB entries; skipping the flush leaks the old address space into the new one, silently (→ [M.8](sec_ai_m#m8)). |
| Address as opcode | Command convention where each operation has its own address and the value written is its argument, not a command code (→ [M.2](sec_ai_m#m2)). |
| WDM | Opcode `$42`, reserved by WDC and executed as a two-byte, two-cycle no-op. Considered as a command channel and rejected; it stays a no-op, and a softcore must implement it as one. |
| Memory barrier | An instruction forcing memory ordering. Not needed here and not provided: the 65816 has no prefetch queue and no store buffer, so every bus cycle is already in program order. |
| Watchdog | Timer that resumes PHI2 and raises NMI or ABORT if a fill overruns — without it a hung fill freezes the machine with no clock and no diagnostic path. It covers Neon's read stall too, which is what makes an unfitted Neon a fault report rather than a dead board ([F.11](sec_ai_f#f11)). |
| Refresh | The periodic recharge SDRAM needs to keep its contents. Must be interleaved into the fill state machine, not deferred until it finishes. |

## CPU, bus and gateware
  NOTE: → [sheet B](sec_ai_b) · [sheet F](sec_ai_f)

| Term | Meaning |
|---|---|
| Bank | A 64 KB slice of the 65816's 24-bit space, selected by DBR/PBR. The virtual bank map is in [L.10](sec_ai_l#l10). The map is fixed: `$00` stack, direct page and vectors · `$01` VM interpreter · `$02`–`$EF` user · `$F0`–`$FD` kernel, growing down from `$FD` · `$FE` VRAM window · `$FF` privileged I/O. |
| DBR · PBR · DP | Data Bank, Program Bank and Direct Page registers — the 65816 state that decides which bank an access lands in. |
| Native mode | The 65816's 16-bit, 24-bit-address mode, entered with `CLC/XCE`. The opposite is 6502 emulation mode. The M and X flags then pick 8- or 16-bit accumulator and index registers at run time. |
| PHI2 | The CPU's master clock, generated by Helium. Target 8 MHz. Target 8 MHz at 3.3V. Helium may hold it in either state indefinitely — the core is fully static — which is what a cache-miss stall does. |
| BE | Bus Enable — the pin that makes the physical CPU tristate its address, data and RWB drivers and release the bus. Driven by Helium, which uses it far more often than Argon would (→ [R.3](sec_ai_r#r3)). |
| RESB | The 65816's active-low reset. Released by the RP2354B as the last step before the CPU runs. Pulled down when no bitstream is loaded, so a blank board holds the CPU in reset instead of running it into an undriven bus. |
| ABORTB | W65C816S pin that cancels the instruction in progress without side effects. The system's fault mechanism. Asserted by the MMU on a missing page or a permission violation, and the instruction restarts once the kernel has fixed the mapping. |
| VPA / VDA | Pins indicating whether the cycle is an instruction fetch or a data access. They make checking the `X` flag possible. |
| RDY | Bidirectional, open-drain: Helium pulls it low to freeze the CPU while it takes the shared nets ([F.4](sec_ai_f#f4)), and the CPU pulls it low itself during `WAI`. **Cache-miss stalls do not use it** — [D16](sec_ai_q#d16) moved those to PHI2 gating, since some W65C816S revisions ignore RDY during write cycles. |
| Northbridge | Borrowed PC term for the chip sitting between CPU and memory. Here it is Helium: MMU, cache, arbiter, timer and I/O. |
| Gateware | The logic loaded into an FPGA — the FPGA equivalent of firmware. Written in HDL, not compiled to instructions. |
| Softcore | A CPU implemented as gateware rather than as a chip. The footprint on Argon ships unpopulated, and what a core owes the board is a pin list as much as an instruction set ([E.13](sec_ai_e#e13)). **Which core it would be has changed**: [D88](sec_ai_q#d88) makes it bytecode-native rather than a 65816 (→ [sheet VM3](sec_ai_vm3), [sheet E](sec_ai_e)). |
| Fmax | The highest clock a placed-and-routed design will meet timing at. A property of the design *on a given part* — quoting one across FPGA families is meaningless. |
| CPI | Cycles Per Instruction. The 65816 spends 2–7, many wasted on bus protocol. Lowering it buys throughput without touching the critical path, which is why it beats chasing clock. |
| Microcode | The internal table that sequences each instruction. On a soft core it sits in block RAM, and registering its output is the standard first move against the critical path. |
| Cycle-exact | A core reproducing the original's timing cycle for cycle. Needed to emulate a specific machine; unnecessary here, where only programmer-visible behaviour must match (→ [E.6](sec_ai_e#e6)). |
| ILP | Instruction-Level Parallelism — independent work a core can overlap. An accumulator architecture offers little, which bounds what any 65816 core can gain from pipelining. |
| Accumulator architecture | A design where most operations route through one register. Compact to encode, heavy on memory traffic, and inherently serial. |
| Bus arbiter | The logic deciding who drives the shared bus in each cycle: CPU, cache fill, video, or refresh. The CPU is stalled rather than queued: Helium takes the shared nets with `BE` and hands the clock back afterwards. |
| PIC | Programmable Interrupt Controller — collects device IRQs, applies priorities, and raises IRQ/NMI to the CPU. Neon's three sources arrive on one wire and are demultiplexed by the kernel reading `IRQ_STATUS`. |
| EBR | Embedded Block RAM — 32 dual-port blocks of 512 B inside each iCE40, 16 KB in total. On Helium its scarcity is why only the TLB and the cache tags fit on-chip while the page table lives in external SRAM; on Neon it is the whole of Mode 0, and it is **fully allocated with zero margin** ([T1.12](sec_ai_t1#t112)). The prototype board's ECP5 has ~243 KB of it, roughly fifteen times as much, which is the single most misleading number on that platform ([P2.04](sec_ai_p2#p204)). |
| Bitstream initialisation | Giving a block RAM its contents from the compiled bitstream rather than loading them at run time. What makes Neon's font and text buffer valid before any software exists — the single most useful property of the design ([D27](sec_ai_q#d27)). |
| HDL | Hardware Description Language — Verilog or VHDL. noVa64 gateware is Verilog-2005 ([D101](sec_ai_q#d101)). |
| Stub | In layout, a track branching off a bus. Long stubs ruin signal integrity at ~100 MHz, hence the short comb of [F.13](sec_ai_f#f13). |
| Expansion slot | The parallel connector of [sheet X](sec_ai_x): the machine's own bus, buffered, with a card as a third tenant of the contract Helium already has with Neon. Unpopulated in the first build. |
| `/EXP_SEL` · `/EXP_BSY` · `/EXP_IRQ` | The slot's three nets — select, stall, interrupt — mirroring `NEON_BUS_SEL`/`BSY`/`IRQ`, with `/EXP_BSY` idling **not busy** because an empty slot must not stall the machine ([X.11](sec_ai_x#x11)). |
| Slot aperture | The 1 MB per slot the MMU can map into a process, carved out of the frame numbers [F.10](sec_ai_f#f10) leaves unpopulated and addressed on A11–A19, which are idle while the SRAM's `/CE` is ([X.8](sec_ai_x#x8)). Always non-cacheable. |
| Register window vs aperture | The two ways a card is reachable, and the split is [T1.21](sec_ai_t1#t121)'s: **control** in bank `$FF`, unmappable to user space by construction; **bulk** through the aperture, mappable with permissions in front of it. |
| Geographic addressing | Telling a card which slot it is in with connector pins strapped differently in each position, so the same board works in either one with no jumper ([X.14](sec_ai_x#x14)). |
| Bus master | A device that drives the address bus instead of the CPU. Here: Helium, and nothing else — a card cannot honour the cache-coherence discipline of [M.12](sec_ai_m#m12), so [D48](sec_ai_q#d48) refuses it the bus rather than trusting it ([X.16](sec_ai_x#x16)). |
| `I2C-EXP` | The third I2C bus, Helium's own and the only one where Helium is master. The slow expansion tier: devices mirrored into I/O windows rather than reached transactionally ([X.22](sec_ai_x#x22)). |
| Window (slow bus) | A copy of a device's registers in Helium's block RAM, refreshed by a sequencer and read by the CPU at bus speed. A **mirror, not a proxy** — a byte over I2C is ~90 µs and nothing may stall PHI2 for that ([X.23](sec_ai_x#x23)). |

## Board, power and configuration
  NOTE: → [sheet C](sec_ai_c) · [sheet D1](sec_ai_d1) · [sheet S](sec_ai_s)

| Term | Meaning |
|---|---|
| EC | Embedded Controller — the always-on microcontroller handling power, boot and housekeeping. Here, the RP2354B in QFN-80. It stays off the shared bus entirely, and its in-package 2 MB flash is the board's only mandatory non-volatile storage ([D1.8](sec_ai_d1#d18)). |
| Rail | A supply voltage distributed across the board (3V3_AON, 3V3_MAIN, 1V2, VPP…). "Sequencing" is the order they come up in. Every logic rail here is 3.3V, which is what keeps level shifters off the board. |
| SYS | The node after the charger, fed by USB or battery indifferently. Everything hangs off it rather than off the battery. |
| Power-path | Charger topology that powers the system and charges the cell at once, so the machine runs on USB with a flat or absent battery. |
| 1S | One lithium cell in series — a nominal ~3.7V pack. Two 1S cells in *parallel* are still 1S: more capacity, same voltage, no balancing. |
| Fuel gauge | Chip that estimates remaining charge from voltage and current history. Here the MAX17048, read by the EC over I2C. Distinct from an ADC, which reports a voltage and models nothing. |
| Buck-boost | Converter holding its output steady whether the input is above or below it — needed because a cell crosses 3.3V as it drains. |
| Boost | Converter that only steps voltage up. Used for the backlight and the 5V host VBUS. |
| LDO | Low-DropOut regulator — a linear regulator, which wastes the voltage it drops as heat. The 1.2V rail used to be one and is now a buck ([D20](sec_ai_q#d20)). |
| Always-on · AON | The domain powered whenever SYS exists: the EC, its flash, the PD sink, the charger/gauge bus and the power button. Nothing else belongs there. |
| Switched domain | Everything whose rail the EC can turn off — the FPGAs, the CPU, the memories, the panel, the touch bus. Off by default at EC reset. |
| Iq | Quiescent current — what a converter draws on its own, at no load. Decisive for an always-on rail, irrelevant for a switched one. |
| PG · Power Good | An open-drain output asserting that a converter has reached regulation. Used here as the sequencing interlock: the EC waits on it before raising the next rail. |
| PD · Power Delivery | The USB-C protocol by which a sink asks for more than the default 5V, negotiated over the CC conductors. Here 9V, requested by a resistor. |
| OTG | A charger mode in which the device sources 5V onto its own VBUS. Present on the BQ25896 and deliberately unused ([D21](sec_ai_q#d21)). |
| Ship mode | A charger state disconnecting the battery from SYS entirely, leaving only leakage. The machine's deepest off state; the button's `QON` pin wakes it. |
| QON | The BQ25896 pin that resets the battery FET from hardware, with no firmware involved. The floor under every other way of turning the machine off. |
| Ordered shutdown | The graceful path: the kernel flushes and confirms before any rail drops. Its opposite is *forced*, where the EC stops waiting for an answer. |
| Watchdog | Here, the EC's 10-second bound on how long a kernel may take to acknowledge a shutdown request. Without one, a hung kernel hides itself as a machine that will not turn off. |
| Staging · live · shadow | The three copies of the telemetry bank. The EC dribbles bytes into staging, one commit publishes them to live, one latch snapshots live into shadow — so an 8-bit CPU can read a 16-bit value without it changing underneath ([S.16](sec_ai_s#s16)). |
| Tearing | Reading a multi-byte value while it is being updated, and getting halves from two different samples. The reason for the snapshot mechanism above. |
| SSPI | Slave SPI — the iCE40 configuration mode in which an external master (the RP2354B) clocks the bitstream in. **The only usable mode on this board**: iCE40 LP/HX has no JTAG, and NVCM is one-time-programmable ([D61](sec_ai_q#d61), [D62](sec_ai_q#d62)). |
| NVCM | Non-Volatile Configuration Memory — the iCE40's on-die one-time-programmable configuration store. **Fuses, not flash**: a part programmed with it carries that bitstream permanently. Rejected for a design that will iterate ([D62](sec_ai_q#d62)). |
| The link | The one SPI channel between the EC and Helium, behind `LINK_CSN` — **the whole of the data plane between the two** ([sheet D3](sec_ai_d3)). Every block inside Helium that the EC talks to is an endpoint on it, addressed by a header byte rather than by its own chip select ([D80](sec_ai_q#d80)). |
| Mailbox | What the link used to be called when it was only HID and system traffic. **It is now two endpoints on the link — `0x03` and `0x04` — at the same level as the Debug Agent, not the link itself** ([D3.9](sec_ai_d3#d39)). |
| `LINK_CSN` | The link's chip select, formerly `MBX_CSN`. The rename is the visible face of the merge: `DBG_CSN` is withdrawn and one select serves every endpoint ([D3.9a](sec_ai_d3#d39a)). |
| Endpoint | A destination inside Helium named by the first byte of a link frame. Each has a class — sink, source or duplex — a commit discipline, and **its own inbound queue, which is what keeps a full queue from blocking anyone else** ([D3.12](sec_ai_d3#d312), [D83](sec_ai_q#d83)). |
| Router | The block behind the SPI front end that reads the header and dispatches the frame to an endpoint. **It dispatches at header completion into a per-endpoint sink rather than buffering the payload centrally**, and it sits in a reset domain no endpoint can assert ([D3.12a](sec_ai_d3#d312a), [D85](sec_ai_q#d85)). |
| Frame | One assertion of `LINK_CSN`: three header bytes each way, payload, then a frame CRC — `4 + LEN` bytes, 259 at most. **The maximum is a latency bound, not a limitation**: it caps the delay one endpoint can impose on another at about 207 µs ([D3.11](sec_ai_d3#d311), [D84](sec_ai_q#d84)). |
| `HCRC` / `FCRC` | The link's two CRC-8s. **`HCRC` protects the routing decision**, which is the catastrophic failure — a corrupted endpoint byte turns a keystroke into a halt or a memory write. **`FCRC` covers the whole frame and decides whether it is committed** ([D3.11b](sec_ai_d3#d311b)). |
| `EPSTAT` | Inbound free space, in bytes, for the endpoint a frame is addressed to — the descendant of the mailbox's four-bit `IN_SPACE`. It is on the wire **before the EC sends any payload**, so a frame to a full endpoint can be abandoned for three bytes rather than rejected after 259. **It may under-report and must never over-report** ([D3.11a](sec_ai_d3#d311a)). |
| Buffered / streaming commit | Whether an endpoint stages a frame and commits it on `ACK`, or commits as bytes arrive. **Streaming is permitted only where retransmitting a rejected frame verbatim is harmless**, which is why [R.25](sec_ai_r#r25)'s bulk write carries an absolute address in every frame ([D3.11c](sec_ai_d3#d311c)). |
| `WRITE_BURST` | The Debug Agent's bulk memory write — opcode, 24-bit absolute address, up to 251 data bytes. **It is how `bios.bin` reaches SRAM**, which makes the debug write path boot-critical and exercised on every power-up ([R.25](sec_ai_r#r25), [D82](sec_ai_q#d82)). |
| INV-1 | The invariant that the Debug Agent's request port has exactly one source and nothing reachable from the 65816 address space can drive it. **A connectivity property, verified structurally** — REV B credited it to a chip select, which never delivered it ([R.26](sec_ai_r#r26), [D81](sec_ai_q#d81)). |
| Head-of-line blocking | A queue in which one stalled item holds up everything behind it. **The failure the per-endpoint sinks exist to prevent**: a CPU that stops draining keystrokes must not stall the debug traffic sent to find out why ([D3.12a](sec_ai_d3#d312a)). |
| XIP | Execute In Place — running code directly out of flash rather than from RAM. Why the EC goes deaf for 30–50 ms while erasing a sector: it cannot execute flash-resident code, interrupt handlers included, while the erase is in progress ([D1.25](sec_ai_d1#d125)). |
| Bitstream | The compiled gateware file loaded into an FPGA at every power-up. iCE40s are SRAM-based: they forget on power-off. |
| CRESET_B / CDONE | The iCE40's configuration handshake: held low to start loading, raised by the FPGA when configuration succeeded. |
| `CFG_SS` parking | Holding each configuration select **low** for the whole session once its `CDONE` has risen. The iCE40 samples that line at reset exit to choose slave or master configuration mode, so a line idling high brings the part up **driving `SCK` against the EC** after any accidental reset ([D3.8](sec_ai_d3#d38), [D86](sec_ai_q#d86)). |
| Bring-up | First powering of a new board, block by block, verifying each before enabling the next. Each stage of the build sheets [P1](sec_ai_p1)–[P4](sec_ai_p4) closes on an explicit `TEST ▸`, not on a judgement. |
| Free-run | Diagnostic where the CPU is fed a constant NOP so it just counts through addresses — proves clock, reset and address bus without any memory. |
| Handoff | Transfer of a shared resource between two owners. **The design no longer contains one**: the microSD handoff was this document's only example and [D60](sec_ai_q#d60) removed it, leaving every peripheral with a single permanent owner ([H.1](sec_ai_h#h1)). |
| TQFP · PLCC · TSOP · BGA | Chip packages. The first three have accessible leads and can be hand-soldered; BGA hides its balls underneath and cannot, which is why it is excluded ([D01](sec_ai_q#d01)). |

## Video, audio and peripherals
  NOTE: → [sheet H](sec_ai_h) · [sheet T1](sec_ai_t1) · [sheet T3](sec_ai_t3) · [sheet W](sec_ai_w)

| Term | Meaning |
|---|---|
| Chip RAM | Amiga term reused here: Neon's own 64 MB SDRAM — framebuffers, atlases, level buffers, command lists and audio DMA — outside the CPU hierarchy and reached through the `$FE` window. |
| Framebuffer | The region of memory holding the pixels currently on screen. Exposed to processes as `/dev/fb`. It lives in Neon's SDRAM rather than in system memory: the CPU reaches it through the `$FE` aperture and never has to read it back. |
| VRAM window | The 64 KB opening in bank `$FE` through which the CPU reaches video memory, gated by the MMU's NEON_BUS_SEL. In graphics modes its low 32 KB slides over SDRAM by `VRAM_PAGE`. |
| NEON_BUS_SEL | Helium → Neon: "this cycle is validated for you." Qualifies **both** of Neon's windows — `$FE` after translation and the permission check, `$FF:8000`–`$FF:80FF` after the bank decode and the privilege check ([B.6](sec_ai_b#b6)). |
| NEON_BUS_BSY | Neon → Helium: "I cannot serve this cycle yet." **Busy by default**, so an absent or unconfigured Neon stalls the machine into a watchdog report rather than onto an undriven bus. Its meaningful edge is the deassertion, which means the data is ready ([T1.18](sec_ai_t1#t118)). |
| Bus-busy stall | How the CPU reads VRAM: Helium decodes the read, holds PHI2 **low** unconditionally, and raises it when Neon clears busy. Stall first, ask afterwards — which removes the race a wait line asserted against the rising edge would have had ([D37](sec_ai_q#d37)). |
| Aperture | The same opening, named from Neon's side. **Data only** — Neon's control registers are not in it but at `$FF:8000`, because `$FE` is user-mappable and `$FF` is not ([D36](sec_ai_q#d36)). |
| Px-doubling | Drawing at a lower resolution and emitting each pixel more than once in both axes to fill 1024×600. Not a policy here but a mode: **Mode 2b** at 2×2, and Mode 2a at 3×3 ([D35](sec_ai_q#d35)). |
| RGB-TTL | Parallel video interface: one wire per colour bit plus sync and clock. No bridge chip needed, at the cost of many pins. Driven here at 18 bpp — RGB666. |
| VSYNC | The pulse marking the end of a frame. Raised as an IRQ so the GUI can redraw without tearing. One of the three sources aggregated onto `NEON_IRQ`. |
| Cell · glyph | One character position — a glyph code plus an attribute byte · the pixel pattern for one code, held in the font. 8 × 16 px here, the standard VGA text cell. |
| Text buffer | The 4096 cells of Mode 0, 8 KB in Neon's block RAM, initialised from the bitstream so the screen is correct at power-on with no software involved. |
| Ring buffer | A buffer addressed modulo its size, so advancing a pointer rotates the visible contents without moving data. `TEXT_START` scrolls the console this way — 256 bytes written instead of 8,192 moved. |
| Blitter | Block image transferrer — hardware that fills, copies and combines rectangular memory regions with no CPU involvement. The centre of Neon's graphics half. |
| Channel | One of the blitter's four memory ports under the model of [sheet T3](sec_ai_t3) — A, B, C read, D writes. Each carries a pointer, a signed modulo and an enable; a disabled read channel supplies a constant and costs no bandwidth. |
| Minterm · logic function | One row of the truth table combining channels A, B and C. Three inputs give eight rows, so the whole function is one byte — the `LF` — selecting any of **256 operations**. `$0C` copies, `$CA` cookie-cuts, `$3C` is XOR. |
| Cookie-cut | Compositing a masked sprite over a background in one pass: mask on A, pixels on B, destination read back on C, `LF = $CA`. Needs a mask surface in memory, which a colour key does not. |
| Modulo | The signed value added to a channel's pointer at the end of every line — the difference between a bitmap's stride and the width being moved. **It is what makes a blit two-dimensional**, and it expresses clipping with no extra hardware. |
| Surface | Any rectangular pixel buffer in Neon's SDRAM: framebuffer, window backing store, font atlas, icon sheet. |
| Backing store | A surface holding one window's complete contents, **including the parts currently hidden behind other windows** — exactly what a flat framebuffer does not keep ([Q60](sec_ai_q#q60)). |
| Compositor | The kernel code that assembles the visible framebuffer from the backing stores, driving the blitter. Distinct from the window manager, which decides what should be where. Which model it runs is still open: repaint every window intersecting the damage, or recompose from backing stores ([Q60](sec_ai_q#q60)). |
| Descending mode | Blitting with the pointers decrementing rather than incrementing. Required whenever source and destination overlap and the move is down-and-right — a window drag is the case. |
| Damage · dirty rectangle | A region of the screen whose composited content is no longer valid and must be rebuilt. Under [T3.31](sec_ai_t3#t331) a bug here costs performance, not corruption, because full recomposition stays correct. |
| Cookie-cut vs colour key | The two ways to make a sprite non-rectangular. A key designates one palette index transparent and needs no extra memory; a mask is a second bitmap and needs generating and keeping in step. The blitter model decides which is available ([Q58](sec_ai_q#q58)). |
| Colour key | A palette index designated transparent; pixels of that value are not written during a copy. What makes a sprite a sprite here, with no sprite engine. |
| Barrel shifter | Logic shifting a word by any amount in one cycle. Required to place a 1-bpp image at an arbitrary horizontal position, which is the expensive part of Mode 1 and not optional. |
| Stride | The byte distance from the start of one image row to the next. Independent per source and destination, which is what lets one copy window a viewport out of a much wider buffer. |
| Command list | A sequence of drawing commands in SDRAM, executed autonomously by Neon. The ANTIC display list and the Amiga Copper, generalised to include the blitter. |
| Display list patching | Writing into a list while Neon executes it — the intended usage pattern, not an abuse. Moving an object is one 32-bit store to one word ([T1.41](sec_ai_t1#t141)). |
| Page flip | Displaying one framebuffer while drawing into another, then exchanging them. `SWAP_BUFFERS`, applied at vblank so a half-drawn frame is never shown. |
| Damage model | Dirty rectangles, z-order traversal and repaint from application state. Unavoidable with a flat framebuffer, because moving a window does not restore what was under it — the pixels were overwritten and are gone. |
| Save-under | Copying a region about to be occluded and restoring it afterwards. Works here despite the CPU not needing to read VRAM, because the *blitter* moves it and the pixels never leave VRAM. |
| Service port | Neon's four configuration SPI pins, reused after `CDONE` as a control channel from the EC. The reason boot progress appears on screen before a CPU exists. |
| Clock enable | A signal gating a register's update without gating its clock. Used to derive Neon's 51.5625 MHz pixel rate inside one 103.125 MHz domain, so there is no second clock domain to cross. |
| Row activation | The delay when SDRAM must open a new row before its data is reachable, ~60 ns. Why glyph lookup stays in block RAM, and why an aperture read has to stall the CPU. |
| SDRAM bank | One of four independent arrays inside the device; accesses to different banks interleave with no row-activation penalty. A layout convention for copies, not something hardware enforces ([Q50](sec_ai_q#q50)). |
| FPC | Flexible Printed Circuit — the flat ribbon connecting the panel. "FPC-50" is its 50-contact connector. |
| eDP | Embedded DisplayPort — serial panel interface. Rejected for v1 as it needs a bridge chip ([D05](sec_ai_q#d05)), and **closed outright** by [D70](sec_ai_q#d70): the bridge category is BGA-only and its one hand-solderable member has no distribution. |
| LVDS | Low-Voltage Differential Signalling — an electrical technique, ~350 mV about a 1.2 V common mode into a 100 Ω-terminated pair. Not a protocol by itself ([U1.4](sec_ai_u1#u14)). |
| FPD-Link · OpenLDI | The protocol layered on LVDS for panels: 7:1 serialization of parallel RGB onto three or four data pairs plus a clock pair. **The clock pair carries the pixel clock, not the bit clock.** OpenLDI is the same scheme under the other name. |
| Serializer | The part turning parallel RGB into LVDS pairs — here two SN75LVDS83B in TSSOP, fed from one shared bus so a dual-channel panel gets two identical in-phase streams ([U1.16](sec_ai_u1#u116), [U1.19](sec_ai_u1#u119)). |
| VESA · JEIDA mapping | The two incompatible schemes for distributing a component's bits across the seven-bit lanes. Choosing wrong gives **a tinted, posterised image rather than a black screen**, which is why it is a datasheet item and not a bring-up guess ([U1.27](sec_ai_u1#u127)). |
| Even/odd split | How a dual-channel panel divides pixels between its two channels. Interleaved by pixel is standard and is what lets both channels share one bus under horizontal duplication; **split by screen half, the technique fails and the panel is unusable** ([U1.17](sec_ai_u1#u117)). |
| Half resolution | Rendering the framebuffer at half the panel's pixel count in both axes and duplicating on output. The saving is **fourfold**, because vertical duplication fetches each line once and displays it twice ([U1.6](sec_ai_u1#u16)). |
| CLUT | Colour Lookup Table — the 256 entries a framebuffer byte indexes into. Held in two banks that switch atomically at vblank, stored 24-bit and truncated at the pins ([sheet T2](sec_ai_t2)). |
| Palette offset | An 8-bit value added to every framebuffer index before lookup, so a whole sub-palette changes in one register write instead of sixteen ([T2.9](sec_ai_t2#t29)). |
| R-2R | A resistor-ladder DAC — the cheapest way to get analogue VGA levels out of FPGA pins. Bring-up only on the target board; **the whole video output on the prototype**, at 6 bits per channel into 1 % resistors ([P2.08](sec_ai_p2#p208)). |
| I2S | Serial audio bus between the FPGA and the DAC — `BCK` the bit clock, `LRCK` the frame clock, `DIN` the data. Unrelated to I2C despite the name. |
| fs · 32fs | The sample rate · a bit clock of 32 `BCK` per stereo frame, which is exactly two 16-bit slots with no padding. **The frame length decides the divider's granularity**, which is why this machine uses 32fs and not the more common 64fs ([W.6](sec_ai_w#w6)). |
| `SCK` grounded | Strapping that moves the PCM5102A's master clock inside the part, onto its own PLL locked to `BCK`. Costs one pin less and means **the sample rate is whatever Neon's divider produces** ([W.5](sec_ai_w#w5)). |
| 44,146 Hz | This machine's actual sample rate — 103.125 MHz / (32 × 73). Not 44,100, because the iCE40 PLL is integer-only and 44.1 kHz needs a denominator factor of 441 that no setting can produce. +1.8 cents of pitch, published in `AUD_RATE` so nothing has to assume it ([W.11](sec_ai_w#w11), [Q77](sec_ai_q#q77)). |
| `XSMT` | The DAC's soft-mute pin, held low through an RC while the rail rises — **the anti-pop**. It protects power-up only; the power-down click is [Q76](sec_ai_q#q76). |
| Saturating add | Clamping a sum at full scale instead of letting it wrap. Four channels at full volume exceed full scale, and a wrap turns the loudest moment in the material into full-amplitude noise ([W.27](sec_ai_w#w27)). |
| Underrun | A DMA buffer running dry before software refills it. Here the channel **holds its last sample** rather than emitting zero — a step to zero is a click — and sets a sticky flag, because an underrun that cannot be observed is a bug report that says "it crackles sometimes" ([W.22](sec_ai_w#w22)). |
| QSPI | Quad SPI — 4-bit-wide serial bus. Historical here: it went with the PSRAM ([D13](sec_ai_q#d13)) and no longer appears on the board. |
| HID | Human Interface Device — the USB class covering keyboards and mice. |
| USB host controller | The EC's native USB, assigned to host mode in hardware — it handles hub enumeration, the `PRE` packets Low Speed devices need, and bulk transfers in silicon. The assignment is one-way: there is no device port and therefore no USB recovery path ([D1.9](sec_ai_d1#d19)). |
| `PRE` packet | The Full Speed preamble a host must emit before every transaction with a Low Speed device behind a hub. Historically the most fragile path in this family's host stack, which is why [Q102](sec_ai_q#q102) is a bring-up gate rather than an assumption. |
| Hub cascade | A second hub level, created whenever a user plugs a hub into a downstream port. The on-board hub already consumes the one level guaranteed to work ([D1.10](sec_ai_d1#d110)). |
| `J-DBG` · `J-QSPI` | The EC's two headers. The first carries SWD and the console UART, serviced by one probe over one cable; the second carries the bootrom UART and direct access to the flash die ([D1.12](sec_ai_d1#d112)). |
| Rescue debug port | An access point in the EC's debug architecture that can reset the chip even when its firmware is hostile to debugging — a tight loop, a routine that reconfigures the debug pins, a crashed power sequencer. The reason SWD is the primary path rather than the convenient one ([D1.13](sec_ai_d1#d113)). |
| Bootrom UART boot | The EC's second recovery tier: two straps at reset put the bootrom on a 1 Mbaud UART carried on flash-interface pins. **It writes SRAM only**, which is why the RAM flash-writer stub exists ([D1.14](sec_ai_d1#d114)). |
| Mux | Multiplexer — switch routing one set of signals to one of several destinations. **No signal mux remains in the design**; the '3257 that gave the microSD two possible owners was removed with the SD handoff ([G.1](sec_ai_g#g1)). |
| DMA | Direct Memory Access — a device reading or writing memory itself, without the CPU moving each byte. The SPI-SD engine is the only one on this board, and it is the whole reason `CACHE_INVAL_FRAME` exists ([M.12](sec_ai_m#m12)). |

## Operating system and toolchain
  NOTE: → [sheet I](sec_ai_i) · [sheet J](sec_ai_j) · [sheet N](sec_ai_n) · [sheet CN1](sec_ai_cn1) · [sheet O](sec_ai_o)

| Term | Meaning |
|---|---|
| BIOS | Here it means two things kept distinct: the RP2354B is the "board BIOS" (everything pre-CPU), and `BIOS.BIN` is the "system BIOS" (everything post-reset). |
| Info block | The structure the BIOS hands the kernel at load time: RAM size, device map, battery state, RTC time. Format still open ([Q5](sec_ai_q#q5)). |
| Monitor | Minimal interactive debugger: examine and alter memory, load over serial. Two of them exist — one in the BIOS, running on the 65816, and the EC console of [sheet R](sec_ai_r), which covers the same ground from outside the CPU and is available a whole stage earlier. |
| Kernel | The resident, privileged core of the OS. Lives at the top of the virtual map — based at `$FD`, growing down to `$F0` — with its entry, fault and MMU paths pinned in SRAM. Entered only through `COP` or an interrupt, both of which raise privilege on the vector fetch. |
| Syscall | A service request from a process to the kernel. Invoked here through the `COP` instruction, with the service number in the accumulator. |
| PCB | Process Control Block — the per-process record holding saved registers, ASID and page-table pointer. ((Not the printed circuit board, which this document always spells out.)) |
| Context switch | Switching process; entails saving state to the PCB and pointing the MMU at a different page table. |
| Preemptive | The kernel takes the CPU back on its own (on the timer tick) rather than waiting for the process to yield it. |
| Round-robin | Scheduling that simply cycles through ready processes in turn, each getting one quantum. |
| Tick | The periodic timer interrupt driving scheduling. 100 Hz here. 100 Hz, from a free-running counter in Helium — never from cycle counts, which stop being time the moment PHI2 can stall. |
| Zombie | A finished process whose exit status is still held for its parent to collect with `wait`. |
| Driver | Kernel module handling one device behind a fixed 5-function interface, exposed as a `/dev/*` node. |
| devfs | The synthetic filesystem where those `/dev/*` nodes would live — no bytes on the SD card. **Not yet**: `open` resolves `/dev/` by prefix against the device table until something needs to list devices ([D108](sec_ai_q#d108)). |
| ioctl | The escape hatch of the unified I/O interface: device-specific operations that are neither read nor write, such as mapping the framebuffer. |
| tty | A terminal device: a line discipline between an output backend and an input backend. The console is `/dev/tty` — Mode 0 out, Helium's HID queue in — and a serial line, where there is one, is `/dev/ttyS0` ([CN1.9](sec_ai_cn1#cn19)). |
| Line discipline | The layer of a tty that edits a line before any program sees it — echo, erase, kill line — and turns Ctrl-C into an interrupt. It lives in the kernel, not in the shell ([D104](sec_ai_q#d104)). |
| Canonical mode | The line discipline's default: `read()` returns complete lines. **Raw mode** passes every byte at once, with no echo and no editing. |
| Monolithic build | The console linked as one image, with no MMU and no processes, the shell calling kernel functions directly. The **user-mode build** relinks the same shell against the `COP` stubs and runs it as PID 1 ([CN1.1](sec_ai_cn1#cn11)). |
| Degraded mode | The console with no root filesystem: a prompt showing `(no root)`, and only the built-ins that need no files ([CN1.7](sec_ai_cn1#cn17)). |
| Boot partition | The card partition holding the kernel image, which the BIOS reads with no filesystem code at all ([D107](sec_ai_q#d107)). |
| Typematic repeat | A held key repeating. Generated by the EC, since USB HID keyboards do not repeat on their own ([D106](sec_ai_q#d106)). |
| CON-00–CON-04 | The console's series, from a kernel that prints its banner to a shell running as PID 1 ([sheet CN1](sec_ai_cn1)). |
| FAT32 | The filesystem this document once put on the boot card, and now the *first* of the three the host track implements ([Y4.2](sec_ai_y4#y42)) — chosen there for being the cheapest way to get a real filesystem mounted, not for being used here. The boot card is NVFS ([G.3](sec_ai_g#g3)). |
| BSS | The zero-initialised data of a binary. Carries no bytes in the file: the loader just maps it and clears it. |
| Relocation | Patching a binary's addresses to match where it was actually loaded. The MMU removes the need: every process sees the same addresses. |
| ABI | Application Binary Interface — the contract user binaries rely on. Drivers may be rewritten as long as it holds. |
| JSL / RTL | The 65816's long call and return, crossing banks. The basis of the large memory model and of syscall stubs. |
| Large model | Compiler model where code is addressed across all banks with JSL/RTL. Paired here with a fixed DBR so data access stays cheap. |
| Toolchain | The full chain from source to loadable artefact. Open end to end here: KiCad · Yosys · nextpnr · IceStorm · pico-sdk · ca65/64tass. |
| Smart mode | ca65's `.smart`, which follows `REP` and `SEP` and sets operand widths itself — in straight-line code only, which is why every routine still states the width it expects on entry ([O.10](sec_ai_o#o10)). |

## Filesystems
  NOTE: → [sheet Y1](sec_ai_y1) · [sheet Y2](sec_ai_y2) · [sheet Y3](sec_ai_y3) · [sheet Y4](sec_ai_y4)

| Term | Meaning |
|---|---|
| VFS | Virtual File System — the layer between the syscall table and the filesystem drivers. It owns path resolution, the mount table, vnode identity and the error space, because none of those can be decided inside a driver that cannot see across a mount boundary ([Y1.1](sec_ai_y1#y11)). |
| vnode | The in-memory object for one *in-use file*, cached and reference-counted, identified by its mount and a stable file identifier. Not the same as an open file: two `open()` calls share a vnode and hold separate offsets ([Y1.5](sec_ai_y1#y15)). |
| Inode | The on-disk record of a file — type, permissions, size, times, and where its data is. 128 bytes in both NVFS and the ext2 configuration used here. A name is not part of it: names live in directories and point at inode numbers, which is what makes hard links possible. |
| Superblock | The block that describes the whole volume: sizes, region locations, counters, feature flags. NVFS keeps a byte-identical backup at the last block, written only by `mkfs` and `nvfsck`, and **never silently falls back to it** ([Y2.6](sec_ai_y2#y26)). |
| Bitmap · summary | One bit per block or inode saying whether it is allocated, plus — in NVFS — a free-count per bitmap block so the allocator can skip a full one without reading it ([Y2.7](sec_ai_y2#y27)). |
| Extent | A run of consecutive blocks described by one entry: first logical block, first physical block, length. Replaces the indirect tree for files laid down in one or a few runs, which is most of them ([Y2.10](sec_ai_y2#y210)). |
| Indirect block | ext2's alternative: a block full of block pointers, with double and triple levels above it. Cheap to implement, expensive to read — each level is another transfer before any data moves ([Y3.5](sec_ai_y3#y35)). |
| Hole | A logical block covered by no extent and no pointer. Reads as zeros and occupies nothing. |
| Journal | A log of metadata changes written before the changes reach their home locations, so that recovery is a forward scan and a sequence of block copies. NVFS's is **physical, redo-only, metadata-only and circular**, which is what makes replay idempotent ([Y2.15](sec_ai_y2#y215)). |
| Redo-only · idempotent | The journal holds new contents, never old ones, so replay copies blocks to fixed destinations — running it twice is the same as running it once, and a crash *during* recovery is harmless. |
| Checkpoint | Writing a committed transaction's blocks to their home locations and advancing the journal's start pointer. May be deferred and batched; **advancing it before those writes are durable is the one way to lose data** ([Y2.16](sec_ai_y2#y216)). |
| Barrier | The point at which every write issued before it is durable before any issued after. On SD that means waiting out the busy state and confirming — an assumption rather than a guarantee ([Q96](sec_ai_q#q96)). |
| `data=ordered` | The rule that a transaction's file data reaches the medium before its commit block, so metadata can never reference a block whose contents are stale. The faster alternative is refused here ([Y2.18](sec_ai_y2#y218)). |
| Orphan | An inode whose link count reached zero while it was still open. Threaded onto a list in the superblock and freed at the next mount, which is what stops a crash from leaking space ([Y2.19](sec_ai_y2#y219)). |
| Deferred delete | Unlinking a file that is still open: the name goes, the blocks are released when the last reference does. Makes deleting an open file safe rather than catastrophic ([Y1.18](sec_ai_y1#y118)). |
| Feature flags | Three masks in the superblock. An unknown *incompatible* bit refuses the mount, an unknown *read-only* bit mounts read-only, an unknown *compatible* bit is ignored — and the implementation **must name the bit it did not recognise** ([Y2.20](sec_ai_y2#y220), [Y3.4](sec_ai_y3#y34)). |
| htree · `DIR_INDEX` | ext2's hashed directory index, hidden inside fake entries so that a linear reader sees the directory correctly. **Reading is safe and writing is not**: an insert that does not update the index leaves a file that exists, occupies space, appears in `readdir` and cannot be opened by name ([Y3.6](sec_ai_y3#y36)). |
| `readdir` cookie | An opaque value a driver hands back to resume iteration. NVFS advances a slot index and ext2 a byte offset; neither is expressible in the other's terms, so the VFS stores it and never interprets it ([Y1.3](sec_ai_y1#y13)). |
| `fsck` · `e2fsck` · `nvfsck` | Host-side repair tools. **There is no on-target `fsck` and none is planned** for either filesystem: NVFS recovers from its journal and its orphan list, and ext2's recovery is the host's ([Y2.22](sec_ai_y2#y222), [Y3.2](sec_ai_y3#y32)). |
| Differential testing | Performing every operation twice — once through the implementation under test and once through a reference driver — and comparing. What makes the host track tractable ([Y3.15](sec_ai_y3#y315)). |
| Crash injection | Hooking a specific write number, truncating the image there, and checking that what remains is clean or trivially recoverable. The harness that found draft 2's ordering bugs ([Y2.2](sec_ai_y2#y22)). |
| FUSE | Filesystem in Userspace — the Linux mechanism the host track mounts through. Its **low-level, inode-keyed API** is the one that transfers; the path-based one does not, because a driver here never sees a path ([Y4.6](sec_ai_y4#y46)). |
| `fsops` | The internal table the host track discovers by implementing three filesystems behind it — its actual deliverable, and the candidate shape for [sheet Y1](sec_ai_y1)'s per-vnode operations ([Y4.5](sec_ai_y4#y45)). |
| Corruption corpus | A set of deliberately damaged images kept as a regression suite. **A hang counts as a failure**, which is why every run carries a timeout — without one a hang reads as a slow pass ([Y4.12](sec_ai_y4#y412)). |
| MBR type `0x7F` | The partition type byte reserved for local and experimental use, and the one an NVFS volume carries. `0x7A` and `0x7B` are unsafe — they alias hidden-FAT types ([D52](sec_ai_q#d52)). |

## The windowing OS
  NOTE: → [sheet V](sec_ai_v)

| Term | Meaning |
|---|---|
| `wserver` | The window server: window objects, z-order, input routing, focus, decoration and client validation. A **user task** here, because none of that needs a privileged instruction — the compositor beside it is kernel code, because command emission does ([Q62](sec_ai_q#q62)). |
| `tk` · `gcl` | The client-side libraries: the widget toolkit and the drawing layer that appends ops to the shared buffer. Both link into the application; neither is a server component. |
| Shared command buffer | The 4 KB page `mshare` maps writable in the client and readable in the server. Drawing ops accumulate in it and flush with one syscall — **a syscall per primitive would cost more than the primitive** ([V.20](sec_ai_v#v20)). |
| Content list · composite list | The two kinds of command list a GUI keeps in SDRAM: one draws into a window's backing store and runs **when its content changes**, the other blits that store into the back buffer and runs **every frame**. Text lives in the first, which is why an idle window costs nothing. |
| String cache | Composed runs of glyphs held as a strip in SDRAM, so drawing a repeated label is one `COPY_RECT` instead of one command per character. Attacks emission cost, not bandwidth — and proportional fonts fall out of it free, since it stores runs rather than glyphs. |
| `DRAW_GLYPHS` | A proposed command taking a string pointer and a count, so a line of text is one command with no cache at all. **Complementary to the cache rather than a replacement**: the cache wins for stable labels, this wins for text that changes ([Q64](sec_ai_q#q64)). |
| Refresh event | The message an Amiga client got when part of its window became visible again, obliging it to repaint. **There is none here**: the backing store already holds the pixels, so a client paints when its own state changes and never otherwise. |
| `layers.library` | The Amiga layer that answered *what is behind this window and who repaints it* — cliprects, `SIMPLE_REFRESH`, `SMART_REFRESH`, `SUPER_BITMAP`. Per-window backing stores delete the question, and the library with it. |
| Intuition · IDCMP · BOOPSI | Amiga's window system, its event protocol and its widget object model. Named here as the reference the design departs from: `wserver`, a ten-event set, and a static vtable toolkit respectively. |
| Z-order | The front-to-back ordering of windows. The compositor draws back to front — painter's algorithm — so occlusion needs no region arithmetic at all: the front window is simply drawn afterwards. |
| Decoration | The frame, title bar and gadgets the server draws **into the window's own backing store**, above the content area and clipped away from the client. Composited as one wide blit rather than four narrow ones, which is what [T3.18](sec_ai_t3#t318) asks for. |
| Live drag | Moving a window by recompositing every frame rather than dragging an XOR outline and moving the pixels once. Affordable here, and the default. |
| Hit test | Walking the z-list front to back to find which window a pointer position belongs to. Decoration hits stay in the server; content hits are delivered to the client in window-relative coordinates. |
| Port · signal · message | The Exec model, proposed for this kernel: a port bound to one bit of a task's 32-bit signal mask, fixed 32-byte messages copied by the kernel, and `task_wait` as **the single blocking primitive** ([Q63](sec_ai_q#q63)). |
| Coalescing | Collapsing a burst of events into the latest one — never more than one motion event per frame per client. Not an optimisation at ~12 µs of kernel copy per message, and it constrains the HID event format to absolute state rather than deltas. |
| Overdraw | Total composited area ÷ screen area, counting the desktop clear. The number that decides whether full recomposition fits: ~1.8× is comfortable at 1 bpp and consumes the whole frame at 8 ([V.10](sec_ai_v#v10)). |
| Widget vtable | The toolkit's dispatch: a static `init · render · event · layout · attr` table per class, deliberately mirroring the kernel's five-function driver interface. ~15 cycles per call — right at widget granularity, wrong at pixel granularity. |
| Upload | The escape hatch for imagery Neon's primitives cannot produce: the client rasterises into system RAM and the server pushes it through the aperture. **~15 ms for a 200 × 100 patch at 8 bpp** — correct to provide, correct to discourage. |

## Debug and instrumentation
  NOTE: → [sheet R](sec_ai_r) · [sheet EM8](sec_ai_em8)

| Term | Meaning |
|---|---|
| Debug agent | The block inside Helium that performs memory and bus accesses on command from the RP2354B. A requester in the arbiter, not an external master. |
| Internal access | A transaction satisfied entirely inside Helium — SRAM, SDRAM or Helium's own registers. Nothing appears on the CPU bus. |
| External cycle | A transaction where Helium drives the CPU bus pins, so devices outside it see a cycle indistinguishable from the 65816's. The only way to reach the `$FE` aperture. |
| PHI2 stall | Freezing the CPU clock to steal bus time or to halt. Legal because the core is static; the same gating logic serves cache fills, halts, external cycles and Neon's read stall. |
| Cycle stealing | Taking the bus within a window the CPU is not using, instead of stalling it. The cheaper of the two paths when it is available. Available only where the CPU leaves a gap; where it does not, the stall above is the fallback. |
| Trace buffer | Ring buffer in EBR recording one entry per bus cycle — address, data, and the control pins. A logic analyser built into the gateware. |
| Trigger · arming | The address-and-mask comparison that starts or stops a capture, and the act of enabling it. Position selects whether the captured window sits before, around or after the match. |
| Scan chain | The register-readout path debuggable CPUs provide. The W65C816S has none, which is why its registers can only be inferred or dumped by a stub (→ [R.15](sec_ai_r#r15)). |
| Debug stub | A short routine that pushes every CPU register to a known location. Authoritative and intrusive — it perturbs the state it reports, so the console never runs it silently. |
| W1C | Write-1-to-Clear — a status bit cleared by writing a one to it, so two readers cannot clear each other's flags by accident. |
| March test | Memory test that walks a pattern up and down the array in a defined order, catching stuck, coupled and address-decode faults that a simple write-read pass misses. |
| Walking ones · address-in-address | The two other standard patterns: one bit moved through each word, and each cell holding its own address. The second is what finds a swapped address line. |
| Turnaround | The gap a bus needs between one driver releasing and the next asserting. Sized in clocks from the datasheet, never guessed — too short shorts two drivers, too long wastes the cycle. |
| Clock domain crossing | Passing a signal between two unrelated clocks — here the SPI link and the Helium core. Needs synchronisers and a handshake, and is a classic home of intermittent faults. |
| GDB stub | Firmware speaking the GDB remote serial protocol, letting a host debugger drive the target. Deferred until the command set stops moving (→ [R.24](sec_ai_r#r24)). |
| Breakpoint · watchpoint | Halt on reaching an address · halt on touching a datum. The first is `BRK` or a trace-trigger comparator; the second is deferred. |
| Debug Adapter Protocol · DAP | The JSON protocol between an editor and a debugger, which VS Code speaks; [sheet EM8](sec_ai_em8)'s adapter is a server for it. **Not CMSIS-DAP or DAPLink**, the probe protocols, which share only the letters. |
| Source map | The two maps a source-level debugger needs — address to file and line, and file and line to every address it produced. Read for assembly from the ld65 debug file ([EM8.5](sec_ai_em8#em85)). |
| `.dbg` file | What `ld65 --dbgfile` writes: segments, spans, lines and symbols as tab-separated text records. Produced by every build, never by a separate debug build ([D128](sec_ai_q#d128)). |
| Shadow stack | A host-side record of call and interrupt frames kept beside the guest's stack, one per address space, from which the call stack is drawn. A frame goes when S passes it, not when a return opcode is seen ([EM8.15](sec_ai_em8#em815)). |
| DBG-00–DBG-05 | The source-level debugger's series, from a source map to the same adapter driving the board ([sheet EM8](sec_ai_em8)). |

## Emulation and the host model
  NOTE: → [sheet EM1](sec_ai_em1) · [sheet EM4](sec_ai_em4) · [sheet EM7](sec_ai_em7)

| Term | Meaning |
|---|---|
| Emulator | Here, a PC-hosted functional and timing model of the whole machine, in C11, running natively and in a browser. Not a simulator of the gateware: it executes no RTL ([EM1.5](sec_ai_em1#em15)). |
| Fidelity | How closely a subsystem is modelled. Chosen per subsystem against one rule — **model what software can observe** — so the blitter is bit-exact and its timing is not ([EM1.7](sec_ai_em1#em17)). |
| Bus layer | The spine of the design: every access passes through it, and the cycle counter lives there rather than in the CPU. Cycle accuracy becomes a property of emitting the right accesses in the right order ([EM7.7](sec_ai_em7#em77)). |
| Cycle-stepped | Advancing the model one bus cycle at a time rather than one instruction at a time. Cheap on this part, because **every 65816 cycle is a bus cycle** ([EM7.5](sec_ai_em7#em75)). |
| Idle cycle | An internal-operation cycle. It still drives an address and still costs a cycle; it simply transfers nothing. Omitting one leaves an instruction a cycle short. |
| Open bus | What unpopulated physical space reads as — `$FF` here, not zero. A model that returns zero hides address-decode bugs. |
| Wait states · stretched clock | The two ways a CPU waits for memory. Wait states hold the CPU on `RDY` while PHI2 free-runs, so a stall rounds up to whole cycles; a stretched clock halts PHI2 and pays the latency exactly. **noVa64 stretches** ([EM2.4](sec_ai_em2#em24)). |
| Wall time | Elapsed time, accumulated separately from the cycle count because under a stretched clock the two are no longer proportional ([EM2.12](sec_ai_em2#em212)). |
| Parameter set | The runtime-configurable timing values — cache geometry, TLB depth, SDRAM timings, emission cost. Parameterised because none of them is fixed in this document, so the emulator can produce them rather than consume them ([EM2.2](sec_ai_em2#em22)). |
| Sweep | Running the same workload across a range of one parameter to see what it changes. Worthless against a synthetic workload ([EM6.6](sec_ai_em6#em66)). |
| Tag-only cache | A cache model holding tags, valid, dirty and LRU state but **no line data**, because the backing arrays are authoritative and nothing can observe cache contents except through timing ([EM1.9](sec_ai_em1#em19)). |
| Record and replay | Logging every non-deterministic input as a `(cycle, event)` pair at the mailbox boundary, so a session replays exactly. Cheap if built in from the start, expensive afterwards ([EM7.42](sec_ai_em7#em742)). |
| Determinism test | Running one trace twice and asserting identical cycle counts, memory hashes and register state. The strongest cheap test in the exercise. |
| Oracle | Something you did not write that says whether your answer is right. This project has exactly one — the external 65816 suites — and none at all for the MMU, cache or blitter ([EM7.27](sec_ai_em7#em727)). |
| SingleStepTests · Tom Harte | Per-instruction test vectors giving an initial state, a final state and **the complete bus cycle trace**, so they check the cycle sequence rather than the total ([EM7.23](sec_ai_em7#em723)). |
| Klaus Dormann tests | A binary that exercises 6502 behaviour exhaustively and traps on failure. Covers emulation mode. |
| Additive divergence | Extending the CPU behind the reserved `WDM` prefix rather than by changing an existing opcode, which leaves the published suites valid. **In tension with [M.3](sec_ai_m#m3)** ([EM7.26](sec_ai_em7#em726)). |
| Guest side · host transport | The rule governing every emulator interface: the device the guest sees must be hardware-real, and only the host end may be invented. Breaking it produces software that runs under emulation and fails on silicon ([EM3.1](sec_ai_em3#em31)). |
| Boot image | A raw 8 KB binary at `$00E000`–`$00FFFF` carrying its own vectors — what the EC places in memory before releasing reset. **There is no ROM in this machine**, so "BIOS" means only the image the EC loads ([EM2.15](sec_ai_em2#em215)). |
| Ring origin | How a text mode scrolls without moving memory: a row index advances and one row is cleared, so a scroll costs the CPU nothing ([EM7.46](sec_ai_em7#em746)). |
| Tee | A host-only development aid that streams every byte written to the text port straight to stdout. Convenient because it skips Neon entirely, and dangerous for the same reason ([EM4.13](sec_ai_em4#em413)). |
| WebAssembly · wasm | The portable bytecode the emulator compiles to for browser delivery. Single-threaded here, so no cross-origin isolation headers are needed ([EM5.12](sec_ai_em5#em512)). |
| WASI | The system interface a wasm module outside a browser targets. Supplies the libc the module links against; only its write call does anything here. |
| Sysroot · builtins | The WASI headers and libraries, and the compiler-rt support routines that must sit in the compiler's own resource directory. Their release has to sit near your LLVM or the linker rejects them ([EM5.4](sec_ai_em5#em54)). |
| Reactor model | A wasm execution model for a module with no `main`. **Deliberately not used**: it is a target option, so a clang lacking the wasm target reports it as an unknown argument and misdirects the diagnosis ([EM5.2](sec_ai_em5#em52)). |
| Pointer lock | The browser API that captures the pointer and reports relative motion. Not a convenience: it is the capture mechanism a relative-motion protocol requires ([EM3.13](sec_ai_em3#em313)). |
| Key code | The browser's name for a key **by physical position** rather than by the character it produces, so host keyboard layout does not leak into the guest ([EM5.11](sec_ai_em5#em511)). |
| jsdom | A DOM implementation without a renderer, used to drive the browser shell headlessly. **Verifies wiring and not presentation** ([EM5.17](sec_ai_em5#em517)). |

## The prototype board

| Term | Meaning |
|---|---|
| Prototype board | The single-ECP5 carrier of [sheet P2](sec_ai_p2) — Helium and Neon merged on one commercial module, with the CPU, SRAM, EC, VGA and audio on a board of our own. Temporary packaging of the design, never a variant of it ([D40](sec_ai_q#d40)). |
| Colorlight i9 v7.2 | The commercial module the prototype is built around: an LFE5U-45F with 8 MB SDRAM, 8 MB SPI flash, two unused Ethernet PHYs and a 25 MHz oscillator, on a DDR2 SODIMM edge connector. Sold for LED-panel drivers and widely used as a cheap FPGA board. |
| ECP5 | Lattice's larger FPGA family. Rejected for the target board by [D01](sec_ai_q#d01) — BGA only in the useful sizes, and the project's rule is hand-solderable — which is exactly why it is acceptable on a module somebody else soldered. |
| SODIMM | The 200-pin edge connector the i9 module plugs into. It carries **raw FPGA balls**, not buffered I/O, which is what makes the module usable as a general-purpose carrier at all. |
| PMOD | The 2 × 6 header convention used by the i9 extension board. Whether its pins are direct or pass through unidirectional buffers decides whether the wire-wrap stage is possible ([Q67](sec_ai_q#q67)). |
| DAPLink | The on-board debug probe of the i9 extension board, giving JTAG plus a serial bridge. Absent on a carrier that hosts the SODIMM socket directly, which is why the RP2354B picks up ECP5 JTAG there ([P2.10](sec_ai_p2#p210)). |
| prjtrellis · nextpnr-ecp5 | The ECP5 half of the same open toolchain — Yosys and nextpnr, different backend. Added to [E0.1](sec_ai_p3#e01) by the prototype; no proprietary tools on either board. |
| Letterboxing | Showing a window into a buffer larger than the display rather than reflowing the buffer. How Mode 0 keeps its 128 × 32 geometry on a 640 × 480 monitor ([D44](sec_ai_q#d44)). |
| Leak | A prototype convenience that survives into the target design and becomes a defect there — shared memory, one clock domain, abundant EBR, a hardcoded size. [Sheet P2](sec_ai_p2) carries the list, and it is reviewed at every merge, not at the transition. |

## The NVM32 virtual machine and noVa128
  NOTE: → [sheet VM1](sec_ai_vm1) · [sheet NV1](sec_ai_nv1)

| Term | Meaning |
|---|---|
| NVM32 | The project's 32-bit register virtual machine: sixteen 32-bit registers, a 24-bit address space, 16-bit code units and no flags. Designed so that **one binary runs interpreted on the 8 MHz 65816 and natively on a core** ([VM1.1](sec_ai_vm1#vm11)). Deferred until the kernel runs its first user process. |
| Bytecode | An instruction set executed by software, or by hardware built for it, rather than by the CPU the machine is made of. Here it is not an interchange format: the same NVX image is the input to every executor. |
| Architectural state | The state an instruction set promises to preserve — for NVM32, **{R0–R15, PC} and nothing else** ([VM1.14](sec_ai_vm1#vm114)). It is what makes a process migratable mid-execution between interpreter and core, and every proposal that would add to it pays against that. |
| Executor | Any implementation that runs NVM32: the C11 reference interpreter, the 65816 interpreter, the bytecode coprocessor, or Argon 2's native mode. All four must be **bit-identical**, down to shift counts ≥ 32 and division by zero. |
| Golden model | The implementation every other one is compared against. Here the C11 reference interpreter, hosted in the emulator ([EM1.3a](sec_ai_em1#em13a)) — the same differential pattern already used on the filesystem ([Y2.22](sec_ai_y2#y222)). |
| NVX | The NVM32 executable format: magic, ISA version, a feature-bit vector, a 24-bit entry PC and a section table. **Linked at fixed addresses and never relocated**, because every process owns its whole 24-bit space ([VM1.42](sec_ai_vm1#vm142)). |
| ILP32-24 | NVM32's C ABI: 32-bit `int`, `long` and pointer, the pointer holding a 24-bit address in four bytes with the top byte required to be zero. Deliberately divergent from Calypsi's 16-bit `int`, and the two meet only at the syscall marshalling layer ([VM1.35](sec_ai_vm1#vm135)). |
| 32-bit clean | A pointer model where the unused high bits **must** be zero and are checked rather than ignored — the 68000 lesson applied on purpose, since software that stored flags there broke when full addressing arrived ([VM1.16](sec_ai_vm1#vm116)). |
| Code unit | The 16-bit quantum an NVM32 instruction is built from: one, two or three of them, with **the opcode byte alone determining the length**. The Dalvik pattern, chosen because one 65816 fetch yields an opcode plus two register nibbles ([VM1.22](sec_ai_vm1#vm122)). |
| Dispatch | The cost of deciding which handler runs, paid once per VM instruction. ~18 of the ~70 cycles of an interpreted `ADD`, and **the number every encoding candidate is trying to amortise** ([VM1.45](sec_ai_vm1#vm145)). |
| Superinstruction | One opcode doing the work of a common sequence, so the sequence pays one dispatch instead of several. `ENTER`, `LEAVE` and compare-and-branch are the adopted ones ([VM1.28](sec_ai_vm1#vm128)). |
| The gate | The single indirect entry point through which native code enters bytecode, resolved at boot into the system information block. Three implementations — interpreter, coprocessor, native mode — behind one signature, **so only a 3-byte vector differs between machines** ([VM2.16](sec_ai_vm2#vm216)). |
| System information block | The BIOS-to-kernel contract: a shared read-only page in bank `$00` carrying a format version, the CPU identity, Helium's capabilities, coprocessor presence and the resolved gate ([I.7](sec_ai_i#i7), [D91](sec_ai_q#d91)). **BIOS implementations may differ between machines; this may not.** |
| `WDM` | Opcode `$42`, reserved by WDC for expansion and **a two-byte no-op on a real 65816**. Used as the CPU probe and as Argon 2's NVM32 mode gate — which bounds [M.3](sec_ai_m#m3) rather than reversing it ([D89](sec_ai_q#d89)). |
| Shadow dispatch bank | A second copy of the interpreter whose 256 dispatch entries all point at the exit handler. Switching a process's saved PBR lands it in the kernel at the next exact VM instruction boundary, **at zero cost on the common path** ([VM2.33](sec_ai_vm2#vm233)). |
| vbcc | The retargetable C compiler selected for NVM32 — ruled out for the 65816, where it has no 16-bit code generation, and chosen here because the target was designed after it ([D96](sec_ai_q#d96)). |
| T0–T5 | The NVM32 toolchain's gate series, independent of E/G/K. **T3 collects the opcode histogram and T4 freezes the ISA on it** ([VM4.31](sec_ai_vm4#vm431)). |
| noVa128 | The successor machine: Helium 2, Neon 2 and Argon 2, a 16-bit inter-FPGA path, and one core replacing the W65C816S ([sheet NV1](sec_ai_nv1)). |
| Argon 2 | noVa128's CPU: a tri-mode softcore running 6502 emulation, 65816 native and NVM32 native. **Not to be confused with Argon**, which in noVa64 is FPGA-C, the device holding the unpopulated slot ([NV1.1](sec_ai_nv1#nv11)). |
| Instruction-compatible | Argon 2's contract: architectural state matches a real 65816 after **every instruction**, while cycle counts, interrupt latency and internal bus accesses may diverge. Affordable only because the PHI2 stall already withdrew cycle counting as a measure of time ([NV1.5](sec_ai_nv1#nv15)). |
| Idempotent on read | A register whose value is unchanged by reading it. Required of every memory-mapped register, because a 65816 read-modify-write performs spurious accesses that an instruction-compatible core does not reproduce ([M.15](sec_ai_m#m15), → [Q170](sec_ai_q#q170)). |
