dmolinagarcia/nova64/docs/docsV3/content/sec_ai_j.md

# Operating system
> how it uses the BIOS · what it provides to processes

Small monolithic kernel, written in C with assembly only where it hurts. It consumes the BIOS for a few milliseconds and then provides everything else.

- J.1 — Model: preemptive kernel resident at the top of the virtual map — fixed base in bank `$FD`, growing downward to a floor at `$F0` ([D102](sec_ai_q#d102)) — with its entry, fault and MMU paths pinned in SRAM, and mapped identically and privileged in every process's page table.
  NOTE: Mapped identically in every process's table means a syscall changes privilege, not address space — the kernel is already resident at those addresses when the `COP` vector is fetched ([L.12](sec_ai_l#l12)).
- J.2 — How it uses the BIOS: only the info block and the `JSL` table during the transition; its drivers replace the console and SD, and from then on the BIOS goes inert.
- J.3 — Syscall mechanism: `COP`, with the service number **in the accumulator**, loaded by the libc stub immediately before the instruction. The handler indexes its dispatch table straight from A; arguments stay wherever the C compiler's calling convention left them. So the stable ABI is exactly "**calling convention + a number in A**" — nothing is marshalled, and the stubs that carry it are three lines each (→ [O.7](sec_ai_o#o7)). ((The inline signature byte is still emitted, but no longer read: it survives for disassembly, tracing and static verification of a binary. Taking the number from A instead of walking the stack for it saves 20–30 cycles on every single call.))
  NOTE: **One constant needs verifying against the WDC manual before anything is built on it.** The assumption recorded earlier — that the signature byte sits at stacked `PC−2` — appears to be off by one: `COP` increments PC past the signature before pushing, placing it at `PC−1`. Irrelevant to the handler, which no longer reads it, but a tracer or a static verifier built on the wrong constant misdispatches silently rather than failing (→ [Q75](sec_ai_q#q75)).
  NOTE: The 65816's other software interrupt, `BRK`, is reserved for the debugger and must stay that way — two software traps with separate vectors is exactly enough to keep breakpoints from colliding with system calls.
  NOTE: The width of `A` at the `COP` decides how many service numbers can exist — 256 with an 8-bit accumulator, and the libc stub is what sets the width it means. Fixing that convention belongs to the ABI audit of [E0.8](sec_ai_p3#e08), not to the first stub that needs it.
  NOTE: **[D90](sec_ai_q#d90) turns that dispatch table into a commitment: kernel services are reached through a *numbered service table*, and never through `COP` signatures scattered across the code.** The immediate reason is the VM — guest bytecode may never call a native address, because an address is meaningless on an executor with no 65816 in it, so native extension is offered as **data**, a small integer the host resolves ([VM1.40](sec_ai_vm1#vm140)). **The table is better hygiene for the kernel whether or not the VM is ever built**, which is why it is settled now: a number space can be audited, versioned and marshalled across an ABI boundary, and a scattered signature byte cannot.
- J.4 — Internal drivers with a fixed 5-function interface — `init · read · write · ioctl · irq_handler` — reached through a device table indexed by device number, and exposed as `/dev/*`. A minimal VFS decides only whether an `open` routes to the filesystem or to that table.
  NOTE: **The console is the first driver built against it**, from the monolithic build onward ([D111](sec_ai_q#d111)), and the routing this item describes survives as exactly one check: `open` resolves `/dev/<name>` against the device table, and every other path goes to [sheet Y1](sec_ai_y1)'s VFS ([D108](sec_ai_q#d108), [CN1.15](sec_ai_cn1#cn115)).
  NOTE: Drivers expose **no syscalls of their own**, and that is the point: per-driver calls would break the ABI every time a chip changed. Swapping hardware means rewriting one driver against the same internal interface, while libc and the syscall numbering stay put.
  NOTE: The screen console is one of these and needs **no initialisation at all** — the hardware mechanism is identical to the BIOS's, the same stores to the same addresses, wrapped so `write()` is a loop over `putchar`. One requirement is not free and cannot be retrofitted: **the console driver must hold its own scrollback in system memory and be able to repaint from it**, because the text buffer occupies block RAM a graphics mode may reclaim, so a mode switch and back can destroy the screen contents (→ [T1.55](sec_ai_t1#t155), [Q45](sec_ai_q#q45)).
- J.5 — Framebuffer: the preferred path is an ioctl that maps VRAM pages (`$FE`) into the process's address space — no per-pixel `write()`. **Two things now qualify that**, both from [sheet T1](sec_ai_t1). The mapping is for **asset upload and command emission, not for painting**: a process that walks the framebuffer runs at the ~1.3 MB/s aperture rate while the blitter beside it runs at ~100, and the whole of Neon is arranged so the CPU writes pixels once per asset and never again ([T1.2](sec_ai_t1#t12), [T1.56](sec_ai_t1#t156)). And **the aperture is data all the way through, deliberately**: Neon's control registers were moved out of it into `$FF:8000`, so a process holding a mapping cannot reach `LIST_BASE` and aim the command processor — which reads and writes all 64 MB with no MMU in front of it — wherever it likes. That escape was real in an earlier draft, and the fix is now structural rather than a rule the mapping ioctl has to remember, because bank `$FF` is unmappable to user space by construction ([T1.21](sec_ai_t1#t121), [D36](sec_ai_q#d36)). **Power is the mirror case and now the proof of the rule**: shutting the machine down is as privileged an act as exists, and it still adds nothing to the dispatch table. It is `/dev/power` — an `ioctl` for poweroff and reboot, a `read` for battery state — and the privilege check comes free from the node's permissions rather than from a bespoke gate inside a `sys_poweroff()` (→ [S.11](sec_ai_s#s11)).
  NOTE: The kernel's own shutdown path is not a driver concern and is spelled out in [S.13](sec_ai_s#s13). One step of it belongs here: **quiescing the MMU before halting.** The cache is write-back, so a shutdown that flushes the filesystem but not the cache loses exactly the writes the filesystem just made.
- J.6 — **Filesystem: specified, and it is three sheets rather than a line.** [Sheet Y1](sec_ai_y1) is the VFS — the vnode model, path resolution, the mount table, one error space and the concurrency contract; [sheet Y2](sec_ai_y2) is NVFS, the native journalled volume the machine boots from and will page from; [sheet Y3](sec_ai_y3) is ext2, read-only by recommendation, for cards that arrived from a host. Per-device blocking queues and basic IPC as before.
  NOTE: **This supersedes the sketch that stood here** — "FAT over the SD + minimal devfs" — in three ways worth naming. The card is **not FAT** ([G.3](sec_ai_g#g3)). The VFS is **not minimal**: [J.4](sec_ai_j#j4)'s claim that it "decides only whether an `open` routes to the filesystem or to that table" is exactly the shape [Y1.1](sec_ai_y1#y11) rejects, because mount traversal, symlink bounds and vnode identity have no home inside a driver. And whether the device table lives inside the namespace as a `devfs` — which decides whether `open` and `close` slots are needed per vnode — is open rather than assumed ([Q95](sec_ai_q#q95)).
  NOTE: The one thing the sketch had right is the one thing that does not change: **`/dev/*` and the five-function driver interface of [J.4](sec_ai_j#j4) stay**, and no filesystem adds a syscall of its own ([D23](sec_ai_q#d23), [Y1.20](sec_ai_y1#y120)).
- J.7 — **The windowing OS is specified in [sheet V](sec_ai_v)**, and it lands on this sheet in three places rather than beside it. **The compositor is kernel code and the window server is not** — not by preference but because [D36](sec_ai_q#d36) put `CMD_PORT`, `LIST_BASE` and `VRAM_PAGE` in bank `$FF`, so **command emission is privileged** and a user task cannot drive Neon however many aperture pages it holds. **The client drawing protocol needs no new mechanism**: the per-client command buffer is `mshare`, a 4 KB page writable in the client and readable in the server, flushed with one syscall for 5–200 drawing ops. And the hardware is reached through a `/dev/neon` node and an `ioctl` — two calls a frame, to start a list and to swap the buffers — which keeps [D23](sec_ai_q#d23)'s rule that no subsystem adds a syscall of its own (→ [V.16](sec_ai_v#v16), [Q62](sec_ai_q#q62)).
  NOTE: **One genuine addition to the dispatch table is proposed and it is the first since the table was written**: ports, signals and 32-byte messages — `port_create` · `port_send` · `port_recv` · `task_wait` · `task_signal`. They are general primitives rather than one subsystem's verbs, which is the test [D23](sec_ai_q#d23) set. The condition attached is that **there must be one blocking primitive, not two**: [N.3](sec_ai_n#n3)'s per-device blocked queues have to fold onto signal bits, or a process waiting on a device and a message has nowhere to wait (→ [Q63](sec_ai_q#q63)).

## v1 dispatch table — Unix-shaped, deliberately small. Numbering the `SYS_*` constants is still pending.

| Group | Calls | Notes |
|---|---|---|
| Processes | `exec(path)` · `exit(code)` · `wait(pid)` · `getpid()` · `yield()` · `sleep(ms)` · `kill(pid,sig)` | `exec` loads the binary from the card (→ [N.6](sec_ai_n#n6)). `sleep` is backed by Helium's free-running counter, never by cycle counting. Signals stay minimal: KILL, TERM, perhaps one user-defined. |
| Memory | `sbrk(n)` · `mmap(addr,n,prot)` · `munmap` · `mshare(pid,addr)` | `sbrk` only moves the heap end; the frames arrive later by ABORT. `prot` maps straight onto the PTE R/W/X bits. `mshare` is optional — shared-memory IPC, and the reason the cache may never migrate a frame (→ [L.3](sec_ai_l#l3)). |
| Files and devices | `open(path,flags)` · `close(fd)` · `read` · `write` · `seek` · `stat` · `unlink` · `rename` · `mkdir` · `readdir` · `ioctl(fd,op,arg)` | One unified surface: a path resolves either to the filesystem or to the device table, and everything past that point is the same seven calls. `ioctl` is the escape valve for whatever does not fit. |
| Time and IPC | `time()` · `pipe()` | Little more than this in v1. |
  NOTE: **The console needs eight calls this table does not have** — `chdir`, `getcwd`, `rmdir`, `dup`, `dup2`, `sync`, `opendir` and `closedir`, all of which [Y1.20](sec_ai_y1#y120) maps — and an `exec` that takes an argument vector and creates a process ([CN1.26](sec_ai_cn1#cn126), → [Q183](sec_ai_q#q183), [Q178](sec_ai_q#q178)).
