dmolinagarcia/nova64/docs/docsV3/content/sec_ai_p2.md

# Phase 1 · the prototype carrier · P0–P5
> one ECP5 · two devices on one die · partitioning discipline

The **P-series** builds a prototype carrier around a commercial Colorlight i9 module, with Helium and Neon merged into a single ECP5 and everything else — CPU, SRAM, EC, video, audio — outside it. It exists because the entire software roadmap was queued behind hardware that has not been drawn yet, and because gateware debugged on a bitstream costs a rebuild where the same bug on a PCB costs a respin. It is temporary packaging of the design, not a variant of it (→ [D40](sec_ai_q#d40)).

It is **Phase 1** of the three phases of [sheet P1](sec_ai_p1): the training rig of [S0](sec_ai_p1#s0)–[S11](sec_ai_p1#s11) runs before it and is disposable, and the target board of [sheet P3](sec_ai_p3) follows it. The laptop stages and the host filesystem track that used to close this sheet are [sheet P4](sec_ai_p4).

F.phase1.The same three phases with **Phase 1** highlighted: this sheet is the middle track, between the disposable rig above it and the target board it commits to below.

## The prototype board — one ECP5 carrying two devices

- P2.01 — **What it is.** One Colorlight i9 v7.2 module — Lattice LFE5U-45F-6BG381C, 44,000 LUT4, 108 × 18 kbit EBR ≈ 243 KB, 8 MB SDRAM (M12L64322A, 512K × 32 × 4 banks), 8 MB SPI flash, 25 MHz oscillator on ball P3 — on a four-layer carrier of our own holding the W65C816S in its PLCC-44 socket, the SRAM, the RP2354B, a VGA output and the PCM5102A. Power is USB. The toolchain is the same open one, with `nextpnr-ecp5` beside the `nextpnr-ice40` that E0.1 already requires.
  NOTE: The module's two Broadcom B50612D Ethernet PHYs are never used and **share a reset line on ball P4**: assert it at configuration and leave it asserted. It reclaims a few hundred milliamps and removes a switching-noise source next to the CPU bus.
- P2.02 — **What it deliberately is not.** No battery, no charger, no fuel gauge, no rail sequencing, no panel interface of any kind, no touch, no 10.1" panel. Sheets [C](sec_ai_c) and [S](sec_ai_s) are simply not exercised here, and that is a **gap to note rather than to close** — the RP2354B's power-sequencing role, the whole of the `$FF` power block and the shutdown path get their first hardware on the target board (→ [Q73](sec_ai_q#q73)).
- P2.03 — **Logic budget — comfortable, and the slack is the instrument.**

| Block | LUT4 |
|---|---|
| Helium: MMU, TLB, cache controller, arbiter, peripherals | 3,000 – 4,000 |
| Neon: scanout, blitter, compositor, audio DMA | 3,300 – 3,900 |
| Shared SDRAM controller and QoS arbiter | 1,200 – 1,800 |
| VGA timing generator and palette lookup | 150 – 250 |
| Debug agent, trace buffer, instrumentation | 800 – 1,200 |
| Clock domain crossing, glue | 400 – 600 |
| **Total** | **8,850 – 11,750** |

  NOTE: 20 – 27 % of 44,000. The unused capacity buys what will never fit in an HX8K: wide trace buffers, bus transaction counters, cache hit/miss histograms, an embedded logic analyser on the 65816 bus. Build it now — it is free exactly once.
- P2.04 — **EBR is where the prototype lies to you, and it is the most dangerous number on this sheet.** The ECP5 has ~243 KB. **Each target iCE40 HX8K has 16 KB** — 32 blocks of 4 kbit ([D01](sec_ai_q#d01), [T1.3](sec_ai_t1#t13)) — and Neon's text buffer and font already spend 12 KB of Neon's 16 ([T1.12](sec_ai_t1#t112) calls the budget fully allocated with zero margin). A 16 KB trace buffer, which is nothing here, is *larger than the whole of Helium's block RAM there*. Every EBR consumer therefore carries a synthesis parameter whose **default is the target value**, and the prototype only ever raises it for instrumentation, never for function (→ [P2.18](sec_ai_p2#p218)).
- P2.05 — **Pin budget.** Counted from the wuxx i9 v7.2 pinout, excluding GND, 5 V, NC and the Ethernet pairs, **106 FPGA balls** reach the SODIMM connector — raw balls, no buffers on the module. None of them collides with the SDRAM (52), the PHYs (~27), the SPI flash (4) or the clock on P3.

| Block | SODIMM | Contents | Pins | Free |
|---|---|---|---|---|
| A | 57 – 104, dense | 65816 bus | 38 | 10 |
| B | 109 – 156, dense | SRAM 13, VGA 20, I2S 3 | 36 | 12 |
| C | 41 – 54, scattered | RP2354B EC link | 8 | 2 |
| | | **Total** | **82 / 106** | **24** |

  NOTE: **The CPU bus occupies one contiguous block and must not be split.** Synchronous bus signals spread across distant connector regions and different ECP5 banks is where skew problems are manufactured. The 10 spare pins in block A become a probe header beside the CPU — the place they will actually be wanted. Block C's scattering is harmless for SPI at a few MHz and fatal for anything parallel, which is why the EC link is the correct occupant.
- P2.06 — **The 65816 bus, 38 pins.** A0–A15 (16) · D0–D7 multiplexed with the bank byte (8) · FPGA outputs PHI2, RESB, ABORTB, IRQB, NMIB, BE (6) · FPGA inputs RWB, VPA, VDA, VPB, MLB, E, MX (7) · RDY bidirectional (1).
  NOTE: **A0–A10 and D0–D7 must be bidirectional FPGA pins, and this has to be settled before ball assignment.** During CPU cycles the FPGA observes them; during a walk, a fill or the EC's preload it drives them with `BE` low to tristate the CPU. That is [F.4](sec_ai_f#f4) verbatim, and it is the single most layout-critical net here as it is there.
- P2.07 — **SRAM — the same 1 MB ×8 part as the target board**, AS7C38096A-10TIN ([D15](sec_ai_q#d15), [F.5](sec_ai_f#f5)): 13 pins, A11–A19 (9) plus CEB, OEB, WEB (3) and the shared-net arrangement of [F.2](sec_ai_f#f2), where A0–A10 and D0–D7 cost nothing because they are already on the bus. **A ×16 part would be a mistake dressed as convenience** — it would hand the prototype a byte-lane topology the target does not have, and the whole point of the carrier is to rehearse the topology that does (→ [D43](sec_ai_q#d43)).
- P2.08 — **Video — VGA through an R-2R ladder, 18 bits.** The ECP5 has no DAC; conversion is 6 bits per channel into 1 % ladders terminated against the monitor's 75 Ω, plus HSYNC and VSYNC, into a DE-15. Six bits is not a compromise: the target panel is driven at **18 bpp over direct RGB-TTL** ([D05](sec_ai_q#d05), [E0.4](sec_ai_p3#e04)), so the palette entry is 18 bits on both boards and there is no truncation, no format conversion and no software difference. RGB444 would save six pins that are not needed and buy a divergence.
  NOTE: Bring-up runs **640 × 480 at 25.175 MHz**, the most tolerant mode in existence and the safest way to prove a scanout path. Move to 1024 × 600 at ~50 MHz once the timing generator is trusted, and develop the compositor there. 1024 × 600 is also where the console geometry lands exactly: 128 columns × 8 px = 1024, with the 32 rows of [T1.25](sec_ai_t1#t125) centred inside 600 lines and a border above and below.
- P2.09 — **Audio — 3 pins.** BCLK, LRCK, DATA into the PCM5102A, which synthesises its own internal clock and needs no MCLK.
- P2.10 — **The EC — 8 pins as recorded**, SCK, MOSI, MISO, DBG_CSN, IRQ, READY, DEBUG_ENABLE, FPGA_READY — **and `DBG_CSN` is withdrawn at REV C, so the block is 7 and its spare rises by one if the count is confirmed** (→ [Q158](sec_ai_q#q158), [D80](sec_ai_q#d80)). It keeps its specified role minus power sequencing: debug-agent SPI master driven from its `J-DBG` console UART, BIOS and kernel preload from microSD, USB HID through the native host controller ([D1.5](sec_ai_d1#d15)), and release of the 65816 from reset. It **gains ECP5 JTAG over four GPIO**, because a carrier hosting the SODIMM socket directly has no DAPLink on it — a natural extension of the configuration role it already owns (→ [sheet D1](sec_ai_d1)).
  NOTE: **[D67](sec_ai_q#d67) withdraws that extension: the EC is out of the prototype's configuration path entirely.** The i9 is programmed from a PC by whatever route is most practical, and if an EC sits on the carrier at all, configuration does not depend on it. **The two mechanisms differ irreducibly** — the prototype is ECP5 and the target is iCE40, which has no JTAG at all ([D61](sec_ai_q#d61)) — so a shared path would import prototype constraints into production firmware and buy nothing. The four GPIO come back, and so does `DEBUG_ENABLE` if [Q125](sec_ai_q#q125) goes the way [D3.2](sec_ai_d3#d32) points.
  NOTE: The debug agent's two access axes — physical against virtual, internal against external bus cycle — partly collapse on one die, since Neon's memory is reachable through the shared arbiter. **Implement both anyway.** The external-bus-cycle path of [R.5](sec_ai_r#r5) must exist and be tested here, or the target board discovers it missing at the worst possible time.
- P2.11 — **Memory — 8 MB shared, and the scarcity is a feature.** ((Read [P2.11a](sec_ai_p2#p211a) before believing the allocation below: the module's SDRAM may not be usable for most of it.))

| Allocation | Size |
|---|---|
| Framebuffer, front (1024 × 600 × 8 bpp) | 600 KB |
| Framebuffer, back | 600 KB |
| Window backing stores | 2 MB |
| Physical page pool | 4 MB |
| Audio DMA buffers | 128 KB |
| Reserve | ~700 KB |

  NOTE: Enough for the whole G0–G8 roadmap, and the 16 MB per-process virtual space exercised against a small physical pool is *preferable* during development: paging and eviction run constantly instead of lying dormant behind abundant memory. Bandwidth: ×32 SDR at 100 MHz peaks at 400 MB/s and sustains 250–300; scanout 37, blitter 60–100, Helium fills 25, audio negligible — 122–162 MB/s, roughly 50–65 % utilisation. **None of those figures transfer**: the target has two independent ×16 devices with separate controllers ([D13](sec_ai_q#d13), [D14](sec_ai_q#d14)).
  NOTE: Arbitration is fixed-priority with a starvation guard — scanout, audio, blitter, Helium fills, bulk — and the guard promotes anything waiting past a programmable threshold. Instrument it with per-requester wait-time histograms in EBR, readable over the debug channel. It is the same shape as [D39](sec_ai_q#d39) with one more claimant, so what is learned here is worth carrying.
- P2.11a — [[!blocking]] **The module's SDRAM has `CKE`, `CS#` and all four `DQM` lines tied off to the rails rather than driven by the FPGA, and if that holds, most of [P2.11](sec_ai_p2#p211) cannot run on it.** Two consequences, and the first is the fatal one: **there is no per-byte write masking**, so every write is a full 32-bit word — and the 65816 writes bytes. A page pool behind an unmaskable memory needs a read-modify-write on every byte store, which is two SDRAM accesses where the design assumes one, on the machine's hottest path. The second is that `CS#` and `CKE` can never be deasserted, so the part can neither be idled nor put in self-refresh.
  NOTE: **The remedy is the one the target board already specifies: put the real SDRAM on the carrier**, wired to spare FPGA I/O with `DQM`, `CS#` and `CKE` under gateware control, exactly as [sheet F](sec_ai_f) has it. The module's own 8 MB then survives as coarse scratch and an early framebuffer during bring-up — where a whole-word write is harmless — and nothing above it has to know. **This makes [P2.19](sec_ai_p2#p219)'s Stage A less attractive rather than more**: a wire-wrapped stage cannot rehearse a memory that has to be on the PCB anyway.
  NOTE: **The finding comes from community reverse-engineering of the module, not from a Colorlight document, so confirm it with a continuity meter on the specific board on arrival** — `CKE` to 3V3, `CS#` and the `DQM` lines to ground — before committing the carrier's SDRAM footprint. It is cheap to check and expensive to discover after layout (→ [Q112](sec_ai_q#q112)).
  NOTE: The direction of the surprise is worth noting: it **reduces** the risk of skipping Stage A rather than raising it, because it forces the memory interface onto the carrier where `DQM` and `CS#` are ours to drive.

## Partitioning discipline — the section the plan succeeds or fails on

The prototype merges two devices the target separates. Every shortcut taken because Helium and Neon happen to share a die is a rewrite later, and the rules below are what stop that. Review them at every major merge, not only at the transition.

- P2.12 — **Rule 1 — two top-level modules, always.** `helium.v` and `neon.v` are instantiated side by side in a top level whose only job is to wire them to each other and to the pads. Neither module references a signal inside the other. There is no shared-internals file.
  NOTE: The rule is mechanically checkable, which is the point of stating it this way: a reference from one module into the other's hierarchy is a grep, not a judgement.
- P2.13 — **Rule 2 — the interface is the shared bus and three control nets, and nothing else.** This is the rule an earlier proposal for the carrier got wrong, and it is worth saying why. It wanted a dedicated 56-signal command/peek/event link between the two devices, multiplexed down to 32, and reported the pin cost as a finding for the package decision. **That link does not exist**: [D04](sec_ai_q#d04) deleted it. Neon taps the CPU bus directly and the only dedicated wires are `NEON_BUS_SEL`, `NEON_BUS_BSY` and `NEON_IRQ` ([B.6](sec_ai_b#b6)). So the prototype's `neon.v` takes A0–A15, D0–D7, PHI2, RWB and `NEON_BUS_SEL`, and drives `NEON_BUS_BSY` and `NEON_IRQ` — every one of which is a PCB net on the target board. A signal added to that list is a cost paid twice; a signal smuggled around it is a defect.
- P2.14 — **Rule 3 — separate clock domains from day one.** Both modules could run from one PLL output. **Do not.** Derive two clocks from separate outputs and do proper CDC on every crossing: async FIFOs for data, two-flop synchronisers plus handshake for control. On the target the two devices take the same 25 MHz star ([B.7](sec_ai_b#b7)) into different PLLs, which is asynchronous in practice — [T1.18](sec_ai_t1#t118) already reasons that way. This costs a little latency now and buys the certainty that metastability does not surface after the PCB exists.
  NOTE: One domain would also entangle timing closure: Neon's pixel clock would constrain Helium's paths, and a route that failed would present as a video defect rather than as a timing failure.
- P2.15 — **Rule 4 — the memory port is an abstraction.** Neon's accesses leave through a memory port on Neon's boundary — `mem_addr[22:0]`, `mem_wdata`/`mem_rdata[31:0]`, `mem_we`, `mem_be[3:0]`, `mem_req`, `mem_ack`, `mem_prio[1:0]`. Here it routes to the shared arbiter; on the target it routes to Neon's own 64 MB device. **Neon contains no knowledge of which** — no arbitration logic inside it, no awareness that Helium exists as a competing requester. `mem_prio` keeps its meaning in both: 3 scanout, 2 audio, 1 blitter, 0 bulk.
- P2.16 — **Rule 5 — palette entries are 18 bits, always.** Six bits per channel on the VGA ladder is the same depth the target panel takes over parallel RGB-TTL, so the palette format is byte-identical on both boards and no conversion layer ever exists (→ [P2.08](sec_ai_p2#p208), [D05](sec_ai_q#d05)).
  NOTE: Six bits per channel is also what the R-2R ladder can express, so the prototype's VGA is not a reduced-colour path — the same palette on a different connector.
- P2.17 — **Rule 6 — what the aperture must preserve is the stall protocol, not a fake restriction.** REV A protected a write-only aperture with a slow `PEEK` register path; [T1.15](sec_ai_t1#t115) deleted that mechanism and returned its address space, because `NEON_BUS_BSY` already stalls PHI2 and makes `$FE` genuinely readable at about six times the speed. So on one die, where a read could trivially answer in zero wait states, **implement the four-step protocol of [T1.18](sec_ai_t1#t118) anyway**: busy asserted by default, the read issued after the stall rather than racing it, the meaningful edge being the *deassertion*, and Helium's watchdog turning a hung or absent Neon into a fault instead of a frozen machine. All four requirements of [T1.19](sec_ai_t1#t119) are testable here, including the write-FIFO drain — the one that otherwise ships as an intermittent bug — and requirement 4 still holds: **the software model stays write-only** even though the hardware answers reads.
- P2.18 — **Rule 7 — the EBR abundance is the leak nobody catches.** Every buffer — text, font, palette, cursor, scanout FIFO, blitter line buffers, cache tags, TLB, walker cache, command FIFO, trace — is declared with a size parameter defaulting to what fits an HX8K, and a build with the target defaults must synthesise and pass the same tests before any merge. A hardcoded size anywhere is a defect, and this applies to the cache first: **the cache controller is parameterised by size, line count and associativity from its first line of code**, because the target is 768 KB of 4-way cache in 2 KB lines with tags in EBR ([F.5](sec_ai_f#f5)) and this board carries whatever the carrier carries.

## Construction

- P2.19 — **Stage A — extension board plus wire-wrap.** 65816 in a PLCC-44 socket on perfboard, SRAM adjacent, ribbon to the extension board's PMOD headers. **Run PHI2 at 1–2 MHz**: flying leads will not meet the 65816's data setup requirement before the falling edge any faster, and chasing intermittent faults on a wire-wrapped bus is a poor use of a week. Purpose: prove the concept and reach P2 without waiting for a PCB.
  NOTE: [[!blocking]] **The PMOD headers must be verified as direct, unbuffered, bidirectional FPGA I/O before anything is soldered.** Several Colorlight products route GPIO through unidirectional 74HC245 buffers; the module itself does not, so this concerns the extension board only, and its described layout — I/O in groups of eight, each with its own 3V3 and GND — suggests direct connection. Confirm with a continuity meter on arrival, or skip Stage A entirely and the question is moot (→ [Q67](sec_ai_q#q67)).
  NOTE: A fault found at 1–2 MHz is real; a fault *absent* there says nothing about 8 MHz on a board with a ground plane. Stage A validates function, Stage B answers timing.
- P2.20 — **Stage B — the carrier PCB, and this is the real deliverable.** Four layers: DDR2 SODIMM 200-pin socket, PLCC-44 socket and W65C816S, AS7C38096A SRAM, RP2354B and microSD, R-2R ladders and DE-15, PCM5102A and 3.5 mm, USB-C, probe header on the ten spare block-A pins. Four rather than two because the CPU bus needs a ground plane and the ladder outputs need a clean return. Hosting the socket directly bypasses the buffering question, reaches all 106 pins, and gives controlled impedance on the bus.
  NOTE: **PHI2 targets 8 MHz here**, the target board's figure ([B.1](sec_ai_b#b1)). Every stall, fill and cache measurement taken at 1–2 MHz is an existence proof and nothing more; the numbers that matter are the ones taken at the real clock (→ [Q72](sec_ai_q#q72)).
  NOTE: **Capture it in KiCad with the symbols and net names intended for the target board.** The CPU-to-SRAM-to-FPGA section is the most timing-sensitive part of the eventual design and this is the chance to validate it where a mistake costs a cheap respin. USB-C at 5 V / 3 A or a barrel jack; a legacy 500 mA USB-A port is marginal and may not start the board. **Measure the module's actual draw before finalising the schematic** — 400–600 mA for the module, ~500–700 mA total with the PHYs held down, ~700 mA–1.1 A with them running, and all of those are estimates (→ [Q70](sec_ai_q#q70)).
  NOTE: The probe header on the ten spare block-A pins is this board's version of [C.19](sec_ai_c#c19)'s rule for test points: free at fabrication, unbuyable afterwards.
- P2.21 — **The order of the two stages, which is the one thing easy to get backwards.** Stage A exists *because* the carrier does not, so it comes first or not at all: wire-wrap at 1–2 MHz reaches [P2](sec_ai_p2#p2) while the PCB is being drawn, and if the decision is to go straight to the carrier then [Q67](sec_ai_q#q67) is moot and Stage A is simply skipped. The carrier's own sequence is then fixed — **schematic captured with the target's symbols and net names → four-layer layout with controlled impedance on the CPU bus → DRC clean and fabrication outputs → assembly → [P0](sec_ai_p2#p0) and [P1](sec_ai_p2#p1) re-validated on the board before [P2](sec_ai_p2#p2) runs on it at 8 MHz.**
  NOTE: Re-running two stages that already passed on temporary wiring is not ceremony. It is what separates a carrier defect from a gateware defect for the rest of the project, and it costs an afternoon.
  NOTE: [E0.3](sec_ai_p3#e03)'s symbol-by-symbol pass covers every part on this board and happens **before** the schematic, not alongside it. A footprint error found by a printed sheet of paper costs nothing; the same error found by a delivered board costs the board.

- P2.22 — **Design-for-debug is a layout pass in its own right, and it is what buys back the validation [P2.19](sec_ai_p2#p219)'s Stage A would have provided.** Skipping wire-wrap means debugging a first-spin board with no prior proof of anything, and the trade that makes that survivable is provisioning, not luck. Six things, all free at fabrication and unbuyable afterwards ([C.19](sec_ai_c#c19) states the same rule for the target board): **a series 0 Ω or jumper option in every clock and every inter-domain bus** · **test points on every rail and on `PHI2`, `RDY`, `RESB`, `ABORTB`, `VDA`, `VPA`, `BE`, every SD and SPI line, the I2S trio and the whole CPU bus** · **sockets for the CPU and, if the layout allows, the SRAM** · **a current-sense shunt or 0 Ω link in each switchable rail** · **a strap that brings the rails up with the FPGA module absent** · and **rail voltages on the silkscreen.**
  NOTE: The test-point list is written against [P2.23](sec_ai_p2#p223) rather than in the abstract: **every step of the bring-up procedure has to name a physical point or a strap it is measured at**, and a step that cannot is a step that will be guessed at.
  NOTE: **The module makes this sharper rather than softer.** Its FPGA is a caBGA part somebody else soldered, so **no ball is ever directly probeable** — everything observable has to come out on a SODIMM pin. [P2.05](sec_ai_p2#p205)'s ten spare block-A pins become the probe header for exactly that reason.
- P2.23 — **The first-spin bring-up runs in eight stages and the order is the safety, not the convenience.** **(1) Bare board**: visual and continuity, every rail net checked for a short to ground before any power. **(2) Rails only, current-limited**, with the module and the CPU absent — bring up the always-on rail first, verify, then each gated rail one at a time by asserting its enable by hand, checking voltage and inrush on its shunt. **(3) The EC alone**: confirm it boots, takes firmware over SWD, answers on `J-DBG`, and can toggle every enable and read every I2C device ([D1.13](sec_ai_d1#d113)). **(4) FPGA configuration**: insert the module, configure a blinky, confirm the device is detected and its ID is what it should be. **(5) Clocks**: load a PLL test bitstream and scope every derived clock — confirm each was promoted to a global net rather than routed as logic, and that `BCK` and `LRCK` are continuous ([W.7a](sec_ai_w#w7a)). **(6) Memory**: the SRAM first, then the carrier SDRAM, with march, walking-ones and address-in-address patterns — and **verify that `DQM`, `CS#` and `CKE` actually toggle**, which is the entire reason the SDRAM is on the carrier ([P2.11a](sec_ai_p2#p211a)). **(7) The CPU last**, socketed, with `PHI2` from a jumper-selectable low clock at 2–4 MHz, the bus timing scoped, and control handed between the CPU and the debug agent over `BE`. **(8) Video**: the R-2R output and text Mode 0.
  NOTE: **The CPU goes in last and it goes in socketed**, which is the one irreversible ordering decision in the list: a bus fault with the CPU present looks like a CPU fault, and every stage above it is cheaper to diagnose with the socket empty.
- P2.24 — **The instruments are part of the plan, because a first-spin-only strategy is exactly the one that cannot be executed by inference.** A **16-channel logic analyser with buffered capture at several hundred MSa/s** is necessary and an eight-channel toy is not adequate — this is a 100 MHz-class board and the bank-byte window is tens of nanoseconds wide. A **four-channel scope at 100 MHz or better**, with 12-bit resolution earning its keep twice on this board: the R-2R ladder's steps and rail ringing. A **bench supply with adjustable current limit**, without which stage 2 of [P2.23](sec_ai_p2#p223) cannot be run at all. A **JTAG probe for the module** with the open loader, plus a couple of 3.3 V serial adapters.
  NOTE: **This is where the money saved by cancelling Stage A should go**, and it is a better trade than it looks: wire-wrap validates function once, and an instrument validates every stage of the project after it.
- P2.25 — **Three toolchain traps on this device family, all of which produce a build that passes and a board that does not.** **Tristate and bidirectional nets must be resolved only at the top level** — a `Z` assignment buried in a submodule is a synthesis-time surprise on this backend, which matters immediately because [P2.06](sec_ai_p2#p206) makes A0–A10 and D0–D7 bidirectional. **PLL outputs are not always promoted to global clock nets automatically**: check the place-and-route log and force the promotion rather than assuming it, which is what stage 5 of [P2.23](sec_ai_p2#p223) verifies on hardware. And **the module's part is the slowest speed bin of its family**, so static-timing margin has to be budgeted rather than discovered — the 103.125 MHz Neon domain ([W.11](sec_ai_w#w11)) is reachable on it, and should be closed in place-and-route against real constraints early rather than after the gateware is written.
  NOTE: **If that domain will not close after pipelining, the ranked answers are: pipeline harder, then drop the pixel clock, then — last — cross-check the timing in the vendor's own tool.** The third is worth naming precisely because [A2.6](sc_a2#a26) makes the open toolchain a principle rather than a preference: using a proprietary analyser to *check* a design the open flow builds is a smaller concession than using it to *build* one, and it is still a concession. The open flow stays primary in either case (→ [Q117](sec_ai_q#q117)).

## What must not leak to the target board

Each row is a convenience here that becomes a defect there.

| Property of the prototype | Why it must not survive |
|---|---|
| Shared SDRAM controller | The target has two independent memories |
| A single clock domain | The target has genuinely separate PLL domains |
| 243 KB of EBR | Each HX8K has 16 KB, and Neon's is already fully allocated |
| Zero-wait access to Neon | The target stalls PHI2 and the model stays write-only |
| A ×16 SRAM, or any unshared byte lane | The target shares D0–D7 and A0–A10 with the CPU |
| Hardcoded cache or buffer sizes | Every one of them is a synthesis parameter |
| PHI2 at 1–2 MHz | The target runs 8 MHz and the margins are different |
| VGA timing assumptions | The target drives one fixed-resolution panel |
| Any Helium–Neon signal outside [P2.13](sec_ai_p2#p213) | The target has three control nets and a shared bus |
| Bandwidth figures from ×32 shared memory | The target's memory topology differs |
| Debug reaching Neon by the internal path only | The target needs the external bus cycle path |
| The absence of Argon | The softcore option stays untested until the target board |
| The absence of a power path | The target sequences rails before configuration |

## Prototype stages · P0–P5

- [ ] P0 — **Platform alive.** Bitstream through openFPGALoader; blinky proving clocking and PLL lock; the EC's `J-DBG` console echoing.
  TEST: SDRAM march across all 8 MB — walking ones and address-in-address · Ethernet PHYs confirmed held in reset on P4 · current draw measured both ways and written into [Q70](sec_ai_q#q70).
- [ ] P0.a — **BOM ordered first**, because the lead times are the only part of this stage nobody can compress: Colorlight i9 v7.2, W65C816S and PLCC-44 socket, the AS7C38096A-10TIN of [P2.07](sec_ai_p2#p207), an RP2354B board, DE-15 and 1 % ladder resistors, PCM5102A, microSD holder, passives and headers.
- [ ] P0.b — **Blinky through openFPGALoader**, with PLL lock observable on a pin rather than inferred.
- [ ] P0.c — **PHY reset asserted at configuration** and left asserted; module draw measured with the PHYs both ways and the numbers written down.
- [ ] P0.d — **EC bring-up** — LED, build-and-flash loop over SWD, console echo on `J-DBG`. A host console attached to the system.
- [ ] P0.e — **EC ↔ FPGA SPI link** with a scratch register file in the fabric, giving host-side read and write of FPGA state. This is the debug backbone and every stage after it is easier for existing.
- [ ] P0.f — **SDRAM controller exercised** across all 8 MB — main memory proven and characterised, not assumed.
- [ ] P0.g — **SRAM on temporary interconnect**, validated by the same march. What is being proved is the asynchronous parallel interface and its pin mapping, not the part.
- [ ] P1 — **Console before memory.** Text Mode 0 rendering a character grid over VGA at 640 × 480 from EBR alone, accepting console input.
  TEST: no SDRAM access anywhere in the path · the buffer is **128 × 32 with [T1.25](sec_ai_t1#t125)'s arithmetic unchanged**, displayed as an 80 × 30 window at 640 × 480 and in full at 1024 × 600.
  NOTE: This is [T1.1](sec_ai_t1#t11) and [E1.7](sec_ai_p3#e17)'s N0 on different silicon, and it earns its place for the same reason: a bitstream putting correct characters on a screen has proved the PLL, the timing generator, EBR initialisation and the output pins in one shot, and every stage after it is easier to debug for having a display. **The geometry does not become a parameter** — one console driver serves both boards (→ [D44](sec_ai_q#d44)).
- [ ] P1.a — **R-2R ladders assembled and the timing generator producing colour bars** at 640 × 480 / 25.175 MHz — a monitor displaying output from your own gateware.
- [ ] P1.b — **Mode 0 text engine in EBR** with the font ROM and the 128 × 32 buffer, [T1.25](sec_ai_t1#t125)'s `TEXT_START + text_row*128 + column` unchanged ([D44](sec_ai_q#d44)).
- [ ] P1.c — **The buffer written from the EC over SPI**, with console input echoing to the screen — a working terminal that never touches the memory controller.
- [ ] P2 — **CPU attached.** 65816 in its socket, released from reset, free-running NOP test executing.
  TEST: bus cycles captured in the trace buffer and readable over the debug channel · VPA/VDA decoding confirmed against expected fetch patterns · native mode entry verified.
- [ ] P2.a — **Two top-level modules from the first commit** — `helium.v` and `neon.v` side by side, separate PLL outputs, CDC on every crossing, the interface of [P2.13](sec_ai_p2#p213) and nothing else. This is decided at the start or paid for later as a rewrite ([P2.12](sec_ai_p2#p212)–[P2.15](sec_ai_p2#p215)).
- [ ] P2.b — **Helium skeleton** — PLL, reset sequencer, PHI2 generation, bus-cycle FSM, bank-byte latch, VPA/VDA decode. Every CPU bus cycle correctly framed and classified.
- [ ] P2.c — **Trace buffer in EBR with a raw debug path** — direct access to EBR and SRAM, no cache anywhere in it, so cycles are capturable the moment the CPU is attached. It is re-routed through the cache at [P3.f](sec_ai_p2#p3f), once there is a cache to be coherent with.
- [ ] P2.d — **CPU boots from EBR-hosted memory** with real reset vectors, and enters native mode — the CPU executing your code out of memory you control.
- [ ] P2.e — **Bank `$FF` I/O decode** with a write-only LED register. The privileged bank exists and the CPU can command a peripheral.
- [ ] P2.f — **Neon's text aperture written by the CPU** across the shared bus, with the four-step stall protocol of [P2.17](sec_ai_p2#p217) implemented rather than shortcut. The CPU prints to the screen.
- [ ] P2.g — **CPU-visible UART in bank `$FF`** bridged to the EC's console UART — bidirectional interactive I/O between CPU code and your terminal.
- [ ] P2.h — **crt0, user and kernel linker scripts and a minimal C runtime**; a C hello world printing through the UART register. The convention audited at [E0.8](sec_ai_p3#e08) now reaches real hardware.
- [ ] P2.i — **Native 65816 monitor resident in SRAM** — examine, deposit, go, disassemble. The machine is self-hosting for inspection, with no host attached.
- [ ] P2.j — **microSD boot path** — the BIOS reads the kernel image from the card's boot partition and jumps to it ([CN1.5](sec_ai_cn1#cn15)).
  NOTE: This supersedes the EC reading an image from the card, which predates [D60](sec_ai_q#d60): the EC has no wires to the card, and the BIOS is the only thing that reads it at boot ([D107](sec_ai_q#d107)).
- [ ] P2.k — **USB HID keyboard** on the EC, delivered to a CPU-visible register.
- [ ] P2.l — **Text console driver** — Mode 0 plus the keyboard, wired to the monitor. Power on and the board reaches its own prompt on its own display.
  NOTE: **[P2.h](sec_ai_p2#p2h)–[P2.l](sec_ai_p2#p2l) are a checkpoint, not a milestone.** Text mode, no MMU, no graphics — worth having for the debugging and for the morale, and every piece of it is needed by [P3](sec_ai_p2#p3) and [P5](sec_ai_p2#p5) anyway, so nothing here is built twice. It is not [E6](sec_ai_p3#e6) and must not be recorded as it.
  NOTE: **Its software is [CON-00](sec_ai_cn1#con-00)–[CON-02](sec_ai_cn1#con-02)** of [sheet CN1](sec_ai_cn1): the monolithic console, booting from the card to a read-only prompt.
- [ ] P3 — **Translation active.** Helium's MMU, TLB and walker operational with the CPU executing through translation; cache controller against the external SRAM with plausible hit/miss counters.
  TEST: PHI2 stalling on a fill, bounded and measured · ABORTB raised on an unmapped page, handled, instruction resumed · context switch between two ASIDs with correct CTX_SET_PTBASE / CTX_SET_ASID ordering · the fill watchdog tripped deliberately instead of freezing the board.
  NOTE: *Pass condition: the virtual memory system is real, not simulated.* This is the stage the whole prototype was worth building for — [E4](sec_ai_p3#e4) arrives with its hardest gateware already debugged.
- [ ] P3.a — **SRAM exposed to the CPU as raw uncached memory** — real off-chip memory usable by CPU code.
- [ ] P3.b — **The shared SDRAM controller and its arbiter**, fixed priority with the starvation guard of [P2.11](sec_ai_p2#p211) and **per-requester wait-time histograms instrumented from the first version**, not added later when a number is finally wanted.
- [ ] P3.c — **SDRAM reachable by the CPU through the arbiter**, uncached and slow — large main memory addressable before it is fast.
- [ ] P3.d — **Cache controller against the SRAM** — 2 KB tagged lines, 4-way, 256 B fill sub-blocks with valid and dirty bits per sub-block ([F.5](sec_ai_f#f5), [F.6](sec_ai_f#f6)), write-back, PHI2 stalled with BE=0 for bounded fills, hit and miss counters. **Size, line, sub-block and associativity are synthesis parameters from the first line of code** ([P2.18](sec_ai_p2#p218)).
- [ ] P3.e — **Flush and invalidate with the BUSY polling protocol** — what software needs to enforce coherence, and the prerequisite for both DMA and paging.
- [ ] P3.f — **Debug agent re-routed through the cache controller**, with a per-transaction watchdog and — **if [Q125](sec_ai_q#q125) keeps it** — the `DEBUG_ENABLE` strap. Host memory access is now coherent with the CPU's own view.
- [ ] P3.g — **Halt, single-step, resume and register readback**, with the fill watchdog suppressed while the CPU is halted — otherwise every session ends in a spurious abort ([R.17](sec_ai_r#r17)).
- [ ] P3.h — **EC monitor front end** over the console UART — `load`, `go`, `dump`, `halt`, `step`, `trace` ([R.22](sec_ai_r#r22)). A complete bring-up workbench: binaries load and run in seconds.
- [ ] P3.i — **ASID-tagged TLB in EBR with a single identity mapping** — every access translated and behaviour unchanged, which is precisely what proves the datapath before anything depends on it.
- [ ] P3.j — **Hardware page-table walker** reading 32-bit PTEs from the fixed, uncached SRAM region of [F.5](sec_ai_f#f5).
- [ ] P3.k — **ABORTB on unmapped pages and permission violations**, an assembly handler that reports, and **instruction resumption verified correct** — faults detected, delivered to software, and recoverable.
- [ ] P3.l — **Context registers** with the `CTX_SET_PTBASE` → `CTX_SET_ASID` ordering invariant enforced in hardware; two contexts switched from the monitor, two distinct 16 MB spaces coexisting.
- [ ] P3.m — **Protection policy enforced** — bank `$FF` privileged and never user-mappable, bank `$00`'s vector and stub pages pinned in every context ([L.11](sec_ai_l#l11)), banks `$F0`–`$FD` the resident kernel ([J.1](sec_ai_j#j1), [D102](sec_ai_q#d102)), vectors mapped identically everywhere.
- [ ] P4 — **Graphics.** Framebuffer scanout from SDRAM stable at 1024 × 600, 18-bit palette lookup, blitter, hardware cursor.
  TEST: minterm logic verified against a reference implementation · cursor overlay tracking without involving the composite path · arbiter wait-time histograms showing no scanout underrun under blitter load · **a CPU read of the framebuffer returning exactly what was written, including immediately after a write** — the write-FIFO drain of [T1.19](sec_ai_t1#t119) — and **a read with Neon held in reset timing out into `$FF` plus a fault, not into a frozen machine**.
- [ ] P4.a — **Framebuffer scanout from SDRAM at 1024 × 600, 8 bpp**, through the 18-bit palette of [P2.16](sec_ai_p2#p216) — Neon stage N1 ([T1.63](sec_ai_t1#t163)), in the same pixel format the production RGB path uses.
- [ ] P4.b — **Hardware cursor overlay in EBR** — pointer motion costs nothing in the composite path.
- [ ] P4.c — **Blitter, register-driven, straight copy only** ([T1.37](sec_ai_t1#t137)) — rectangles move without the CPU.
- [ ] P4.d — **The full blitter, its raster-operation logic verified against a reference software model** — barrel shifter, edge masks, descending mode, queue. **Which engine is built is [Q58](sec_ai_q#q58)**, still open, and this is the board where trying it both ways costs a rebuild instead of a respin.
- [ ] P4.e — **Command FIFO** — Neon stage N4, and the CPU stops polling `BLIT_BUSY`. SDRAM command lists are N5 and the compositor does not need them ([V.35](sec_ai_v#v35)).
- [ ] P4.f — **Arbiter wait-time histograms captured under sustained blitter load** — no scanout underrun, with evidence rather than assumption.
- [ ] P5 — **System.** Audio DMA to the PCM5102A without underrun; compositor with damage-limited recomposition; kernel booting to a prompt.
  TEST: an hour of audio with the underrun flag still clear · a window dragged across two others and every exposed region correct afterwards · the kernel reaching its prompt from a cold card with no host attached.
  NOTE: The milestone is reached on temporary hardware, which is the point and also the caveat: it proves the software and the gateware, not the machine. **[E6](sec_ai_p3#e6) is still the milestone**, and closing it costs the P-series work plus a board that exists.
- [ ] P5.a — **Audio DMA to the PCM5102A over I2S**, continuous playback with no underrun — the machine makes sound reliably.
- [ ] P5.b — **Kernel skeleton in C** — startup, vector table, direct-page conventions, IRQ dispatch. A kernel image that owns the machine.
- [ ] P5.c — **COP syscall dispatcher** with `write` and `exit`, against the ABI documented at [E0.8](sec_ai_p3#e08) — the user–kernel boundary as a contract rather than a habit.
- [ ] P5.d — **Physical frame allocator and page-table construction** — the kernel can build an address space.
- [ ] P5.e — **First user process** loaded into its own space at reduced privilege, demonstrably unable to reach bank `$FF` or the kernel.
- [ ] P5.f — **Timer IRQ, scheduler and the assembly context switch** — two user processes running preemptively and concurrently.
- [ ] P5.g — **Demand paging and copy-on-write** on top of ABORT — lazy allocation and cheap sharing, against the deliberately small physical pool of [P2.11](sec_ai_p2#p211).
- [ ] P5.h — **Ports, signals and messages** — the IPC substrate [sheet V](sec_ai_v) is written against.
- [ ] P5.i — **Driver framework** — init/read/write/ioctl/irq with fd-based device paths, and `/dev/tty`, which turns the console into a driver like any other.
- [ ] P5.j — **microSD block driver and a read-only NVFS mount behind [sheet Y1](sec_ai_y1)** ([V2](sec_ai_y1#v2), [V3](sec_ai_y1#v3)) — files on the card visible to the OS through the real syscall path rather than a bespoke one.
  NOTE: **The FIFO path is enough for this stage and the DMA engine is not needed yet** — the driver is written against the register names of [G.6](sec_ai_g#g6) from the start, so the engine lands underneath it later with nothing above changing. What it cannot reach on the FIFO alone is paging (→ [D45](sec_ai_q#d45), [Q79](sec_ai_q#q79)).
- [ ] P5.k — **Program loader and a shell** — type a name and a program runs in its own address space.
  NOTE: **[CON-04](sec_ai_cn1#con-04) is this step's pass condition**: the console's shell relinked against the `COP` stubs and running as PID 1 ([CN1.1](sec_ai_cn1#cn11)).
- [ ] P5.l — **`/dev/fb` with an ioctl mapping framebuffer pages into a process**, plus `/dev/audio` — a user program draws at memory speed and makes sound through the ordinary device contract.
  NOTE: **The compositor's cost model is measured at G2, not here** ([V.36](sec_ai_v#v36), [V.37](sec_ai_v#v37)). The number wanted is the blitter's own time for a full-screen pass, separated from emission and from whatever the client tasks are doing — and it is the project's first real software gate, so it is instrumented deliberately rather than inferred from a frame rate.

!!! APPLE II · ON THE PROTOTYPE — the software boots to a prompt on borrowed silicon.

Beyond P5 the G-series of [sheet V](sec_ai_v) runs entirely on this board while the target hardware proceeds in parallel — with the exception of everything resting on the `$FF` power block, which has no prototype ([P2.02](sec_ai_p2#p202)).
