dmolinagarcia/nova64/docs/docsV3/content/sec_ai_p3.md

# Phase 2 · the target board · E0–E8
> three iCE40 parts · a board of our own · the two milestones

The **E-series** builds the machine this document specifies: three iCE40 parts on a board of our own, with Helium and Neon as separate devices on a shared bus. It is **Phase 2** of the three phases of [sheet P1](sec_ai_p1), and both milestones are closed inside it.

Everything before it is rehearsal. The training rig of [sheet P1](sec_ai_p1) proves protocol and firmware on disposable hardware, the carrier of [sheet P2](sec_ai_p2) proves the gateware and the whole software stack on borrowed silicon, and what is left here is the board itself — the layout, the power path, the panel, and the two things neither prototype can answer: whether the target devices are large enough, and whether they are fast enough.

F.phase2.The same three phases with **Phase 2** highlighted: this sheet is the bottom track, where both milestones are closed, with the two prototypes that rehearse it above.

## Target board · E0–E8

Nine stages, each with concrete hardware/gateware/software and a verification criterion before moving on. E0 and E1 are broken out below, because everything before a working board exists is where the project actually is today: the pin budget is closed, all six schematic sheets are designed *as documents*, and nothing has been drawn in KiCad. **E0 is also where the project-wide work lives** — the toolchains, the audited 65816 ABI, the simulator and CI — together with the two things that have to be finished on borrowed hardware before a layout is committed: the iCE40 resource proof and the power path on eval boards.

- [ ] E0.1 — **Toolchain.** KiCad 8, oss-cad-suite (Yosys + nextpnr-ice40 + IceStorm), pico-sdk, and a simulator matching the HDL choice. **The P-series adds `nextpnr-ecp5` and prjtrellis to the same suite** — one more target for the same flow, no proprietary tools on either board ([P2.01](sec_ai_p2#p201)).
  TEST: a simulated iCE40 blinky and a compiled RP2354B "hello".
- [x] E0.2 — **HDL decision** — **Verilog-2005**, decided on toolchain grounds (→ [D101](sec_ai_q#d101), [Q2](sec_ai_q#q2)). It was held open because it seemed to decide which reference softcore is usable at all; [D88](sec_ai_q#d88) removed that weight, and a VHDL core such as P65816 still enters as one black box through GHDL.
  TEST: the decision written into [Q2](sec_ai_q#q2), with the reference cores it admits named beside it, before the first module of the carrier is committed.
  NOTE: **This now blocks the P-series rather than the schematic**, and it is the first thing the prototype makes urgent: every line of gateware written for the carrier is the same line that ships on the target board, so the choice is made before P0 rather than before E1.7.
- [ ] E0.3 — **Project KiCad library.** Symbol and footprint for every component, verified one at a time.
  TEST: each footprint printed 1:1 on paper and laid against the physical part.
  NOTE: The parts the prototype never carries are the ones with nothing to catch an error first — **the power devices, the panel FPC, the touch connector, the audio DAC and the iCE40 TQ144** — so those get the paper pass twice, on different days. The carrier's own parts are checked here too, and that check blocks its schematic ([P2.21](sec_ai_p2#p221)).
- [~] E0.4 — **Panel.** Candidate fixed and its controller verified — HX8282, 24-bit TTL at 3.3V with no level shifters, driven at 18 bpp on pin budget, DE mode by default, data latched on the *falling* DCLK edge so gateware changes it on the rising one. **The modeline has moved**: not ~51.2 MHz for 1344×635 but **51.5625 MHz for 1344×640 → 59.95 Hz**, which is what the 25 MHz oscillator can actually reach through one iCE40 PLL ([T1.4](sec_ai_t1#t14)). Still missing the *module* datasheet, and the blanking values remain provisional until it arrives (→ [Q1](sec_ai_q#q1), [Q43](sec_ai_q#q43)).
  TEST: the datasheet's DE-mode timing transcribed into the timing generator's own parameters, and the falling-edge latch confirmed against the part's diagram rather than from memory.
- [x] E0.5 — **Pin budget across the three TQ-144 parts** — closed, it fits. This is what proved the architecture buildable, and what forced the shared-bus topology when it did not.
- [ ] E0.6 — **Freeze the block diagram** as the schematic's hierarchical reference.
  TEST: every block on the frozen diagram maps to exactly one of [E1.1](sec_ai_p3#e11)'s six sheets, and nothing on the board sits outside one.
  NOTE: **This is not ![F.arch], and the distinction is what the stage is for.** [Sheet B](sec_ai_b)'s figure is the *architecture* — who inhabits the shared bus and who governs it from outside — and it is current. What E0.6 owes is the *schematic's* hierarchy: the same machine cut along the six sheets of [E1.1](sec_ai_p3#e11), so that every block on the drawing is a page in KiCad and nothing on the board sits outside one. The REV B drawing this used to track has been retired rather than brought forward.
- [ ] E0.7 — **Repository and documentation skeleton** — gateware, firmware, kernel, hardware, docs, with the decision log at the centre of it. One place where every artifact lands, which is cheap on day one and expensive on day two hundred.
  TEST: a fresh clone builds the gateware, the firmware and the 65816 binaries with no path pointing outside the repository.
- [ ] E0.8 — **The 65816 toolchain audited, not merely installed.** Calypsi C and ca65, with the calling convention and the direct-page pseudo-register usage checked against actual compiled output and written down as the ABI the kernel is built on.
  TEST: a C function calling an assembly one and the reverse, with 8-, 16- and 24-bit arguments, disassembled and matched line by line against the written ABI.
  NOTE: [[!blocking]] **No kernel work starts before this exists.** A calling convention discovered by experiment halfway through [P5](sec_ai_p2#p5) is the kind of blocker that stops a project for a fortnight, and it is the one known blocker on the software side (→ [sheet O](sec_ai_o)).
- [ ] E0.9 — **Simulator harness** for the 65816, with an I/O stub at the real bank `$FF` UART address so the same binary runs on the simulator and on hardware unchanged.
  TEST: one unmodified binary prints through the bank `$FF` UART address in the simulator and on hardware, with the same output.
  NOTE: The point is discrimination rather than convenience. From here on a kernel bug is separable from a gateware bug — which is exactly the confusion that consumes weeks during bring-up.
- [ ] E0.10 — **CI** building both gateware targets, the RP2354B firmware and the 65816 binaries, and running the simulator suite on every commit.
  TEST: a deliberately broken commit is rejected by the pipeline, not by a person.
- [ ] E0.11 — **Gateware split into two independent builds.** `helium.v` and `neon.v` leave the shared top level and become separate projects communicating over the shared CPU bus and the three control nets of [P2.13](sec_ai_p2#p213) — every one of which stops being a wire inside a die and becomes a PCB net.
  TEST: each project synthesises, times and loads on its own, and the only signals crossing between them are the CPU bus and the three nets of [P2.13](sec_ai_p2#p213).
  NOTE: There is no serializer and no dedicated inter-FPGA link to design here: [D04](sec_ai_q#d04) deleted that link, and [P2.13](sec_ai_p2#p213) is written the way it is precisely so that this step costs a build-system change. **If it costs more than that, the discipline section was not enforced** and the cost is being paid now instead of then.
- [ ] E0.12 — **Both halves ported to iCE40 HX8K on dev boards, and measured.** Argon's slot stays empty ([B.4](sec_ai_b#b4)), so what has to fit is Helium and Neon: LUT, EBR and Fmax against the estimates of [P2.03](sec_ai_p2#p203) and [P2.04](sec_ai_p2#p204), built with the target EBR defaults and none of the prototype's instrumentation.
  TEST: **103.125 MHz closing on Neon's half** with the blitter placed beside the SDRAM controller, or the single-rate fallback taken deliberately and its bandwidth consequence accepted (→ [Q44](sec_ai_q#q44)) · Helium fitting with the 768 KB cache's tags inside 16 KB of EBR ([F.5](sec_ai_f#f5)).
  NOTE: [[!blocking]] **This blocks [E1.1](sec_ai_p3#e11).** The one question the prototype cannot answer is whether the target devices are large enough and fast enough, because it has neither the fabric nor the block RAM of the parts that ship. Resizing a part here costs a line in the BOM; discovering it after a layout costs the layout.
- [ ] E0.13 — **The full software stack run on the two-device configuration** — kernel, drivers and the G-series as far as it has reached — before a board is drawn.
  TEST: nothing in the stack turns out to have depended on the single-FPGA prototype.
- [ ] E0.14 — **Power subsystem validated on eval hardware.** CH224K PD sink, BQ25896 charger, TPS63020 and the dedicated core buck, each rail brought up on the vendor's own board into resistive loads at target current; then the EC sequencer firmware written against them — always-on domain, staged enables, fault handling, MAX17048 readout.
  TEST: every rail brought to target current into a resistive load, with the sequencing order and each `PG` interlock observed on a scope rather than assumed.
  NOTE: This is the part of [sheet C](sec_ai_c) and [sheet S](sec_ai_s) the carrier deliberately does not exercise ([P2.02](sec_ai_p2#p202)), so without this stage its first hardware would be REV A itself. Proving the iCE40's core-before-IO order and a monotonic ramp on an eval rig costs days; discovering a violation on a populated board costs a respin and looks, for months, like an FPGA that configures unreliably ([C.8](sec_ai_c#c8)).
- [ ] E0.15 — **Battery pack characterised on eval hardware** — protection, charge and discharge cycles, fuel-gauge learning — so the energy path is understood before it is designed into a layout rather than after.
  TEST: a full charge and discharge cycle logged, and the gauge's reported state of charge compared against the energy actually measured.
  NOTE: The gauge is the reason this cannot be deferred to the board. A fuel gauge reports from a model that only settles after a cycle or two, so the figure the GUI shows at [L3](sec_ai_p4#l3) is worth exactly what the characterisation here was.
- [~] E1.1 — **Six hierarchical schematic sheets**, designed simplest to hardest: 1.1 power · 1.2 RP2354B / EC · 1.3 FPGA configuration · 1.4 Helium, bus and memories · 1.5 Neon, panel and audio · 1.6 Argon and connectors.
  TEST: each sheet reviewed against the pin-budget tables as it closes, with its own DNP list written on the sheet rather than kept elsewhere.
  NOTE: All six exist as design documents; none is drawn in KiCad yet. Sheet 1.5 is held by the panel datasheet.
  NOTE: **Capture them in the order they are designed, not the order they are numbered**, and review the BOM and the DNP list against the pin-budget sheets as each one closes. The DNP that matters most is Argon: its 3V3 and 1V2 sit behind their own 0Ω jumpers so that an empty footprint cannot load the bus ([E.5](sec_ai_e#e5)). A second one is worth placing on sheet 1.5 and is easy to forget because nothing before [L4](sec_ai_p4#l4) needs it: **a PAM8302 and a pair of speaker pads, unpopulated, behind a jumper**. Audio ends at a 3.5 mm jack today and a laptop wants a speaker; the footprint costs a square centimetre now and a respin later.
- [ ] E1.2 — **Cross-review before layout.**
  TEST: clean ERC, plus a manual pin-by-pin pass of every TQFP against its datasheet — twice, on different days.
- [ ] E1.3 — **Layout.** Stackup decided against the router's difficulty, PLCC socket centred with the FPGAs around it and bus traces under ~10 cm, decoupling hard against the pins, continuous ground plane.
  TEST: clean DRC and gerbers checked in an external viewer, not in KiCad's own.
  NOTE: **Route in order of difficulty, not in order of the netlist.** The CPU bus first, then both SDRAM interfaces, then the parallel RGB to the panel FPC — and only once those are done, power distribution and everything that is left. The hard nets get the room while there is still room to give them.
- [ ] E1.4 — **Staged population — the golden rule:** never populate a block until the previous one works. The board is designed for this, with a test point and an LED per rail and 0Ω jumpers to isolate every branch.
  TEST: every rail measured at its test point before the next block is populated, and the isolation jumpers left open until it is.
  NOTE: Staged population also fixes the order the errata arrive in. A defect found with one block populated is attributable to that block; the same defect found on a fully assembled board is a search.
  NOTE: **The rails are not the only thing worth probing, and the bus has no provision at all today.** `PHI2`, `RESB`, `ABORTB`, `RDY`, `BE` and the three Neon control nets each need a labelled test point — as do `DCLK` and `DE`, one bit of each colour channel, and audio's `BCK` and `DIN`, spaced to land two probes without shorting — they are precisely the signals [E1.8](sec_ai_p3#e18) and [E5](sec_ai_p3#e5) are debugged through, and a scope lead soldered to a TQFP pin during bring-up is how boards get killed.
  NOTE: **Open the errata list at this stage and keep it as a document, not as a memory.** Every stage from here to [E8](sec_ai_p3#e8) adds to it, and [L7](sec_ai_p4#l7) is built from nothing else. A defect noticed during bring-up and not written down is a defect rediscovered on REV B.
- [ ] E1.5 — **Power alone**, in the order of [C.19](sec_ai_c#c19): charger and SYS with no downstream jumper fitted, then each rail into a resistive load, then the jumpers one at a time.
  TEST: 3V3_AON and 3V3_MAIN within ±2% and 1V2 within ±3% under dummy load · PD contract measured at 9 V on VBUS · SYS holding with the battery disconnected entirely · charging with correct STAT lines · draw at each jumper checked against the budget table · rails driven by hand from the EN header, with no EC firmware in the picture.
  NOTE: This stage also has to prove the **order**, not just the levels: 1V2 before 3V3_MAIN before VPP_2V5, each ramp monotonic, on a two-channel capture. A rail-order violation does not show up as a bad voltage — it shows up months later as an FPGA that configures unreliably (→ [C.8](sec_ai_c#c8)).
- [ ] E1.6 — **RP2354B alone.**
  TEST: answers on the `J-DBG` console and takes firmware over SWD · mounts the microSD and lists files · reads the gauge and charger over I2C-AON and reports converted units · generates a measurable backlight PWM, with no FPGA populated · sequences every rail up and down under firmware control, including the R1 tri-state pass, measured with the switched domain dead.
  NOTE: The **crossings audit** of [C.14](sec_ai_c#c14) belongs before this stage, not during it — a net-by-net list of every AON↔switched connection checked against R1–R3. It is the one review pass on the board that cannot be recovered by rework if it is skipped.
- [ ] E1.7 — **The three FPGAs — and the screen, which arrives here rather than at E5.**
  TEST: the EC configures each one separately with a blinky · CDONE high on all three · reconfiguring Neon without disturbing Helium demonstrated · **Neon stage N0**: a correct 128 × 32 blank text screen the instant Neon's CDONE rises, then glyphs written from the EC over the service port, then `TEXT_START` scrolling by exactly one row.
  NOTE: **The link comes up before the agent does, and the order is not optional.** The router is a single point of failure and the Debug Agent cannot be used to debug the router, so the mitigation is ordering rather than redundancy ([D3.12c](sec_ai_d3#d312c)). **First the SPI front end, the router and endpoint `0x01` alone**: an ID read returning magic, protocol version and build ID; a deliberately corrupted `HCRC` returning `NACK_HCRC`; and `EP = 0x00`, `0xFF` and an unassigned value each returning their own code. Unimplemented endpoints answer `NACK_EP_UNKNOWN` throughout, **so every step below is testable in isolation** ([D3.12](sec_ai_d3#d312)).
  NOTE: **Then endpoint `0x02`** — the debug agent's `DBG_ID` reading `$6516` (→ [R.8](sec_ai_r#r8)), and `WRITE_BURST`/`READ_BURST` against a scratch region: a write-then-read of a pseudorandom block matching, and **a deliberately corrupted `FCRC` frame retransmitted verbatim converging**, which is the direct test of the streaming commit ([R.25](sec_ai_r#r25), [D3.11c](sec_ai_d3#d311c)). **Then endpoint `0x03`, and this is where head-of-line blocking is tested rather than assumed**: fill the HID queue, stop draining it, and confirm `NACK_FULL` comes back with **debug throughput on `0x02` unaffected**. That is the failure the architecture exists to prevent and it will not appear by accident ([D3.12a](sec_ai_d3#d312a)).
  NOTE: [[!blocking]] **E1 is also the gate on whether the Debug Agent is fit to be boot-critical**, since `bios.bin` now reaches SRAM through it ([D82](sec_ai_q#d82)). If it is not, the fallback is a write-only sink endpoint at `0x05` using the same payload format — decided here on evidence rather than later under pressure (→ [Q154](sec_ai_q#q154)).
  NOTE: **N0 needs no SDRAM, no CPU, no Helium and no bus** — only Neon, the panel and the EC's SPI — so there is nothing to gain by holding it to E5 and a great deal to lose. It is also a far better acceptance test than a blinky: a bitstream putting correct characters on the panel has demonstrated the PLL, the timing generator, block-RAM initialisation, the RGB pins, the FPC and the backlight in one shot. **Bringing it forward gives the project a screen three stages earlier than planned, and every stage after it is easier to debug for having one** (→ [T1.64](sec_ai_t1#t164)).
  NOTE: **Inherited from [P1](sec_ai_p2#p1)**, where the same text mode ran against a VGA monitor. What is new here is everything the prototype could not carry: the panel's own timing, the FPC, the backlight and the 51.5625 MHz modeline of [T1.4](sec_ai_t1#t14). The character generator, the buffer geometry and the console driver arrive already debugged, so a failure at this stage is a *board* failure — which is exactly the discrimination the P-series was built to buy.
- [ ] E1.8 — **CPU alive — free-run.** Bus forced to NOP, PHI2 from Helium.
  TEST: the address counter advances consistently on the analyser · an LED blinks from a decoded address.
- [ ] E2 — **SRAM + serial monitor.** SRAM on the bus; BIOS preload by the RP2354B through endpoint `0x02` ([R.25](sec_ai_r#r25)); UART console; peek/poke monitor.
  TEST: console echo · read/write arbitrary memory · checksum of the loaded BIOS.
  NOTE: The peek/poke does not have to wait for a BIOS: the debug agent gives physical read/write and a march test with the CPU still in reset, which is where most of its value is (→ [R.22](sec_ai_r#r22)).
  NOTE: **Inherited from [P2](sec_ai_p2#p2)** — the monitor, the linker scripts, the C runtime and the microSD load path all arrive already debugged, so a failure at this stage is a board failure or a timing failure and cannot be anything else. That discrimination is what the carrier was built to buy.
- [ ] E3 — **SDRAM.** Controller (adapted open-source candidate) as a DMA/paging engine behind Helium, with auto-refresh interleaved into the fill state machine.
  TEST: pseudorandom pattern over the full 64 MB with no errors for hours · refresh holds during sustained fills.
- [ ] E4 — **MMU + cache + protection.** Walker, TLB with ASID, 4-way cache with tags in EBR, PHI2 stall with BE=0 and its watchdog, ABORTB, FAULT_* registers at `$FF`.
  TEST: an illegal access triggers ABORT with correct FAULT_ADDR/CAUSE · a cache miss stalls and resumes cleanly · a deliberately hung fill trips the watchdog instead of freezing the board · measured cache hit rate.
  NOTE: The debug agent reaches its full extent here — halt, step and trace over the `BE` handoff, virtual-mode access, and `TLB_PROBE` against `PTWALK` to catch a stale entry. The same stage owes it one negative test: the fill watchdog must be suppressed while the CPU is halted, or every session ends in a spurious abort (→ [R.17](sec_ai_r#r17)).
  NOTE: **Inherited from [P3](sec_ai_p2#p3)** — walker, TLB, ASID switching, the PHI2 stall and its watchdog all arrive as working gateware. Two things do not transfer and have to be re-earned: the **cache size**, which was a synthesis parameter on the prototype and is 768 KB of 4-way here ([P2.18](sec_ai_p2#p218), [F.5](sec_ai_f#f5)), and the **timing**, because the prototype's shared nets sat on a carrier at a lower PHI2 and this board runs 8 MHz with three loads ([F.4](sec_ai_f#f4)).
- [ ] E5 — **Video + audio.** Neon on the bus with its own SDRAM, `$FE` window; VGA pattern → framebuffer; tone over I2S. This is now **Neon stages N1 and N2** ([T1.63](sec_ai_t1#t163)): the SDRAM controller and arbiter, Mode 1 scanout, the register-driven blitter, then Modes 2a/2b with the 256-entry palette, `COPY_KEYED` and double buffering. The text console of E1.7 is the instrument the whole stage is debugged with. ((Start below the gateware: the panel's own **BIST** mode generates test patterns with no external clock and no bitstream, validating panel, FPC and backlight in isolation before anything can be blamed on logic.))
  TEST: BIST patterns on the panel · stable VGA image · a CPU write shows up on screen · **a CPU read of the framebuffer returning exactly what was written, including immediately after a write, which is the write-FIFO drain of [T1.19](sec_ai_t1#t119)** · **a read with Neon deliberately held in reset timing out into `$FF` plus a fault, not into a frozen machine** · **worst-case read latency measured with the blitter running a full-screen keyed copy** · a register-driven `FILL_RECT` covering the screen in 0.31 ms measured against `BLIT_BUSY` · an animated multicolour scene holding 60 Hz with `SWAP_BUFFERS` and no tearing · clean 440 Hz tone.
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
